201590022033/Dial-New-Design.01/docs/CROWN-RESUME-LEDGER-2026-10-09.md

# Crown continuation ledger

Updated: 10 October 2026, Africa/Johannesburg.

- Baseline HEAD: `6931131420adb5606323f8c8db54dc4c76604f8d` on main.
- Overall state: C0 COMPLETE WITH EXPLICIT EVIDENCE LIMITATIONS / C1 COMPLETE / C2 COMPLETE / C3 COMPLETE.
- Authority: human approved C0 followed by C1, requesting GPT-6.1 Sol light mode, then explicitly requested C2 and C3 followed by commit/push on 10 October. The coordinator cannot switch its own running model through available tools. No C4-C7 implementation, supplier onboarding, contacts, purchases or scheduler activation approved. C2/C3 were completed without new delegation.
- Plan: `docs/CROWN-ROADMAP-2026-10-09.md`.
- Scheduler ID: `resume-dial-designer-crown-roadmap`; status PAUSED, five-hour cadence. Not an active guarantee of restart.
- Research complete: movement/stem versus case-crown distinction, case-first default rule, archetype recommendations, supplied-package examples, U-BOAT cap/inner-crown distinction, repository architecture review.
- C0 gate completed 10 October 2026: NH05B primary stem 0351 247 and drawing v2 visually confirmed; NH35A/NH34A 0351 200 and VK63A 0351 177 primary drawings pinned. Eight embedded-head hashes/transformed bounds and structural exclusions reviewed. Supplier contents/variants/prices/stock conflicts recorded; NMK920 old sketch recovered but limited to external envelope, current SKU linkage and exact angle unknown. Front Engineering and front/side HD baselines captured for reference42/ladies34 in isolated localhost:3017 origin. Engineering has no side/crown viewport; documented baseline limitation accepted for C1, not a physical-fit pass. Missing case interfaces remain unknown.
- C0 durable evidence: CROWN-C0-EVIDENCE-2026-10-10.md, CROWN-C0-ASSET-INVENTORY-2026-10-09.md, CROWN-C0-SUPPLIER-EVIDENCE-2026-10-10.md and docs/research/crown-c0-2026-10-10/. Pre-C1 automated baseline: 4 files / 55 tests passed (parametricContracts, visualWatchAdapter, watchAssemblyArchitecture, visualAssetRegistry); no new-code verification claim.
- C1 gate COMPLETE: additive crown-spec/v1, crown-axis/v1 and crown-choice/v1 frozen in src/domain/crown/. Case owns canonical axis array; crown references axisId. Modern datum overrides inactive legacy crown anchor/angle/tube while preserving storage; absent modern data keeps existing precedence. Runtime uses Engineering frame; exported Y-up conversion is separately named. Assembly and embedded .dial validation reject ownership/reference/duplicate-head defects before hydration. Explicit reversible adapter preserves legacy dimensions/identities; no automatic migration. Contract changelog and migration matrix: CROWN-C1-CONTRACT-2026-10-10.md. C2-C7 NOT STARTED.
- Final verification, 10 October 2026: npm test -- --run passed 101 files / 826 tests (26 crown contract + 14 crown integration tests); npm run lint passed; npm run build passed including tsc -b. git diff --check and whitespace scan of all 24 changed/new TypeScript/Markdown files passed. Existing Three.js CommonJS deprecation, dependency comment annotation and bundle-size warnings remain non-fatal. Earlier 786/50/55 totals are historical, not substituted for current checks.
- C1 source files: src/domain/crown/{types,validation,axis,legacy,index}.ts; new assembly/crownAssemblyValidation.ts and visual3d/canonicalCrownAxis.ts; integration in assemblySerialization.ts, assemblyTypes.ts, catalogue/types.ts, parametric/placement.ts, projectFileService.ts, assemblyAnchors.ts and watchAssemblyToVisualModel.ts; crownContract.test.ts and crownAssemblyContract.test.ts. Production catalogue records, source GLBs and supplier records unchanged. C0 evidence/documents added; original planning documents retained with current authority/progress updates.
- New task requested: Project Crown and Namokimods. Portable context cache and per-milestone execution prompts prepared, including suggested 1-3 subagents, role/file ownership, applicable skills/tools, gates and handoff. Task creation/identity recorded below when confirmed.
- New planning task CREATED: Project Crown and Namokimods, thread `01a12229-68af-7e33-9201-87330c04d8b7`, host local. No saved repository projects were available; task is projectless planning with the exact existing repo path, not repository-linked. It is instructed to read/check context read-only and wait for C0/C1 approval. Origin heartbeat remains paused and has not been retargeted/duplicated.
- Off-axis research: existing NMK920 has a baked generic3h head and missing exact angle; live SKU differs from repo. Old external-envelope sketch recovered and bounded, with current variant linkage and hidden mating dimensions unresolved. Tandorio46.5 supplier states4h, but no genuine case-interface drawing recovered. Prices/time/stock conflicts retained in supplier evidence; no ZAR or SA shipping invented.
- Remaining limitations: no measured mechanical-fit certification, no modern crown UI/default resolution or mesh changes. Engineering has no side/crown viewport. Multiple-axis documents persist but the one-slot visual adapter omits the crown until later renderer support; unknown modern placement never falls back to invented coordinates.
- Next safe action: verify publication against origin/main, then await approval for the next milestone. C2/C3 completion and evidence are recorded in CROWN-C2-C3-HANDOFF-2026-10-10.md. Do not repeat completed C0 broad research without a named stale evidence gap. Scheduler remains paused; activation/retargeting needs separate explicit approval.
- Continuation rule: if approval absent or quota exhausted, do not start implementation or expensive repeated research. Stay quiet on unchanged state. If approved, resume next incomplete item with bounded agents, recording results before handoff.
- Publication: user explicitly authorized committing and pushing the complete C0-C3 checkpoint to origin/main. The baseline above is historical; verify current local and remote HEAD before continuation. Our temporary localhost:3017 baseline server was stopped after evidence capture. C3 used an isolated localhost:3018 origin. No scheduler action was performed.
- Historical planning QA: independent agent reviewed new prompts/cache/C7. Added serialized browser ownership and presentation-only acceptance for approximate axes. The original planning-only pass checked four Markdown files without application tests; the current C0/C1 verification above supersedes that checkpoint.

## Current C2/C3 checkpoint (supersedes earlier C1-only status)

- C2: six draft concept choices, crown-only search/Apply, saved-choice preservation, evidence-gated case/platform defaults, ten provisional archetype defaults, physical interface unknown/mismatch checks and independent finish. No production supplied-case bundle was newly verified.
- C3: six reproducible Blender GLBs with matching shaped fallback; independent asset eligibility; exact reviewed embedded-head suppression; original case hashes unchanged; corrected reference crown path. Custom/cap and off-axis supplier work remains later scope.
- Final checks: 103 files / 884 tests passed (40 C2 + 18 C3 additions); lint and production build including TypeScript passed. Current handoff contains screenshot paths, asset hash manifest, limitations and acceptance details.
- Browser: six front/side HD options, Search all, keyboard and double-click Apply and fresh ladies34 fixture passed with no browser errors. Engineering has no side/crown viewport. Multiple-axis rendering and measured mechanical-fit certification remain unavailable.
