201590022033/Dial-New-Design.01/docs/PROJECT-CROWN-CONTEXT.md

# Project Crown and Namokimods - portable context cache

Updated 10 October 2026, Africa/Johannesburg. This file is an explicit disk-backed handoff, not an internal model cache. Read the live ledger and Git state before trusting this snapshot.

## Authority

The user approved C0 followed by C1 in GPT-6.1 Sol light mode, then explicitly requested C2 and C3 followed by commit/push on 10 October. C0-C3 are complete; see the live ledger, C0 evidence, frozen C1 contract and CROWN-C2-C3-HANDOFF-2026-10-10.md. The coordinator cannot switch its own running model through available tools. C4-C7 implementation, supplier onboarding writes, contacts, purchases and scheduler activation remain outside this approval. Do not run later milestone prompts merely because they exist.

## Workspace and entry points

- Actual repository: `C:/Users/Deon/Documents/GitHub/Dial-New-Design.01`.
- Baseline: main, `6931131420adb5606323f8c8db54dc4c76604f8d`. Recheck current branch/upstream; never reset to this snapshot.
- Roadmap: `docs/CROWN-ROADMAP-2026-10-09.md`.
- Prompts: `docs/PROJECT-CROWN-MILESTONE-PROMPTS.md`.
- Mutable progress/authority: `docs/CROWN-RESUME-LEDGER-2026-10-09.md`.
- Origin chat: `01a0d901-31af-7ba0-84b9-0583808dd93f`.
- New planning task: `01a12229-68af-7e33-9201-87330c04d8b7`, local, named Project Crown and Namokimods.
- Task creation discovery returned no saved projects. A projectless planning handoff is not a repository-linked task; attach/open the real repository before implementation if the new task lacks access. Never operate on a same-named empty folder as if it were this repo.

## User's intended outcome

Case-supplied crown defaults per archetype, custom smooth/fluted/knurled/onion/compact dress appearances and supported closure/protection choices. Engineering and HD must agree, with independent crown finish and transparent BOM costs. Include complete off-axis Tuna case integration: supplier/exact variant, timestamped ZAR costs and SA shipping, dimensional/fit evidence, movement/dial orientation, UI options/Apply, Blender case/crown assets and automated/browser acceptance. Preserve all previous scale, lug, hand, finish, strap and BOM repairs.

## Original findings and current disposition

C2/C3 resolved findings 1-5 below: six concept choices, kind-safe Apply, shaped fallback, independent asset selection, corrected reference path and exact reviewed embedded-head suppression. The numbered descriptions retain the original diagnosis. Remaining physical and off-axis evidence gaps are still open.

1. Generic cat-crown is the only catalogue crown; broad external-category choice admits non-crown candidates. UI and domain must both reject wrong-kind Apply.
2. Generic six-starter crowns render smooth procedural cylinders despite knurled tags. Ladies uses compact dimensions but an embedded case head can duplicate a separately rendered head.
3. Reference crown eligibility is wrongly coupled to hand/reference assembly eligibility. Changing hands can drop a fluted crown to smooth fallback.
4. Registry crown-reference-v1 points to a missing generated file; actual reference-42/crown.glb exists. Nominal 7 mm core with 0.2 mm radial grip is 7.4 mm maximum OD, not 7 mm maximum.
5. Eight case GLBs contain DD_CASE_CROWN_PREVIEW. Suppress only reviewed removable heads, never legitimate tubes/bosses/guards/lugs. One operating head per axis.
6. Stem interface belongs to the movement, tube/guards to the case; final crown belongs to the case package/interface. Shared stem family or seller Tap label does not prove case interchangeability. C0 pinned primary NH05B 0351 247 drawing v2; NH35A/NH34A use 0351 200 and VK63A uses 0351 177. Case mating interfaces remain unknown; consult exact source revisions rather than generic seller stem labels.
7. Existing NMK920 generator bakes its crown at 3 o'clock. No exact crown angle exists in its catalogue entry. Coarse movement stemPosition enums and anchor precedence cannot represent all off-axis variants correctly.
8. Tuna cases are not one fit family: supplier-stated 3.8, 4, 4.1, 4.2 o'clock differ. Shroud OD is not bezel scale OD. Top-loading KARAJAN differs from rear-loading assemblies.
9. Namoki NMK920 current observed SKU NMK920-PL differs from repo NMK920-BRUSHED. C0 recovered an old external-envelope sketch; current SKU linkage, exact angle and hidden interfaces remain unresolved. Tandorio 46.5 at 4h is a candidate with no genuine case-interface drawing recovered; stock sources conflict.
10. Protected cap/holder is a case-level mechanism. Do not confuse a bezel lock with crown closure, or claim universal U-BOAT-like retrofit compatibility.

## Research and provenance

Three focused agents reviewed movement interfaces, case/style examples and repo architecture; one followed up off-axis Tuna candidates. Main visually inspected the official U-BOAT mechanism PDF using the PDF skill. Primary and supplier URLs plus timestamped observations are retained in the roadmap. Revalidate live prices before implementation; no Rand FX quote or SA delivered price has been invented. Do not redo completed broad searches unless stale or resolving a named gap.

Current implementation verification: 103 files / 884 tests pass, including 40 C1 and 58 C2/C3 additions; lint and production build (including tsc -b) pass. C0 has actual isolated browser baselines, primary drawing page inspections and eight embedded-head hashes/transformed bounds. Original case GLBs remain unchanged; six new crown GLBs and C3 browser evidence are retained. Engineering has no side/crown viewport; no full C6 visual-matrix claim is made.

## Execution and resumption

Sequence: C0 -> C1 -> C2/C3 -> C4 -> C7A-E -> C6. Optional C5 later. Maximum four active agents including main in the originating session; target 1-3 subagents based on independent work, not a mandatory quota. Shared contracts frozen before parallel edits. Main owns integration and assigns disjoint files; audit agents review independently after integration.

Paused origin heartbeat: `resume-dial-designer-crown-roadmap`, five-hour cadence. It is not active, not reset-synchronised, and does not bypass usage limits. Do not activate a second schedule or resume implementation without explicit human scope. If moving continuation into the new task, use the supported automation tool to update the existing schedule's target only after checking actual thread identity and approval. Do not leave both chats running code in the shared checkout.

At every stop write authority, completed gate, Git diff/files, source hashes, tests/results, known limitations and exact next action to the ledger. Recheck live usage when relevant; never promise quota capacity or auto-buy credits. Read all applicable AGENTS.md and selected SKILL.md instructions before work. Use PDF for drawings and computer-use for real browser acceptance, not as a claim that model assertions equal visual inspection.

Next safe action: read the live ledger, frozen C1 contract and C2/C3 handoff; verify current HEAD against origin/main for the authorized publication. Await approval for the next milestone. Preserve user work and keep scheduling paused.
