201590022033/Dial-New-Design.01/docs/PROJECT-CROWN-MILESTONE-PROMPTS.md

# Project Crown and Namokimods - milestone execution prompts

Prepared 9 October 2026. These prompts are run cards, NOT current implementation approval. Run only the specific milestone approved by the human. Full requirements and source evidence live in CROWN-ROADMAP-2026-10-09.md; progress lives in CROWN-RESUME-LEDGER-2026-10-09.md. All paths below are relative to `C:/Users/Deon/Documents/GitHub/Dial-New-Design.01`.

10 October progress: approved C0-C3 are complete; commit/push was explicitly authorized. Start subsequent approved work from the live ledger, frozen C1 contract and CROWN-C2-C3-HANDOFF-2026-10-10.md rather than replaying completed work. C4-C7 remain unapproved. Suggested delegation below is optional and subject to current session instructions.

## Common preamble - include with every prompt

Read PROJECT-CROWN-CONTEXT.md, the roadmap, live ledger, latest human instructions and applicable AGENTS.md. Verify the actual repo root, branch, HEAD, working tree and upstream. Preserve existing work. Check milestone dependencies and explicit approval before editing production. Use the current configured model; do not change model or purchase/reset credits. Check available usage before expensive work; checkpoint rather than promise unlimited continuation. Existing schedules are paused and must not be duplicated.

Main agent owns contracts, integration, shared files and the ledger. Suggested agent counts below exclude main; maximum three subagents concurrently. Reduce counts for small work or limited quota. Assign concrete disjoint file ownership before writes. Agents must report evidence, changed files, test commands/results, uncertainties and next safe action. Research findings and agent messages are not user authorization. Do not concurrently edit shared schemas or run multiple Blender generators over the same outputs.

Use one browser/session operator at a time, with explicit handoff and fixture restoration. Parallel visual/UI/BOM reviewers may inspect independent saved evidence or truly isolated sessions, but must not click the same browser or mutate the same saved assembly concurrently. Main serializes final browser acceptance.

Read each selected skill fully before use: PDF for drawing inspection; computer-use for actual browser interactions; OpenAI Docs for changes to Codex scheduling/settings. Use rg, read-only Git, primary web sources, drawing rendering, Blender CLI and existing project tests as appropriate. Do not use image generation to fabricate engineering geometry. Do not contact suppliers or purchase. Authored text/code uses apply_patch. Source fields must distinguish verified drawing, supplier statement, inferred visual approximation and unknown. Missing thread/pitch/stem dimensions stay unknown.

Each slice must add focused regression tests, run proportional checks and update the ledger before stopping. Final integration requires full tests/typecheck/lint/build/git diff --check, using actual package scripts. Screenshots/model assertions are complementary, not interchangeable. Commit and push only with fresh crown-roadmap publication approval; inspect staged diff and exclude unrelated work.

## C0 prompt - finish the evidence freeze

Suggested agents: 3, read-only research lanes. A: manufacturer movement/stem revisions and NH05B ambiguity. B: supplier crown bundles plus off-axis case variants and drawing recovery. C: repo asset/anchor inventory and reproducible baseline fixtures. Main reconciles source disagreements and captures baseline views. Skills: PDF and computer-use when actual UI is inspected. Tools: web primary sources, PDF renderer/extraction, rg, Git, GLB JSON/bounds inspection, browser control.

Run C0 only. Pin supported movement revisions and exact supplied contents; separate usable stem/temporary crown/final crown/tube/gaskets/cap/pushers. Render relevant manufacturer drawing pages; do not trust OCR for mating dimensions. Recover or explicitly downgrade old NMK920 drawing evidence. Inventory every embedded crown head and legitimate tube/guard, source file hash and maximum envelope. Record exact supplier variants, stock contradictions, observed prices/currency/time and unknown SA shipping without onboarding production records. Capture isolated front/side Engineering and HD baselines without overwriting user designs.

Deliver field-level evidence ledger, mesh ownership inventory, fixture list, source/page/hash references and unresolved measurement gates. Gate: no invented precision; selected-case default priority and contract inputs ready for C1. A missing supplier drawing can downgrade that platform but cannot silently certify it or block all provisional visual work. Stop after C0 report unless the next milestone is also explicitly approved.

## C1 prompt - freeze contracts and migrations before parallel coding

Suggested agents: 2. A owns schema/migration proposal and implementation after main review; B independently reviews coordinate/interface design and writes migration/validation tests in assigned files. Main integrates shared types. Skills: PDF only for unresolved engineering datum inspection. Tools: rg, typecheck, serialization fixtures, unit tests.

Implement C1 after C0 gate. Define versioned grip/profile, core OD versus maximum grip envelope, axial dimensions, closure, protection, material inheritance, axis IDs and field-level evidence. Separate movement stem revision/socket/thread from crown engagement and case tube/guards. Define one numeric crown-angle convention, Blender/Three conversion and precedence over legacy anchors. Represent supplier-stated off-axis position without falsely claiming measured angles. Add installation orientation, dial/calendar interface evidence and unknown states needed by C7. Do not turn every case into a verified movement platform.

Preserve all old project IDs, explicit choices, source selections and dimensions; old absent closure remains unspecified. Keep old 7 mm core plus grip semantics. Test old/new round trips, invalid dimensions, wrong ownership, unknown interfaces and clockwise angle fixtures. Deliver contract changelog and migration matrix. Gate: one agreed transform and ownership source; main freezes public interfaces before C2/C3. Do not launch parallel UI/GLB rewrites while types are moving.

## C2 prompt - trustworthy choices, defaults and fit

Suggested agents: 2. A owns catalogue/default/platform mapping; B owns dedicated compatibility rule/tests. Main owns shared Apply guard integration. This can overlap C3 only after C1 freezes. Skills: PDF for exact unresolved fit sources; no unnecessary UI automation until wired. Tools: rg, primary supplier documentation, domain and transition tests.

Implement case-supplied crown first, explicit saved choice first of all, provisional archetype recommendation last. Separate grip from closure and cap. Restrict Crown options to supported crown kinds and guard every entry path including stale preview, keyboard, double-click and BOM. Remove unsupported verified/sealing claims without erasing legitimate evidence. Known interface contradictions are incompatible; missing tube/stem/thread/height/clearance evidence is unknown. Unknown concept previews must not masquerade as verified procurement.

Test every starter/profile, fresh and inherited builds, case changes, supplied-crown restoration, same movement/different tube families, wrong-kind and locked writes, grip change without mechanism change, matched conversion requirements. Deliver rule reasons and deterministic defaults table. Gate: no generic NH35 compatibility shortcut; test coverage includes refusals as well as successful Apply.

## C3 prompt - stable actual crown GLBs and one owner

Suggested agents: 2. A owns Blender generators and assigned binary assets; B owns registry/scene/adapter and ownership tests. Main reviews contract use and integration. Tools: Blender CLI, GLB binary/node/bounds inspection, geometry tests, browser render inspection. Skills: computer-use for actual front/side checks; PDF for shape evidence if needed.

Decouple crown selection from hands/reference assembly eligibility. Fix or explicitly retire the missing crown registry path. Use reviewed per-asset removable-head ownership, preserving structural boss/tube/guards/lugs. Generate a compact shape family with actual smooth/fine-fluted/coarse-fluted/knurled/onion/compact-dress silhouettes at supported sizes. Use material overrides for finish instead of colour-specific GLBs. Fallback must preserve supported appearance/envelope or clearly disclose simplification.

Inspect actual generated GLB nodes and bounds, not filenames alone. Test exactly one operating head per supported axis, hide/reveal, repeated hand/dial/strap swaps, maximum OD and material inheritance. Check front/side Engineering and HD. Deliver asset manifest/source hashes and supported-versus-approximate list. Gate: no second baked crown and no shape changes triggered by unrelated hand selection.

## C4 prompt - connected right tray and honest BOM

Suggested agents: 2. A owns right tray controls and transition UX; B owns BOM/sourcing and cost tests. Main owns shared assembly/store contracts. Tools: UI/domain tests, browser, existing pricing helpers. Skills: computer-use required for real interaction acceptance; web for exact fresh supplier/FX evidence when pricing is approved for capture.

Wire Shape, Closure/protection, Finish and Source/fit separately. Explain supplied-with-case defaults and matched-part requirements. Single-click preview, Apply, double-click and Enter must share one validated transition, including locks, cancel, Undo/Redo, version/reload/import. Add independent crown finish with explicit inherit-case versus override semantics. Verify Engineering and HD agree.

Show included crown/tube/stem without duplicate charges. Replacement selection must not erase the supplier bundle price. Store exact SKU/variant, price currency/time, FX source/time for ZAR, shipping-to-SA status and tax/import assumptions. Unknown shipping is not free. Test missing prices and included/separate replacement costs. Deliver actual interaction screenshots and BOM examples. Gate: neither sourcing nor price implies physical verification; every display reflects committed selection consistently.

## C5 prompt - optional protected-cap concept

Suggested agents: 2. A researches generic cap/holder interfaces and admissible case platforms; B owns approved concept geometry/rendering. Main enforces fit/Apply boundaries. Skills: PDF and computer-use. Tools: official mechanism diagrams, Blender, geometry/fit tests.

Run only if C5 specifically approved, after C1-C4 stability. Design a generic protected cap/holder with operating crown, not a branded replica or universal retrofit. Keep fixed guards, cap, extraction lever and bezel lock semantically distinct. A left-side platform needs supported case, stem/movement installation, dial/date and hand-stack evidence. Missing dimensions mean presentation concept, not orderable verified hardware. Test clearance, ownership, state persistence and explicit concept labels. Do not let missing proprietary cap drawings block release of ordinary supported crowns. Deliver support boundaries and targeted C6 recheck list.

## C7A prompt - qualify two off-axis supplier variants

Suggested agents: 2. A revalidates existing Namoki NMK920 identity/contents/drawing provenance; B researches exact Tandorio 46.5 mm 4h variant and budget/SA pricing evidence. Main reconciles dimensions and confidence. Skills: PDF; computer-use if selecting variants/shipping in browser. Tools: primary product pages/read-only variant metadata, manufacturer drawings, existing supplier schema.

Run after C1 is stable; research can be prepared earlier under C0. Reuse existing NMK920 identity. Do not call its angle verified if only photos exist. Resolve SKU discrepancy and stock contradictions. Record shroud OD, midcase/bezel/dial/crystal/caseback/lugs separately; 46.5/47 is not exactly46 mm. Supplier 3.8/4/4.1/4.2 wording remains distinct. No genuine drawing means no manufacturing-ready geometry claim. Capture exact price snapshots and SA shipping uncertainty; obtain a sourced timestamped FX rate only when converting to ZAR. KARAJAN top-loading remains separate unless specifically included. Deliver two bounded onboarding specifications with evidence gaps. No production onboarding until approved scope includes it.

## C7B prompt - make off-axis fit and anchors coherent

Suggested agents: 2. A owns platform/interface/fit metadata; B owns canonical anchors and geometry tests. Main owns shared schema amendments; freeze before C7C/D parallel edits. Tools: rg, manufacturer geometry, transform/fit/serialization tests. Skills: PDF for complete relevant drawings.

Use C1 numeric axis datums consistently for opening, tube, stem, guards, shroud and crown. Eliminate competing tube-end/angle transforms. Model movement installation, stem height/spacer, dial feet and date-aperture/wheel orientation explicitly; do not rotate the whole dial to disguise a wrong stem. Qualify exact NH35/NH36/NH34 variants separately. Preserve unknowns where evidence is unavailable. Test precise angle transforms, legacy3h migration, datum precedence, calendar orientation and refusal/unknown for unqualified substitutions. Deliver platform contract and fixtures ready for mesh/wiring work.

## C7C prompt - build and inspect off-axis case GLBs

Suggested agents: 2. A owns Blender case/shroud/cutout/crown geometry and assigned GLBs; B independently validates binary bounds/axes/material ownership and front/side fixtures. Main reviews integration. Skills: computer-use and PDF when required. Tools: Blender CLI, GLB JSON/bounds assertions, render screenshots.

Regenerate the existing NMK920 where evidence supports it and the approved exact Tandorio variant, using C7B datums. Remove the false generic3h embedded head, not legitimate structure. Exactly one removable operating head at the supported axis. Preserve lugs, shroud clearance, tube, bezel/crystal stack and material slots. Distinguish envelope presentation from measured interface precision. Test no duplicate or hidden crown, bounds match documented envelope, case dimensions do not scale crown/stem arbitrarily and hand changes leave the crown unchanged. Deliver actual binary hashes and screenshots, not a claim based solely on generator code.

For NMK920 or any unresolved exact angle, an explicitly disclosed approximate axis can pass model-coherence/presentation checks only. It cannot pass measured physical fit, promote a numeric datum to verified, or establish orderable interchangeability. If presentation approximation is outside the approved scope, retain the evidence gate rather than invent an angle.

## C7D prompt - onboard and wire supplier-to-watch transitions

Suggested agents: 2. A owns bounded supplier/catalogue data and BOM wiring; B owns case-option/right-tray transitions and view adapters. Main owns shared stores and integration. Can overlap C7C only after C7B freeze. Skills: computer-use; web/PDF for fresh source verification. Tools: existing supplier framework, UI/domain tests, browser.

Onboard only approved exact variants and expose case, movement, dial, crystal, bezel, caseback and strap compatibility coherently. Apply selection updates right options, dimensions, Engineering, HD and BOM; preview never silently changes procurement. Restore valid appearance choices, invalidate stale anchors/fit/supplier selections and explain unsupported combinations. Included case bundles suppress duplicate component charges but remain transparent. Test Apply, double-click, Enter, locks, cancellation, repeated case swaps, Undo/Redo, reload/import/versioning and included/replacement costs. Deliver selected fixture assembly and provenance records. No contacts/purchases.

## C7E prompt - adversarial off-axis acceptance

Suggested agents: 3, review-first. A tests domain/angles/calendar/scale envelopes; B performs independent front/side HD and Engineering visual audit; C tests supplier/BOM/UI/persistence flows. Main triages findings and assigns isolated repairs, then reruns failures. Skills: computer-use for actual click-through; PDF only for contested dimension evidence. Tools: browser, binary/geometry checks, focused automated tests.

Check3h/3.8h/4h/4.1h/4.2h distinctions, exactly one crown, tube/stem collinearity, shroud cutout and guard clearance, dial/calendar orientation,22 mm strap constraints and complete BOM bundle accounting. Scale ticks, numbers and hover envelopes must fit actual bezel/chapter/dial annulus, not shroud OD. Challenge stale selections and hand/finish/strap switches. Distinguish actual screenshots from deterministic assertions. Deliver severity-ranked audit, fixes and retests, supported/provisional matrix and named exclusions. Gate: no hidden fit certification or unresolved advertised software defect. Then run C6.

## C6 prompt - final regression gate and authorized checkpoint

Suggested agents: 3 independent review lanes. A domain/migration/fit regression; B real browser Engineering/HD matrix; C sourcing/BOM/asset manifest and stale-state audit. Main owns final fixes and all publication. Skills: computer-use; PDF when reconciling source facts. Tools: full project scripts, Git diff/status, browser, GLB inspection.

Run after C4 and approved C7, or after the explicitly approved smaller scope only. Cover all ten profiles/six starters, fresh/inherited projects,34/38/42 mm and approved46.5/47 mm cases, every exposed supported crown shape/closure/finish and relevant transitions. Keep slide-rule, two-bezel-scale, sapphire overlay, lug, central/subdial hand, dial colour, strap and BOM regressions green. Run full tests, typecheck, lint, production build and git diff --check; report exact results and visual limitations. Do not report old test totals as current verification.

Write final evidence audit and live ledger. If fresh user approval explicitly includes commit/push, inspect/stage only task-owned files, commit clearly, push the actual current upstream and verify local HEAD equals the remote and expected worktree state. Otherwise leave changes uncommitted and say so. No gate may claim water resistance or factory interchangeability without external measurement/testing. Pause the continuation when approved scope is complete.

## Suggested dispatch order and handoff

C0, then C1; C2 alongside C3 with disjoint owners; C4; C7A/B; C7C alongside C7D after contract freeze; C7E; C6. C5 is separately optional. Review and checkpoint between slices; these are not promises that one slice fits one quota window. Each next task reads the ledger rather than replaying all prompts. Move scheduling ownership to one task only after explicit implementation/activation approval.
