201590022033/Dial-New-Design.01/docs/research/EXACT_DRAWING_CASES_2026-09-27.md

# Exact product-linked case drawings — 2026-09-27

Captured at **2026-09-27 18:30 SAST**. This replaces the earlier headline/style-matched case shortlist. A case is selectable here only when a dimensioned image belongs to the exact product or seller listing.

| Exact component | Product and price snapshot | Drawing evidence | Status |
|---|---|---|---|
| Tandorio 40.2 mm pilot case | Tandorio, US$44.58 | Product-hosted dimension drawing: 40.20 mm OD, 12.30 mm thick, 20 mm lugs, 33.5–34.3 mm dial | In stock |
| namokiMODS NMK920 Tuna | namokiMODS, S$195 | NMK920’s published dimension image: 47 mm including shroud, 46.5 mm lug-to-lug, 11.3 mm without caseback, 22 mm lugs | Sold out |
| FEIYASHI 43.8 mm Samurai | eBay item 188553207610, US$56.99 + US$40 shown worldwide shipping | Drawing in the exact listing: 43.8 mm diameter, 13.65 mm thick, 22 mm lugs, 28.5 mm dial | In stock; SA checkout still required |
| Tandorio CuSn8 44 mm bronze diver | eBay item 295218015063, US$111.29 | Technical drawing in the exact listing | Out of stock |
| WR Accessories 42 mm sandblasted SKX | WR Accessories, US$99.90 | Exact product drawing plus 31.5 mm crystal, 38/30.6 or 38/31.5 mm insert and 30.5/27.5 mm chapter-ring interfaces | In stock |
| Tandorio 41 mm Captain Willard | Tandorio, US$52.29 | Exact variant drawing: 41 mm body, 48 mm lug-to-lug, 12.7 mm thick, 19 mm lugs and 38/31.5 mm bezel interface | In stock |

## Evidence rule

The drawing and the price must resolve to the same product record. Similar-looking AliExpress cases, generic search photographs, and dimensions copied from an OEM watch do not qualify.

These drawings are sufficient for a **drawing-constrained visual GLB**. They are not manufacture-ready CAD because most omit hidden movement-holder, crown-tube, gasket, click-spring and tolerance details. A physical sample or supplier STEP/DXF/PDF section drawing is still required before labelling a GLB supplier-exact or suitable for fabrication.

## Cases deliberately not promoted

- NMK946 dual-crown diver: exact official product and useful overall dimensions found, but no dimensioned drawing of the case/inner-bezel mechanism.
- VK63 39.7/40 mm chronograph cases: exact product listings and overall dimensions found, but no adequate case drawing showing pusher locations and external profiles.
- Earlier 45–47 mm AliExpress headline matches: removed from the selectable catalogue because their indexed pages did not expose a matching drawing.

## Previous authoritative drawing source

The previous NH05 work used the movement manufacturer’s own TMI drawing pack, not a visual-reference photo. See `NH05_ENGINEERING_REFERENCE.md`. That source controls movement and casing-ring interfaces only; it does not define an aftermarket case exterior.
