201590022033/Dial-New-Design.01/docs/research/NH05_ENGINEERING_REFERENCE.md

# NH05 engineering drawing reference

Research checked: 2026-09-27 15:09 SAST.

## Authoritative drawing set

- [TMI NH05 product page](https://timemodule.com/en/product_line_up/mechanical/mechanical/mechanical_NH0_NH3/)
- [NH05B specification and drawing pack - 12 pages](https://timemodule.com/upload/category/21/spec_sheet/NH05_SS.pdf)
- [NH05 technical guide and parts catalogue - 13 pages](https://timemodule.com/upload/category/21/technical_guide/NH05_TG.pdf)
- [NH05/NH06 operation sheet](https://timemodule.com/upload/category/21/operation_manual/NH05_OM.pdf)
- [NH05 parts list](https://timemodule.com/upload/category/21/parts_list/NH05_PL.pdf)

The specification pack contains appearance, casing, hand fitting, hand-setting
stem, 3H and 6H dial drawings, casing-ring geometry, assembly plan, and hands.
It is the controlling source for the movement interface. Marketplace listing
headlines are not acceptable substitutes for these dimensions.

## Transcribed interfaces

| Interface | Published value | Design use |
| --- | ---: | --- |
| Movement outside diameter | 17.50 mm | Movement envelope |
| Casing diameter | 17.20 mm | Movement seat |
| Diameter with dial support | 19.80 mm | Retaining/casing-ring envelope |
| Movement height with dial support | 5.92 mm | Axial case stack |
| Total Type M height | 7.604 mm | Minimum internal stack before clearance |
| Maximum height above dial support | 1.684 mm | Crystal/hand clearance datum |
| Hour fitting | 1.10 mm | Hour-hand bore |
| Minute fitting | 0.656 mm | Minute-hand bore |
| Seconds fitting | 0.213 mm | Seconds-hand pipe |
| Maximum hand radius | 9.50 mm | Radial hand envelope |
| Official drawing dial OD | 19.00 +/- 0.05 mm | Manufacturer reference dial |
| Official dial thickness | 0.40 mm | Dial stack |
| Dial centre hole | 1.65 +/- 0.05 mm | Dial opening |
| 3H date aperture | 1.85 x 1.30 mm | Calendar opening |
| Stem part | 0351 247 | Replacement/assembly reference |
| Stem reference dimensions | A 5.71 mm; B 12.445 mm | Stem/crown development |

## Platform boundary

The proposed Ladies Dress archetype uses an aftermarket 24.5 mm dial and a
nominal 34 mm case. Those are not TMI dimensions. They remain provisional until
an exact seller drawing or a measured golden sample supplies the case cavity,
dial seat, crystal seat, crown-tube centreline, lug width and gasket geometry.
The TMI drawing explicitly describes casing-ring retention; it must not be
treated as evidence that an arbitrary NH05 marketplace case is compatible.

The official NH05 drawing also shows a 19.00 mm reference dial. A 24.5 mm dial
may be used only when its NH05-specific feet/date aperture and the chosen case
dial seat are confirmed. The library therefore records 24.5 mm as a platform
choice, while preserving 19.00 mm in the manufacturer engineering reference.
