201590022033/Dial-New-Design.01/docs/MILESTONE-PROMPTS-HYBRID-SLIDE-RULES-2026-10-07.md

# Consolidated milestone prompts: hybrid dashboard and faithful aviation scales

Prepared 7 October 2026. This is a runnable plan, not a claim of completed implementation. Run one milestone per chat turn; review its checkpoint before requesting the next. Milestone 3 has two separately runnable preset substeps.

Updated 7 October 2026 after the typography/PDF review. The user has authorised Milestones 0 and 1, continued graduation verification, a separate 1967 Navitimer plan, and the START of Milestone 2. Later milestones remain gated; GLB regeneration waits for shared artwork/appearance dependencies.

Follow-up: the user subsequently authorised finishing M2. Canonical runtime editing, target envelopes, Simplified controls and shared live/export consumers have now been wired and tested. See the updated M2 checkpoint for evidence and explicit remaining acceptance gaps (source inventories, pointer/hover models, source typography and composite multi-layer rendering). Do not treat this runtime checkpoint as permission to claim source-exact artwork or M3A completion.

Completion follow-up: source-neutral pointers/hover fit, persisted resolved typography records, composite active-layer rendering and strict invalid-fit export refusal are now implemented (508 tests). The source-independent M2 runtime foundation is complete. M1 source inventories/original fidelity remain unaccepted, so original presets and M3A faithful artwork are still gated. See the final section of the M2 checkpoint; earlier partial-checkpoint gaps are historical, not current missing runtime implementation.

Citizen verification follow-up: the published native Canada1600/Europe2000 images now support all52 Citizen sectors and450 graduation positions, measured profiles, corrected unit boxes/pointers and ratio-constrained distance placement. [Citizen reference verification](CITIZEN-VERIFICATION-2026-10-07.md) is accepted for the next M3A implementation with disclosed photographic approximations. It does not enable the application preset or certify a factory-exact reproduction.

8 October Navitimer follow-up: three independent outer/inner/source tasks and root reconciliation now support all56 selected training-disc sectors and420 graduation positions (210 per ring). [Navitimer reference verification](NAVITIMER-VERIFICATION-2026-10-08.md) records corrected pointer/caption identities, separate colour roles, native JPEG provenance, coarse typography/tick profiles and source-model sensitivity, including a failed withheld geometry check. Both reference inventories are ready for disclosed reconstruction; factory fonts/inks/physical print dimensions and runtime fidelity remain unaccepted. Earlier mentions of uncounted inventories below are historical. M3A Citizen implementation is the next milestone; M3B consumes the separate Navitimer packet afterwards. Neither renderer nor branded runtime gate was changed by this verification.

8 October M3A implementation: [initial Citizen geometry checkpoint](M3A-CITIZEN-IMPLEMENTATION-2026-10-08.md) adds the450-position runtime generator and11 regression tests (548 total). Controls, persisted-state integration, live/export adapters and visual acceptance remain pending. Both original presets remain disabled; this is not M3A completion.

## Typography and simplified-design addendum

### Accepted practical-design standard — 8 October 2026

The user accepts substitute fonts and an independent, reference-inspired design; factory-exact reproduction is not a completion requirement. This supersedes earlier exact-font/fidelity gates throughout this plan. Milestone3B is complete under this standard. Record source approximations as provenance, not recurring blockers. Do not claim factory identity or legal clearance.

Keep functional/manufacturing checks: calibrated logarithmic positions and distance ratios, correct printed values, millimetre export dimensions, actual glyph fit, no collisions/overflow, independent saved state and consistent rendering/export. For laser preparation, convert the selected font's SVG text to outlines in the manufacturing application, verify the resulting dimensions and legibility at1:1, assign engraving versus cutting operations explicitly, and make a material/kerf test. These are production preparation steps, not reasons to reopen3B over unavailable original font files. Automatic text outlining is not currently implemented.

Preserve **Simplified** as a third, explicitly non-original design, alongside Citizen Skyhawk and Classic Navitimer. The three designs are mutually exclusive on the same band; disabled is a separate state. Migrate existing generic aviation projects into Simplified without silently replacing their geometry, font, density or appearance. Preserve independently edited settings when switching designs.

The initial PDF review found tangent-following number rows, several graduation-length levels, abbreviated printed values, and separate time/reference rows. Citizen U680 printed pages 81-91 correspond to zero-based PDF indices 81-91 (viewer pages 82-92). Its generic diagrams verify operation, not JY8078-01L artwork. The classic Breitling booklet is a 17-page image scan; its training-disc illustration and operational examples are evidence, but not proof of a specific watch model, exact ink hex values, or original font files. A complete per-mark inventory is still required in Milestone 1.

Record each numeral's anchor relative to its exact graduation: baseline/cap-height bounds, radial gap from the tick endpoint, text alignment, tangent rotation, inward/outward facing direction, letter spacing, weight, width/condensation and any source-evidenced angular offset. Do not auto-flip bottom-half lettering unless the chosen original does. Separate mathematical value, printed text and label anchor; never shift the graduation to compensate for type width. Replace generic fixed offsets and collision-driven omission for reference-based artwork. Use actual resolved font/glyph bounds for fit, with disclosed substitutions where original fonts are unavailable. Ensure Engineering, HD textures and every export use identical text transforms, font metrics and colours.

Simplified must have working right-side controls for outer/inner numeral rows, supported captions, time-row writing, retained distance-reference writing and minor-label/detail density, scoped to what actually exists in that design. Distinguish hiding text from hiding an entire tick/pointer group; keep calibration geometry unchanged when omitting writing. Preserve critical unit/hour references by default, explain loss of readability when hidden, and label modified original artwork as adapted rather than faithful. Do not offer dormant placeholders for absent features. Test every exposed control in both directions, save/load, Undo, preset switching, HD and exports. The branded weight/volume exclusions remain mandatory and cannot be restored by these controls.

Acceptance additions: compare number-to-tick gaps and orientations around the full circumference; retain underlying values for abbreviated numerals; no auto-omission of required original labels; changing writing visibility preserves all retained graduation angles; visible controls produce a real state/render/export change.

## Five-hour work windows and restart checkpoints

Priority windows: (1) baseline repair and evidence; (2) source inventory and typography specification; (3) shared state/math/type rendering and Simplified migration; (4) Citizen and its controls; (5) Classic Navitimer and switching; (6) hybrid inspector and functional writing controls; then custom aviation, lume/GLBs and final acceptance. A large window may finish only part of a milestone; a small one may finish early. These are workload priorities, not five hours of guaranteed runtime or a fixed token estimate.

Before continuation, read the ledger and Git diff and check the actual account usage/reset time. Reserve capacity for focused checks and a written checkpoint. Record files, commands/results, source gaps, next action and uncommitted status before stopping. Do not begin a second major refactor without room to verify it. An exhausted allowance is a reason to checkpoint, not to bypass gates or claim success. No recurring automation has yet been created; a proposed wake-up time is not a scheduled job. Do not bypass computer-use safety restrictions to obtain screenshots.

## Requirements and precedence

1. [Exact pasted user prompt — preserved verbatim](SLIDE-RULE-EXACT-USER-PROMPT-2026-10-07.txt): all 13 sections and Delivery remain acceptance requirements, including every numerical test. Read it completely at the start of relevant milestone work.
2. [Broader hybrid-dashboard audit](HYBRID-DASHBOARD-AVIATION-AUDIT-2026-10-07.md): retain UI, rendering, decimal-hour, knots/MPH, lume and hand-tip scope, except where superseded by item 1.
3. The original mock-up is a UI/style reference only. It cannot establish calibrated graduations, branding, physical fit, exact fonts or original brand colours.

The latest prompt supersedes generic subdivision schedules, universal red/yellow assumptions and optional weight/volume conversion markings in the previous proposal. Citizen and Navitimer are separate, reference-specific presets; no mixing models/generations. New custom scales are independent layers, not modifications to the retained original artwork.

The exact user's prompt is a requirements document for future milestones. Its instruction to implement fully does not turn the present consolidation request into permission to start all application work now.

## Shared master prompt — apply to every milestone

> Work in the existing Dial Designer repository at `C:/Users/Deon/Documents/GitHub/Dial-New-Design.01`. Read the exact slide-rule requirements and consolidated audit documents linked above completely. Implement only the milestone explicitly requested in this turn. Inspect current code, Git status and applicable repository instructions first; preserve unrelated user changes. Follow the existing components, physical millimetres, authoritative assembly state, guarded Preview/Apply, geometry, sourcing and export architecture.
>
> Keep Build/Parts/Style/Research/BOM/Manufacture/Advanced navigation, versions, Undo, Engineering/HD switching and physical compatibility guards. Use one persisted component/layer configuration and one calibrated artwork model across Engineering, HD and all exports. Never certify supplier fit from visual appearance or resize a purchased case silently. Every tick, label, pointer and hover envelope must remain within its selected component's printable annulus without moving mathematically defined angles.
>
> Citizen Skyhawk and Classic Navitimer must be mutually exclusive per slide-rule band. Original Colours and Reset to Original use the chosen reference's retained artwork, not a generic accent palette. Custom Colours is explicit and reversible. Permanently exclude all weight, volume and fuel/oil-weight conversion annotations/pointers/supporting rows specified in the exact prompt from both presets, options, saved/restored state and exports; retain coincident ordinary numeric ticks/labels and leave gaps unchanged. Preserve the same exclusions on reset and reference migration.
>
> Preserve Simplified as an independently configured, non-original third design. Follow the typography and simplified-design addendum above, including number-to-graduation alignment and functional writing visibility controls. Never silently upgrade existing simplified projects into branded presets or expose unwired placeholder controls.
>
> Research references when that milestone requires it. Record model/layout, source URL, image/manual page and evidence for each graduation and colour. Distinguish exact source specifications, measured/reference-derived approximations and unknowns. Implement verified elements without inventing missing details or claiming exact fidelity. No brand logos, wings, Blue Angels insignia, unrelated digital displays or watch graphics.
>
> Add focused regression tests and verify proportionately. Use the computer-use skill for the UI acceptance work and the PDF skill when inspecting reference manuals. Run full tests/typecheck/lint/build/diff check at the relevant gates. If resources prevent verification, record the failed/unfinished checks and do not label the milestone accepted. Do not close user apps, change system memory settings, contact suppliers, buy anything, commit or push unless separately requested.
>
> At the end, report files changed, reference/evidence status, tests actually run, screenshots where relevant, known limitations, uncommitted status, and whether the gate passed. Update this milestone ledger with evidence, not just a completion checkbox. Stop after this milestone; do not start the next without another request.

## Milestone ledger

| Milestone | Scope | Status |
| --- | --- | --- |
| 0 | Baseline verification and regression checkpoint | Baseline audit complete: three scoped repairs; 445 tests/typecheck/lint/build/diff passed; live controls, four archetype screenshot pairs, Open/Import/reload checked. Known limitations recorded, not redesign acceptance. See [checkpoint](MILESTONE-0-BASELINE-2026-10-07.md) |
| 1 | Reference selection and full graduation/typography inventories | Both selected inventories accepted for disclosed reconstruction: Citizen52 sectors/450 positions; Navitimer56 sectors/420 positions. Factory font/ink/mm and exact source geometry remain qualified; runtime/factory gate false. See [Citizen checkpoint](CITIZEN-VERIFICATION-2026-10-07.md) and [Navitimer checkpoint](NAVITIMER-VERIFICATION-2026-10-08.md) |
| 2 | Per-band state, Simplified migration, mathematics, typography and shared artwork | Source-independent software foundation complete and committed as adf2fb3;508-test baseline. See [checkpoint](MILESTONE-2-FOUNDATION-CHECKPOINT-2026-10-07.md). Reference research does not enable branded runtime presets |
| 3A | Citizen Skyhawk preset and Advanced controls | Runtime/state/shared-export wiring complete;568 tests and browser40/42mm checks. Disclosed font/ink/radial/readability limits remain, not factory certification. See [checkpoint](M3A-CITIZEN-IMPLEMENTATION-2026-10-08.md) |
| 3B | Classic Navitimer preset and comparison | Functional runtime/state/shared-export wiring complete with independent420-position training-disc inventory and Engineering/HD checks. Disclosed font/ink/anchor/readability limits remain; separate1967AOPA variant is not verified/replaced. See [checkpoint](M3B-NAVITIMER-IMPLEMENTATION-2026-10-08.md) |
| 4 | Hybrid shell, contextual inspector and fully wired writing/detail controls | Implemented and published as 531bf2f; visual exception repairs verified in the follow-up checkpoint. See [repair checkpoint](M4-VISUAL-REPAIRS-2026-10-08.md) |
| 5 | Custom decimal-hour / knots-MPH and rate calculators | Implemented and pushed as 6c7204d on 9 October; 701 tests/typecheck/lint/build/diff checks and Engineering/HD acceptance passed. A true-size laser worksheet is now prepared separately. See [checkpoint](M5-CUSTOM-AVIATION-2026-10-08.md) |
| 6 | Lume modes, hand tips and targeted GLB work | Supported semantic appearance implemented: canonical saved marker/main/register regions, real hollow geometry and bounded tips, capability gates and day/night preview. Existing 22 GLB binaries preserved. See [integrated checkpoint](M6-M7-INTEGRATED-ACCEPTANCE-2026-10-09.md) for actual checks and limitations. |
| 7 | Full browser, export and cross-archetype acceptance | Integrated software checkpoint with corrected fit/Apply transitions, shared locks, positive BOM/Options Apply, saved-version durability, appearance UI and vector-fixture evidence. Physical laser proof and browser download round-trip remain qualified; not unconditional release sign-off. See [current ledger](M6-M7-INTEGRATED-ACCEPTANCE-2026-10-09.md); [initial audit](M7-FINAL-ACCEPTANCE-AUDIT-2026-10-09.md) retained as historical evidence. |

### Milestone 0 prompt — establish a trustworthy baseline

> Apply the shared master prompt and complete Milestone 0 only. Verify the current repository and the previously pushed strap/double-click update (`2fc7038`, if still applicable). Run tests, typecheck, lint, build and diff check, sequentially if memory is limited. Investigate genuine failures and fix only scoped baseline regressions. Use computer-use to verify strap switching in both directions, right-side single-click preview/double-click Apply/keyboard Apply, component locks and compatibility refusal. Capture Engineering and HD baseline screenshots for ladies dress, pilot, diver and chronograph presentation. Check BOM Apply, saved projects and Undo remain intact. Record actual device/resource limitations and save a non-destructive baseline checkpoint. Do not begin the redesign or push.

Gate: baseline evidence recorded; no unexplained render/geometry regression. If memory or a missing browser prevents checks, distinguish blocked checks from passing tests and identify what must change before acceptance.

Milestone 0 carry-forward: scale colour currently survives archetype changes independently of the assembly, so dark markings can disappear on a dark bezel; pale hour markings have poor contrast on pale dials. Treat these as recorded state/contrast work for Milestones 2/4, not proof of correct original artwork. The version filmstrip is session-only and does not survive reload/HMR; use project export for durable checkpoints until version persistence is explicitly repaired. The exported pre-audit project was restored, and browser Open/Import/repeat Import were verified after their file-input cleanup fix. See the baseline document for evidence and constraints.

### Milestone 1 prompt — choose originals and inventory every mark

> Apply the shared master prompt and complete Milestone 1 only. Research Citizen Blue Angels Skyhawk JY8078-01L at `https://www.citizenwatch.com/ca/en/product/JY8078-01L.html`. Use Citizen U680 instructions at `https://www.citizenwatch-global.com/support/pdf/u680/e.pdf`, printed pages 81–91, for operation, not as proof of this model's exact artwork. Inspect the PDF with the PDF skill; record the correspondence between printed and PDF viewer pages. For Classic Navitimer, inspect the user-specified booklet `https://www.breitlingsource.com/images/manuals/slide-rule.pdf`, then select and record one specific classic original model or illustrated layout with a sufficiently clear source. Prefer official model/vector evidence where available; do not mix vintage graduations with modern styling.
>
> Inventory the complete circumference separately for each preset: stable mark ID, underlying value, printed text, ring/row, tick class, interval schedule, tick width/length/direction, pointer geometry, text and pointer colours independently, radial location, typography/orientation and evidence. Record all interval changes and count subdivisions between labelled values. Distinguish retained marks from dedicated excluded annotations, even when they share a value. Record uncertainty/confidence and original physical dimensions versus measured proportions. Verify whether the time row and fixed 36-seconds reference actually occur. Save reference manifests, source links and a machine-readable inventory plus a readable comparison. Do not claim exact photographic colours/fonts and do not implement speculative missing marks.

Gate: one chosen reference per preset; independently evidenced inventory with known gaps. Exact-reference mode must not be called faithful while a significant unresolved subdivision/layout gap remains. Do not stop all progress merely because an unavailable font/colour specification requires an approximation, but track that limitation explicitly.

### Milestone 2 prompt — build the shared calibrated foundation

> Apply the shared master prompt and complete Milestone 2 only, using Milestone 1 inventories. Add versioned, persisted scale-layer state keyed to physical band/component IDs. Each slide-rule band has Simplified, Citizen, Navitimer or disabled selection, never multiple designs overlaid. Preserve each design's edited settings when navigating away; retain an immutable original configuration for Reset to Original. Migrate old generic projects to Simplified without silently changing their watch. Persist reference ID, colour mode, overrides, writing/group visibility, dimensions, row positions, typography metrics/anchors and bezel angle.
>
> Generate both main rings with `angle = origin + direction * 360 * log10(value / 10)`, with the same origin/increasing direction and separate radii; apply only relative outer rotation to rotating groups. Cover one decade with no duplicate 100/10 tick. Underlying values are separate from abbreviated printed labels. Time-row labels use actual minutes and decade normalization, not decimal-looking HH:MM text. Distance ratios use exact 1.609344km/statute mile and 1.852km/NM. Build full mark-level style/pointer models and one resolved artwork pipeline for Engineering, HD and vector exports. Reconcile the existing separate aviation SVG path. Apply per-target envelopes to both inner and outer rows and bind HD print to physical component surfaces, not a screen overlay.
>
> Exclude forbidden annotations by semantic identity and classification, not by deleting every nearby number. Add negative tests for all spelling/punctuation variants, Reset to Original, migration and export. Keep remaining values, angles and gaps unchanged. Do not shift calibration marks for collision avoidance; report an overfull printable surface and offer a clearly non-original adaptation rather than mislabel it original.

Gate: exact-prompt mathematical checks and state/exclusion tests pass; old documents migrate; rotation does not move fixed groups; resizing text/strokes/radii preserves values and mathematical angles; no outer-edge spill or hidden inner ring. Standard semantic roles support per-mark overrides but must not erase brand-specific colours.

### Milestone 3A prompt — deliver Citizen and the Advanced workflow

> Apply the shared master prompt and complete Milestone 3A only. Implement the verified JY8078-01L retained marking inventory. Add the two visually checkbox-style selections under Advanced on the LEFT, targeting the current slide-rule band, and immediately update preview and configuration on the RIGHT. Citizen selection unticks Navitimer; unticking Citizen disables that band's marks. Reopening Advanced restores the current configuration. Make keyboard/accessibility behaviour coherent with the visually requested mutually exclusive checkboxes.
>
> Provide the exact prompt's grouped right-side controls: selected marking system, reference identity, default Original Colours, explicit Custom Colours, outer/inner visibility, original time-row visibility where present, retained distance-reference visibility, dimensions/radii, label size, tick/line scale, bezel angle and Reset to Original. Retain dark inner10 in its yellow box, hollow hour-rate60 index (no literal SPEED INDEX caption), separate yellow KM/red NAUT/red STAT pointers and their light lettering. Selected JY8078-01L has no HH:MM or dedicated36 row; do not expose absent features or excluded conversions. Preserve source-specific shortened strokes near excluded NO/RX without inventing long replacements. Display measured/approximate evidence accurately. Capture the Advanced controls and a complete Citizen-to-original comparison, including the exclusion gaps.

Gate: all exact-prompt Citizen/UI requirements pass; original colour role differences survive reset, save/load and export; outer numerals, ticks, pointers and text rotate together while fixed elements stay fixed. No brand/dial graphics are copied.

### Milestone 3B prompt — deliver Classic Navitimer

> Apply the shared master prompt and complete Milestone 3B only. Implement the single chosen classic Navitimer retained inventory from Milestone 1, using the shared foundation and Advanced controls from 3A. Individually verify inner 10, outer 10, outer 60, MPH pointer/text, KM pointer/text, STAT, NAUT and seconds reference colours. Include the fixed 36-seconds reference and original time row only if the chosen original contains them. If MPH is at 12 o'clock in that reference, place numerical 60 precisely there by the correct origin. Do not impose the mock-up's red markings or combine old/new layouts.

Reference handoff: use `navitimer-training-disc-verification.json`, not the Citizen subdivision table or1967cover. Retain210 positions per ring, tangent-centred numeral runs, literal inner7/8/9, major unlabelled65/75/85/95, black solid outward MPH60 and red solid outward fixed10/distance/seconds pointers. Fixed36 has no caption; ordinary35 remains. Keep the unlabelled red rotating reference near36 as an observed footprint without inventing an operational label. Outer10/60 retain one numerical station plus a composite red inward pointer footprint; ambiguous hidden black underlays are not exact factory omissions. Sampled RGB, substitute fonts and pointer/radial registration must be disclosed as reconstruction targets. Apply exact distance ratios as one group; packet-fitted KM61.205 and alternative60.818 show sensitivity, with recommended nominal KM61±1 rather than factory precision. The photograph's outer phase≈−29.05° is evidence registration, not a silently imposed runtime zero. No HH:MM row exists on this selected disc. Live/export comparisons and valid physical target/glyph envelopes must pass before enabling the preset; research readiness alone does not enable it.
>
> Verify preset switching in both directions, per-band isolation, unticking, resetting and reopening Advanced. Compare every subdivision, retained label and pointer around the complete circumference with the selected source. Repeat exclusions in live views and every export. Record unresolved photographic/font limitations and ensure controls never claim unsupported exactness.

Gate: Navitimer calculation/visual/state requirements pass without regressing Citizen. Different brands retain different schedules, colours and orientations rather than sharing an invented generic artwork table.

### Milestone 4 prompt — build the hybrid dashboard and inspector

8 October completion: [Milestone 4 checkpoint](M4-HYBRID-DASHBOARD-2026-10-08.md) records the original hybrid dashboard implementation, published as `531bf2f`. The [visual repair follow-up](M4-VISUAL-REPAIRS-2026-10-08.md) records subsequent verification and remaining physical manufacturing checks. M5 has not started.

> Apply the shared master prompt and complete Milestone 4 only. Implement the audit's top diameter slider + typed mm field, compact thumbnail component navigator, selected-ring highlight, contextual right-hand inspector, texture thumbnails/direction where applicable, editable/copyable validated hex fields and finish close-up. Keep the established workflow rail and procurement/design checks. Respect ladies and larger cases instead of hard-limiting everything to the mock-up's 38–44mm range. Clearly distinguish resizing a custom preview from buying a physically different supplier case.
>
> Use the mock-up's `#1A1D24`, `#F0F0F0`, `#E63946` as UI/custom-theme references, never to overwrite Original Colours on either brand preset. All component thumbnails, selection contexts and physical measurements derive from the authoritative assembly. Keep the Advanced checkbox/config workflow visible and functional; do not create a competing legacy sidebar. Reuse existing export services for toolbar shortcuts and preserve guarded preview, double-click Apply, keyboard access, BOM and Undo. Test responsive laptop and narrow layouts.
>
> Implement the addendum's right-side Simplified writing/detail controls using persisted mark/group visibility from Milestone 2. Audit existing placeholder options and either connect them end-to-end or remove/clearly disable them with a reason. Verify real controls through user interaction, not just matching source-code strings. Reference-based adaptations must remain distinct from Reset to Original and may not reintroduce excluded annotations.

Gate: no disconnected controls; actual selected component and right inspector agree; ring selection is visually clear; branded originals retain their palettes; existing workflows remain reachable and usable.

### Milestone 5 prompt — add custom aviation layers and calculators

> Apply the shared master prompt and complete Milestone 5 only. Add separately labelled custom chapter-ring programs for Decimal hour (0.00–1.00h) and Knots / statute MPH. These must not be presented as original Citizen/Navitimer time rows or modify those inventories. Use 100 graduations per hour, 0.01h = 36 seconds, major 0.10h labels, one origin seam and explicit whole-hour handling. Test 6min=.10h, 15=.25h, 30=.50h, 45=.75h, 60=1h, 1h30=1.50h and 10min≈.17h. Explain that a one-revolution seconds hand is not an hour timer and this is not automatic Hobbs/logbook recording.
>
> Implement direct paired kt/mph readings using factor 1852/1609.344 and its reciprocal; test 100kt≈115.08mph and 120kt≈138.09mph. Keep fixed linear conversion and logarithmic distance-index geometry distinct. Extend existing rate arithmetic for fuel used, burn rate, endurance and speed/distance/time, without adding the forbidden weight/volume marking groups to either branded preset. Handle HH:MM as duration, not decimal hours. Allocate printable rows per component; refuse/warn about impossible coexistence instead of silently overwriting an original fixed scale. Custom layers must be separately switchable/exportable and cannot reintroduce excluded branded annotations.

Gate: precision/rounding and reverse-conversion tests pass; custom/original state remains distinct; source units are explicit; collisions and annular fit are checked; no silent invented original feature.

### Milestone 6 prompt — lume, tips and targeted GLBs

> Apply the shared master prompt and complete Milestone 6 only. Add coherent Filled / Outline / No Lume options and independent metal, print, lume and tip colours. Implement red-tip options with exact editable hex and physical tip-length controls for main and subdial hands. Preserve all physical lengths, bores and movement-owned register positions, particularly NH05 5/8/8mm sets. Audit GLB node/material naming first; wire existing distinct regions where possible and update Blender generators only for families needing separate tip regions or actual outline-lume geometry. Keep component-bound live scale artwork shared with exports; do not create a GLB per palette or reintroduce baked duplicate scales.
>
> Do not present material tint as actual hollow lume geometry, proprietary lume performance as verified, or chronograph/flyback support for an incompatible movement. Compare Engineering/HD in both switching directions and daylight/night preview. Record any provisional asset limitations.

Gate: settings persist and agree across views; main and subdial controls are independently scoped; geometric lengths/fit evidence remain unchanged; no stale material or hidden hands after repeated changes.

### Milestone 7 prompt — final acceptance audit and handoff

> Apply the shared master prompt and complete Milestone 7 only. Read every prior milestone's evidence and unresolved limitations. Run every calculation, interface and visual check in section 13 of the exact user prompt, including its literal test vectors; interpret the read mantissa/order of magnitude correctly rather than rewriting ambiguous displayed numerals. Check logarithmic ratio invariance: 20→40 equals 30→60, approximately 108.371 degrees. Check the stated statute/NM/km conversions using exact constants. Check HH:MM positions for 70/80/90/150/180 minutes.
>
> Use computer-use to audit left and right controls, mutual exclusivity per band, reopening Advanced, switching brands, unticking, Original/Custom Colours, row visibility, rotation, Reset to Original, single/double-click/keyboard Apply, locks, Undo/Redo, BOM Apply and save/load. Compare both branded renders beside their individual original sources around the entire circumference. Confirm exclusions and unchanged remaining artwork after reset and export. Verify SVG/DXF/PDF vector paths, dimensions, widths, labels, colour/material layers and fonts; clearly state any format limitations instead of claiming unsupported colour fidelity. Check intended 34/42/46mm fixtures and reject unreadable/overfull originals rather than distorting mathematical geometry.
>
> Run full tests/typecheck/lint/build/diff check and fix in-scope regressions. Deliver screenshots of Advanced on the left/configuration on the right, side-by-side reference comparisons, exact reference identities, measured verification results, source-derived approximation limits and a clean acceptance ledger. Leave changes uncommitted unless the user separately requests commit/push.

Gate: all requirements traceably tested or explicitly listed as unresolved. “Implementation complete” and “exact reproduction proven” are different claims; do not substitute passing unit tests for visual/reference fidelity.

## Traceability and restart rules

- Exact prompt §§1–2: milestones 2, 3A, 3B, 4, 7.
- §§3, 5–8: milestones 1, 3A, 3B, 7.
- §§4, 9–12: milestones 2, 3A, 3B, 7.
- §13 and Delivery: milestone 7, with focused checks in every earlier milestone.
- Larger audit: baseline 0; shared state/render/export 2; hybrid UI 4; new aviation options 5; lume/tips/GLBs 6.

After interruption, read the ledger and Git diff, resume the incomplete milestone, and preserve its tested work. Do not restart all earlier milestones or assume a previous push proves the new acceptance tests. Source gaps block exact-fidelity claims, not honest implementation of verified elements. Resource failures block verification claims, not safe documentation work.

To start, ask: **“Run Milestone 0 from the consolidated slide-rule plan.”** To continue, name the next milestone explicitly. Each prompt above is intended to be used with the shared master prompt and linked requirements, not in isolation.
