201590022033/Dial-New-Design.01/docs/M3A-CITIZEN-IMPLEMENTATION-2026-10-08.md

# Milestone 3A: Citizen implementation checkpoint

8 October 2026. **Initial geometry stage only, not Milestone 3A completion.** The user chose Sol 6.1 Medium and authorised credits, with an initial working target of approximately20 credits (not a billing cap).

## Implemented

- Compact runtime inventory independent of research JSON/images: all450 verified identities, values, profiles, classes, directions and printed/absent numerals. Tests compare every record against the frozen packet.
- Photographic tick-profile midpoints converted with explicitly supplied source-pixel-to-mm reconstruction scale, not factory dimensions. Seven radio-clearance exceptions remain without copying radio text.
- Outer60 owns one triangular graduation; no duplicate ordinary line. Separate shortened inner60 remains. Five pointers preserve hollow rate60, outer60 and distinct distance references with exact ratios and fitted photographic anchor. Only outer artwork rotates.
- All51 numeral runs have individual logarithmic anchors, row font sizes, full-run bounds and unit-box metadata (dark outer10 on light; dark inner10 on yellow).
- All12 photographic colour roles stay separate. Custom overrides do not mutate Original; regenerating Original resets colours.
- Outer/inner/distance visibility does not delete source inventory or ordinary36. No HH:MM or literal SPEED INDEX caption is invented.
- Strict physical-envelope checks reject overfull geometry without moving/dropping individual marks. Full substitute-font measurements can be supplied; fallback bounds are explicitly estimated. This is not yet final collision/typographic acceptance.

## Still pending before runtime acceptance

The dashboard does not call the generator yet. Both runtime reference gates remain false; existing projects, Simplified artwork, supplier records and GLBs are unchanged.

Next: connect persisted per-band state and shared artwork adapters, then add requested controls. Adapters must consume individual font sizes and unit-box backgrounds, reconstruct annular substrates/light strip/blue numeral row, and preserve square clearance strokes and hollow pointers. Current HD canvas and DXF consumers fill pointers unconditionally; merely passing `color: 'none'` is insufficient. Those consumers were **not** changed here.

Source row gaps, caption/pointer spacing, substitute typography and collisions need source comparison on actual physical targets. Explicit layout dimensions here are reconstruction inputs, not inferred supplier fit. No factory-font or ink claim is made.

Then verify Engineering, HD, SVG/PDF/DXF, rotation, reset, visibility, save/load, Undo and invalid-fit export refusal before enabling Citizen. Do not start Navitimer artwork or GLB regeneration as part of this initial stage.

## Checks and handoff

- 548 tests pass in74 files, including11 new generator tests.
- Typecheck, lint and production build pass. Existing Three.js deprecation, dependency annotation and large-bundle warnings remain non-failing.
- No browser visual acceptance: runtime/control code was not changed.
- Work remains uncommitted; no push performed. Final whitespace checks are recorded in the chat handoff.

Files: `src/domain/scales/citizenReferenceArtwork.ts`, `src/tests/citizenReferenceArtwork.test.ts`, this checkpoint and the overarching plan status link.

## Completed runtime follow-up

The user subsequently authorised finishing3A, committing/pushing its checkpoint and automatically continuing3B. The initial-stage pending list above is historical.

Citizen is now available as an explicitly disclosed photographic reconstruction. Advanced has the requested left checkbox choices and a contextual right inspector. Navitimer remains disabled until3B. Selection, unticking/re-enabling, Original/Custom Colours, independent role hex values, row/distance visibility, physical targets, four row radii, label size, tick length, line width, rotation and Reset to Original are connected to the authoritative saved assembly. Citizen/Simplified settings stay isolated; save/load, Undo/Redo, locks and archetype guards have regression coverage. Missing time features are not exposed.

The canonical engine now uses the450-position inventory in Engineering and HD, with shared SVG/PDF artwork and vector DXF substrates/unit boxes. Individual font sizes, hollow pointers, square clearance strokes and independent palettes survive export. Strict invalid-fit/overlap errors refuse manufacturing exports instead of omitting marks. Separate physical layers claiming the same fixed ring are rejected.

HD acceptance found and repaired two actual causes: the procedural chapter torus ignored its selected annulus and obscured the print plane; authored GLB canvas textures had the wrong vertical UV orientation. The procedural carrier now has the selected physical radii and a flat print face below the crystal. Authored textures use GLTF's proper V convention, verified against every vertex of the existing42mm chapter GLB. No GLB regeneration or supplier mutation was needed.

Computer-use checks in an isolated1440x1000 browser tab exercised selection, reopening Advanced, disabling/re-enabling, outer/distance visibility, custom hex changes against rendered SVG attributes, reset, outer rotation and an oversized4mm label refusal. Engineering and HD were inspected on40mm procedural and42mm authored fixtures. The recovered Citizen image was compared for row order, colours, tangent orientation, unit boxes and pointer directions; exhaustive identity/profile assertions cover all450 source records. Screenshots: [Engineering controls](research/slide-rules/acceptance/citizen-engineering-controls.jpg), [HD](research/slide-rules/acceptance/citizen-hd-controls.jpg).

**Limits:** this is not a factory-exact or supplier-fit certificate. Original fonts/ink/print radii remain unavailable. Default source-pixel scale is adapted to the selected printable annuli; small chapter rings produce small lettering and require a1:1 readability decision. Arial substitution, cap-height conversion and source-derived radial gaps are disclosed reconstruction choices. HD lighting/crystal changes apparent ink colour. PDF standard-font substitution and DXF viewer font differences remain; fonts are not outlined. Existing watch dial graphics are not Citizen branding. Full cross-archetype/manufacturing visual acceptance remains Milestone7, not a claim made here.

Runtime/state/export wiring is complete and ready for3B reuse. Full follow-up suite:568 tests in78 files; typecheck/lint/build and whitespace checks passed (existing dependency/bundle warnings only). Final publishing hash is reported in chat; this supersedes the initial-stage uncommitted/no-browser status above.
