201590022033/Dial-New-Design.01/engineering/LAYOUT_ENGINE.md

# Intelligent Layout Engine

## Overview

The Intelligent Layout Engine is a plugin-agnostic post-math pipeline used by scale plugins after tick/label generation and before final validation and export.

It never alters the mathematical mapping of values to angles.

## Architectural Position

The engine composes with the existing framework modules:

1. Tick engine (mathematical projection)
2. Label engine (placement)
3. Collision framework (diagnostics)
4. Layout optimizer (optional readability improvements)
5. Manufacturing diagnostics (process constraints)
6. Validation engine (health score synthesis)

This keeps the Geometry Engine, Renderer, Scale Engine, and Plugin Registry unchanged while allowing each plugin to inherit layout intelligence.

## Responsibilities

- Determine adaptive density profile from available arc length and radius
- Optionally optimize layout for readability using conservative, configurable transforms
- Provide manufacturing spacing diagnostics without mutating export geometry
- Enrich validation results with collision/manufacturing diagnostics
- Compute engineering health scoring inputs

## Adaptive Density Algorithm

Inputs:

- Angular span
- Reference radius
- Requested profile

Outputs:

- Effective profile: ultra-dense, dense, engineering, balanced, sparse
- Major tick budget
- Minor tick budget
- Micro tick budget
- Minimum label frequency

Selection strategy is circumference-aware to keep ring density proportional to available printable arc length.

## Collision Resolution Strategy

Optimization is configurable via plugin config and includes:

- Micro angular staggering
- Small radial label offsets
- Typography compaction for long labels
- Adaptive label omission with priority weighting
- Micro tick simplification in dense regions

Supported label priority modes:

- balanced
- major-critical
- uniform

All transforms are display/layout transforms only; scale values remain unchanged.

## Manufacturing Optimization Diagnostics

The engine computes per-scale minimum spacing estimates:

- Printable spacing
- Engraving spacing
- Laser spacing
- CNC spacing
- UV spacing
- Pad-print spacing

Warnings are emitted into validation diagnostics, but exported geometry is not silently altered.

## Engineering Health Report

Each validation result includes:

- Mathematical Health
- Readability Score
- Collision Score
- Manufacturing Score
- Validation Score
- Overall Engineering Score

Scoring weights currently prioritize mathematical correctness and manufacturability while still accounting for readability/collision quality.

## Engineering Assumptions

- Circular arc projections are wrap-safe in angular comparisons
- Small visual offsets are acceptable for readability when value-angle mapping is preserved
- Label text length can approximate arc occupancy for first-pass collision risk
- Manufacturing process thresholds are conservative generic defaults, not machine-specific calibration data

## Numerical Precision Notes

- Angular deltas use circular normalization with 360-degree wrap handling
- Threshold comparisons use bounded floating-point tolerances to avoid flicker diagnostics
- Spacing diagnostics are rounded for deterministic reporting

## Performance Considerations

- Collision checks are intentionally bounded and lightweight for interactive inspector updates
- Near-miss detection avoids full geometric intersection solving for real-time UX
- Optimization passes are linear over ticks/labels with minimal allocations

## Future Extensions

- Font-metric-aware arc occupancy estimation
- Ring-segment-specific density profiles
- Manufacturing profile packs for process-specific calibration
- Deterministic legal/compliance label retention policies
