201590022033/Dial-New-Design.01/docs/research/crown-c0-2026-10-10/ladies34-hd-front.jpg

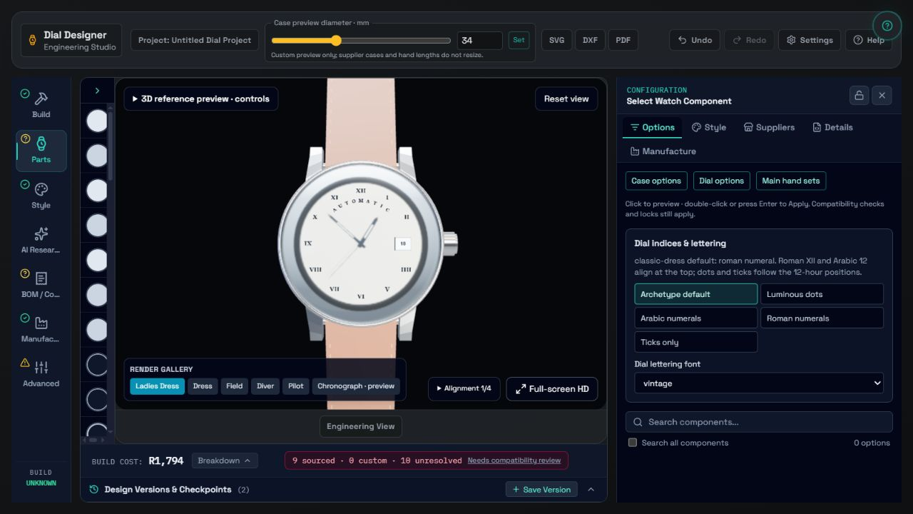
docs/research/crown-c0-2026-10-10/ladies34-hd-front.jpg
