201590022033/Dial-New-Design.01/docs/research/crown-c3-2026-10-10/coarse-fluted-hd-front.jpg

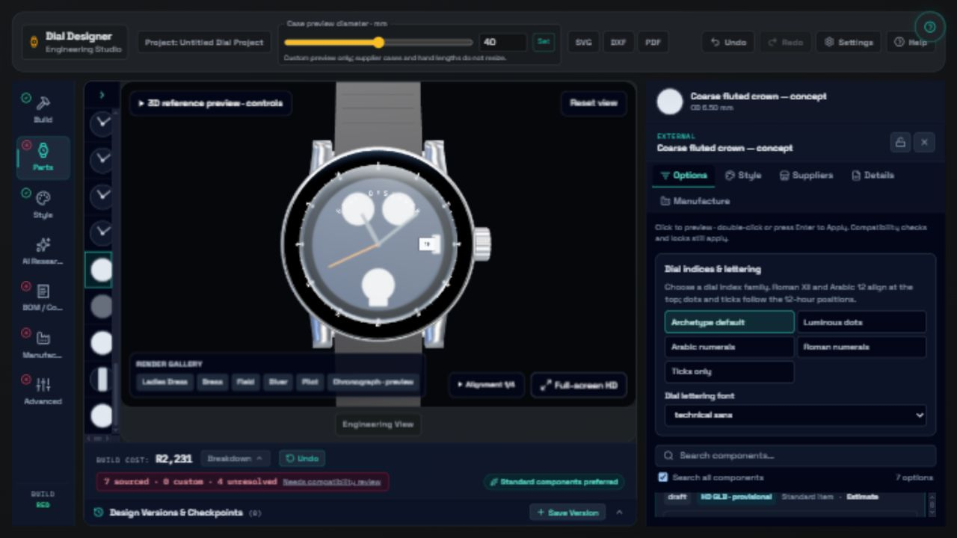
docs/research/crown-c3-2026-10-10/coarse-fluted-hd-front.jpg
