201590022033/Dial-New-Design.01/docs/research/crown-c3-2026-10-10/fine-fluted-hd-side.jpg

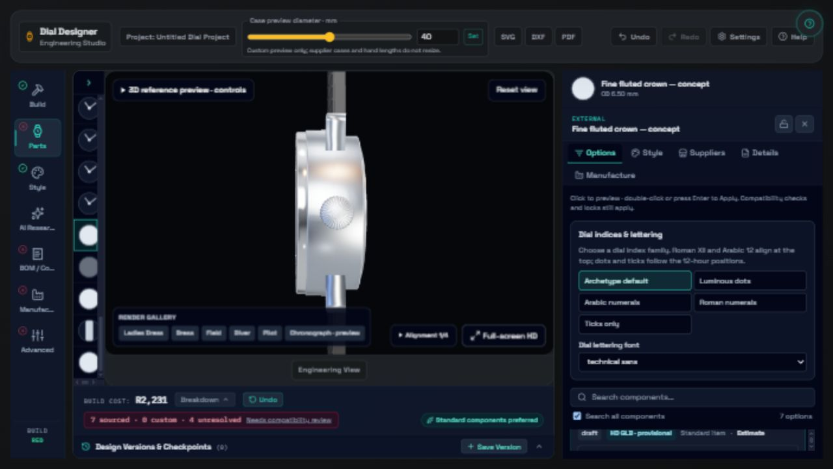
docs/research/crown-c3-2026-10-10/fine-fluted-hd-side.jpg
