201590022033/Dial-New-Design.01/docs/research/slide-rules/acceptance/citizen-hd-controls.jpg

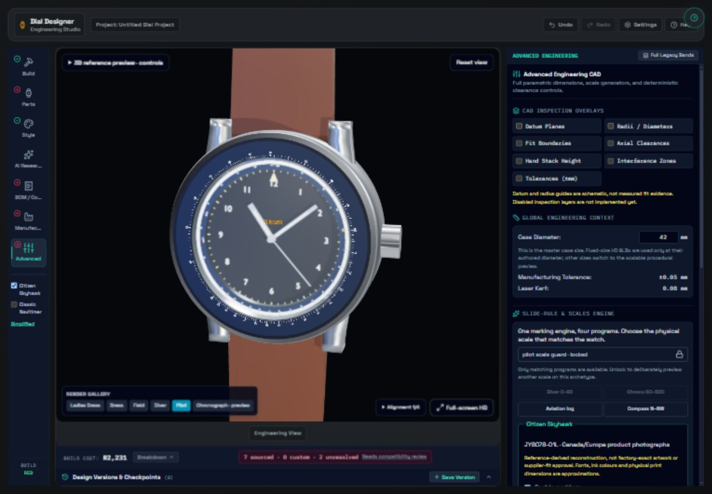
docs/research/slide-rules/acceptance/citizen-hd-controls.jpg
