201590022033/Dial-New-Design.01/docs/research/slide-rules/acceptance/diver-single-bezel-scale-2026-10-09.png

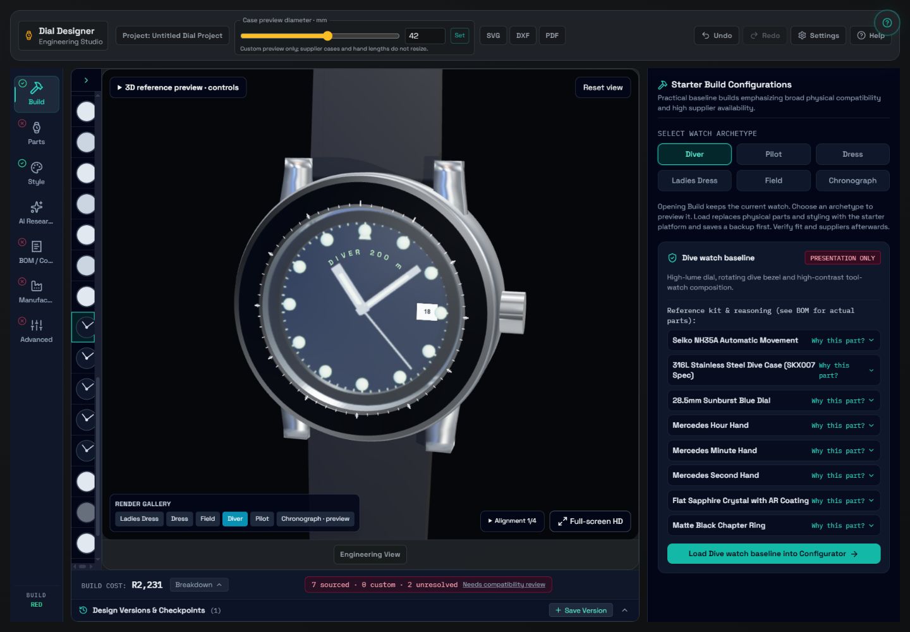
docs/research/slide-rules/acceptance/diver-single-bezel-scale-2026-10-09.png
