201590022033/Dial-New-Design.01/docs/research/slide-rules/acceptance/m4-hybrid-desktop-2026-10-08.jpg

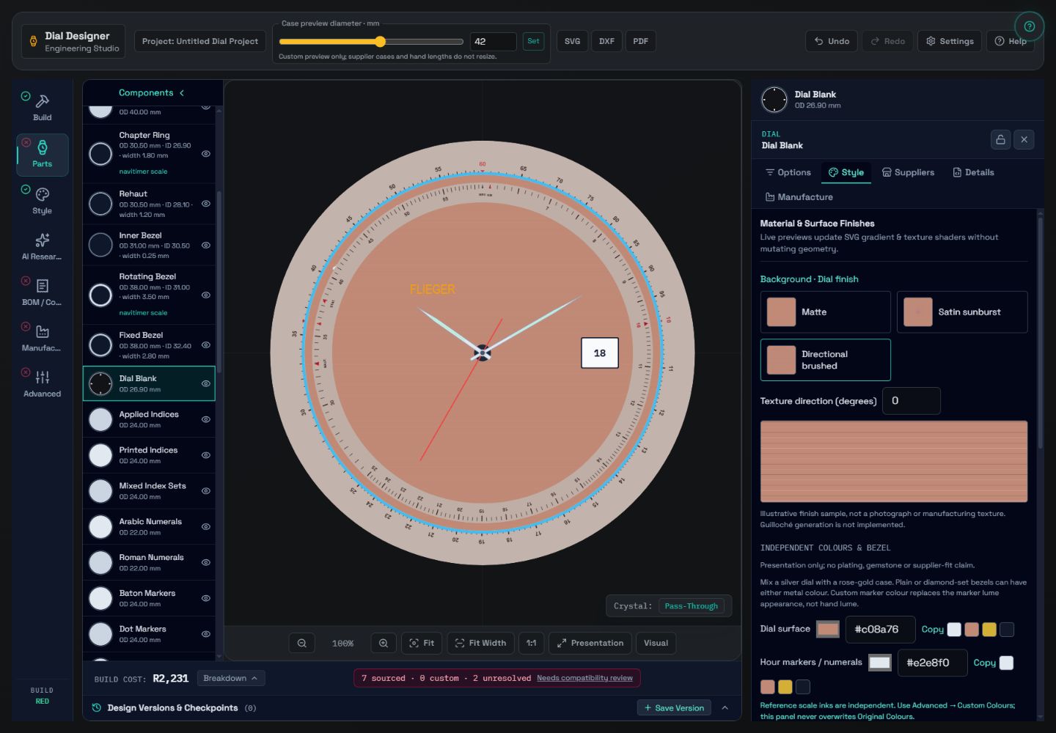
docs/research/slide-rules/acceptance/m4-hybrid-desktop-2026-10-08.jpg
