201590022033/Dial-New-Design.01/docs/research/slide-rules/acceptance/m5-decimal-engineering.png

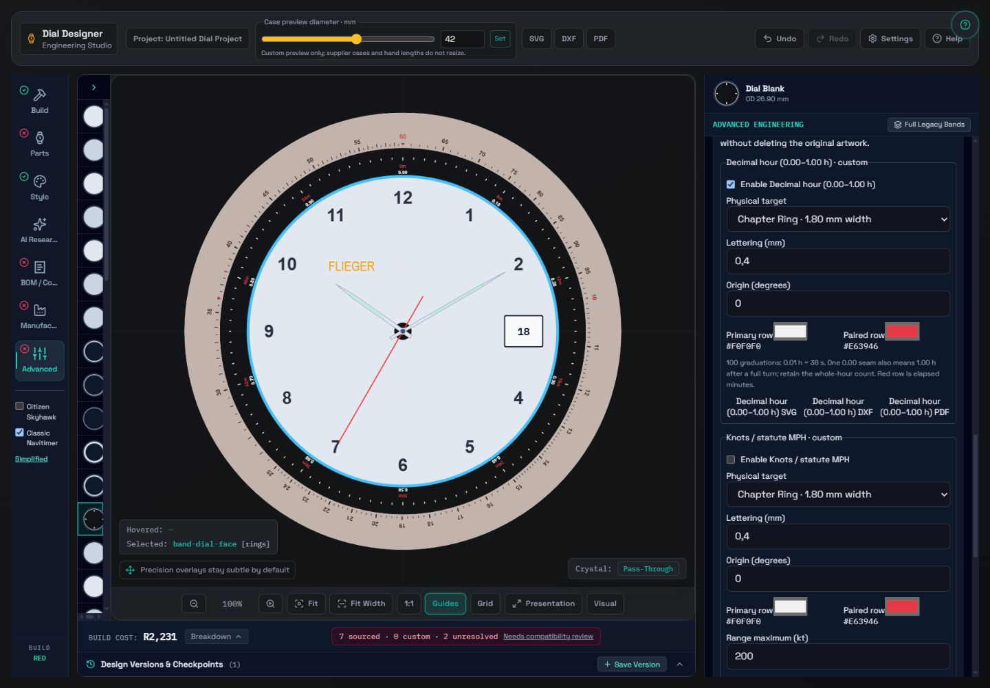
docs/research/slide-rules/acceptance/m5-decimal-engineering.png
