201590022033/Dial-New-Design.01/docs/research/slide-rules/acceptance/m6-engineering-outline-tips-2026-10-09.jpg

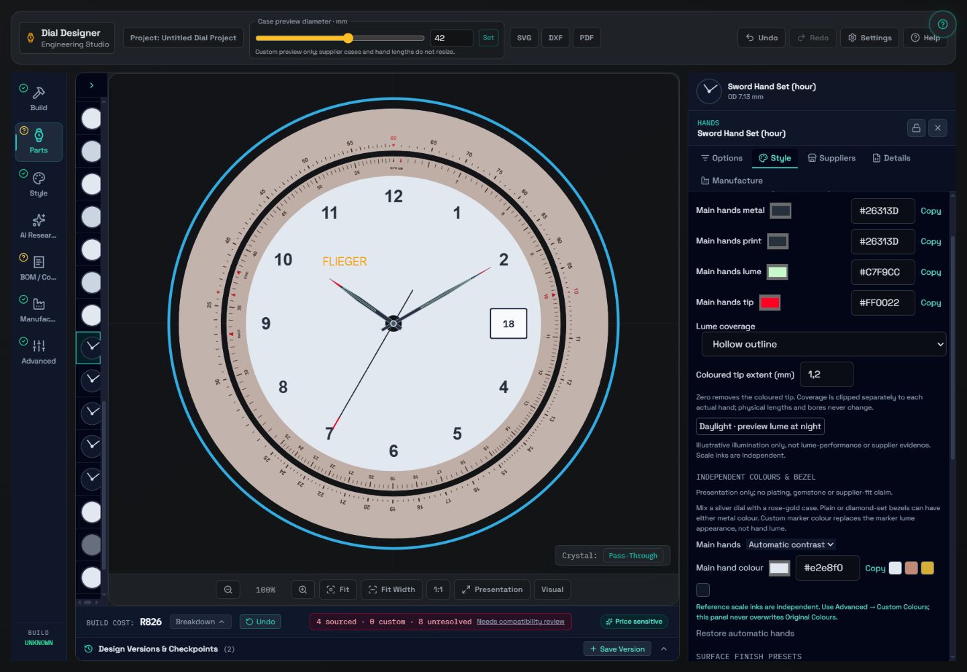
docs/research/slide-rules/acceptance/m6-engineering-outline-tips-2026-10-09.jpg
