201590022033/Dial-New-Design.01/docs/research/slide-rules/acceptance/m6-hand-controls-baseline.png

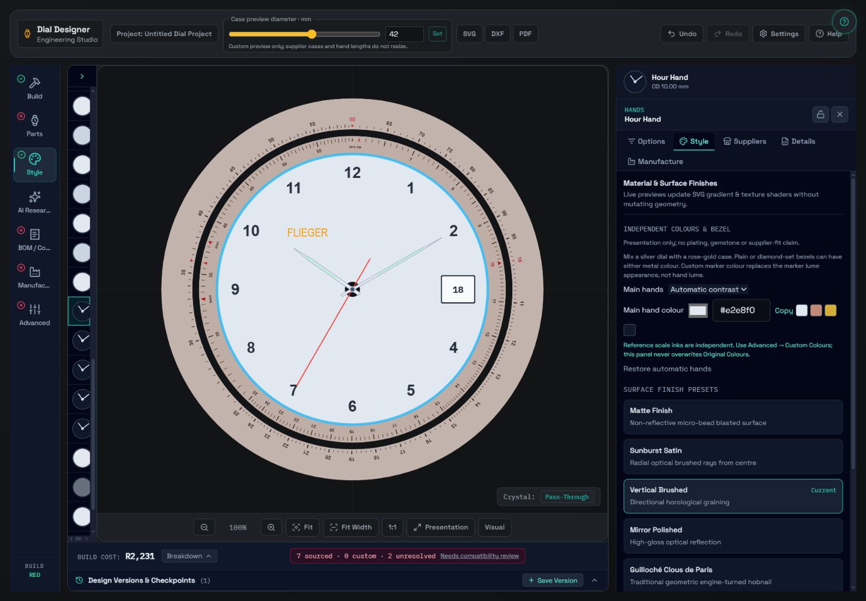
docs/research/slide-rules/acceptance/m6-hand-controls-baseline.png
