201590022033/Dial-New-Design.01/docs/research/slide-rules/acceptance/m6-ladies34-hd-2026-10-09.jpg

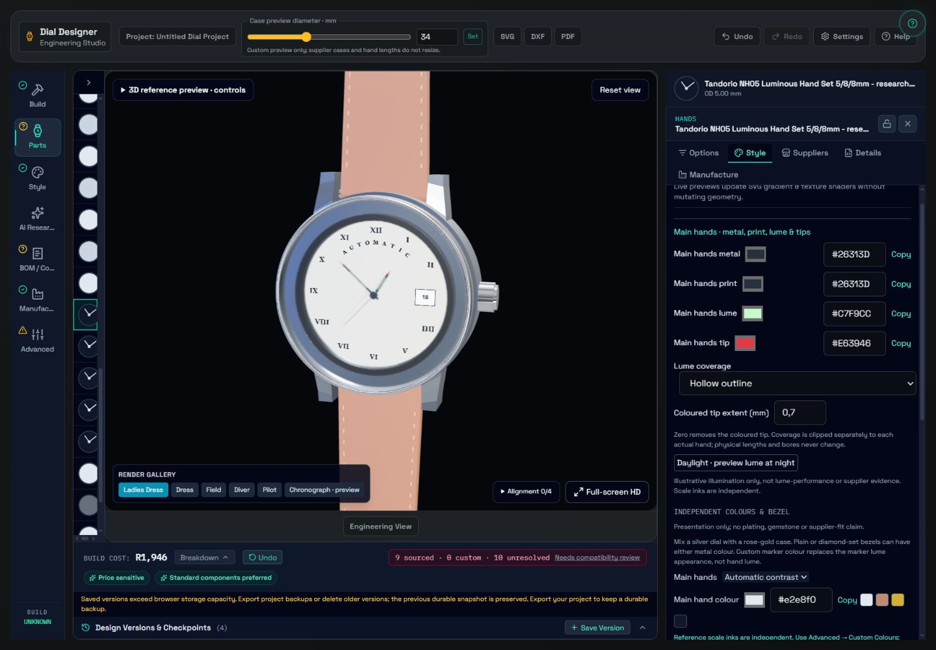
docs/research/slide-rules/acceptance/m6-ladies34-hd-2026-10-09.jpg
