201590022033/Dial-New-Design.01/docs/research/slide-rules/acceptance/navitimer-hd-controls.jpg

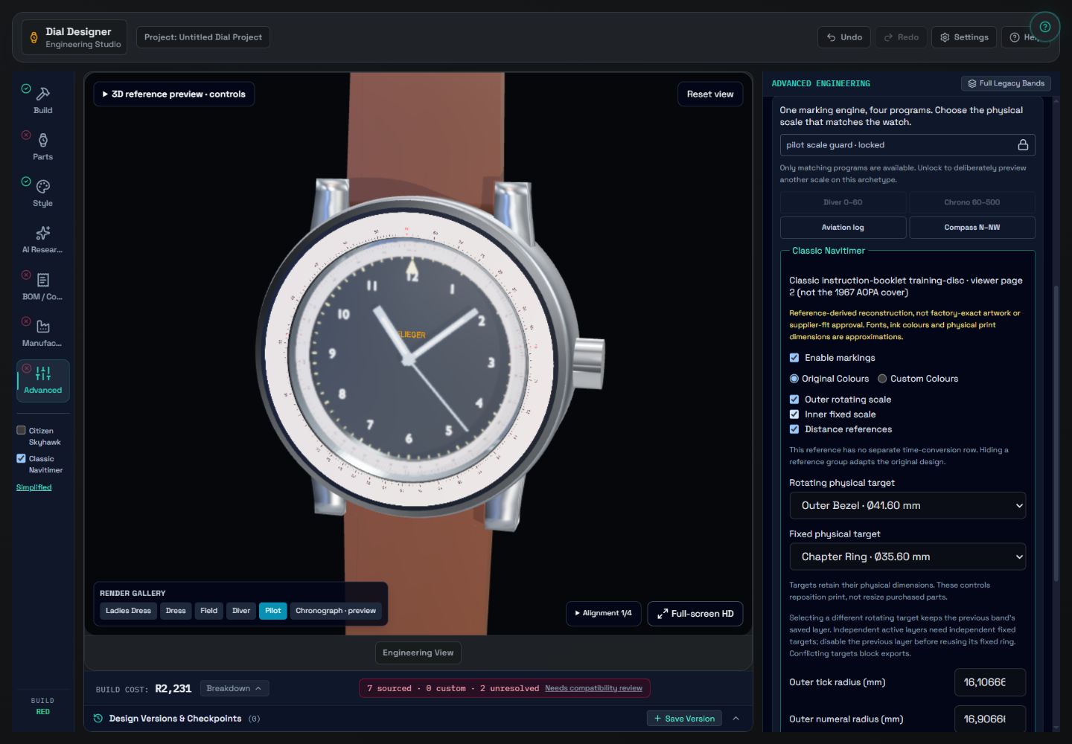
docs/research/slide-rules/acceptance/navitimer-hd-controls.jpg
