201590022033/Dial-New-Design.01/docs/research/slide-rules/evidence/citizen-ca-1600.webp

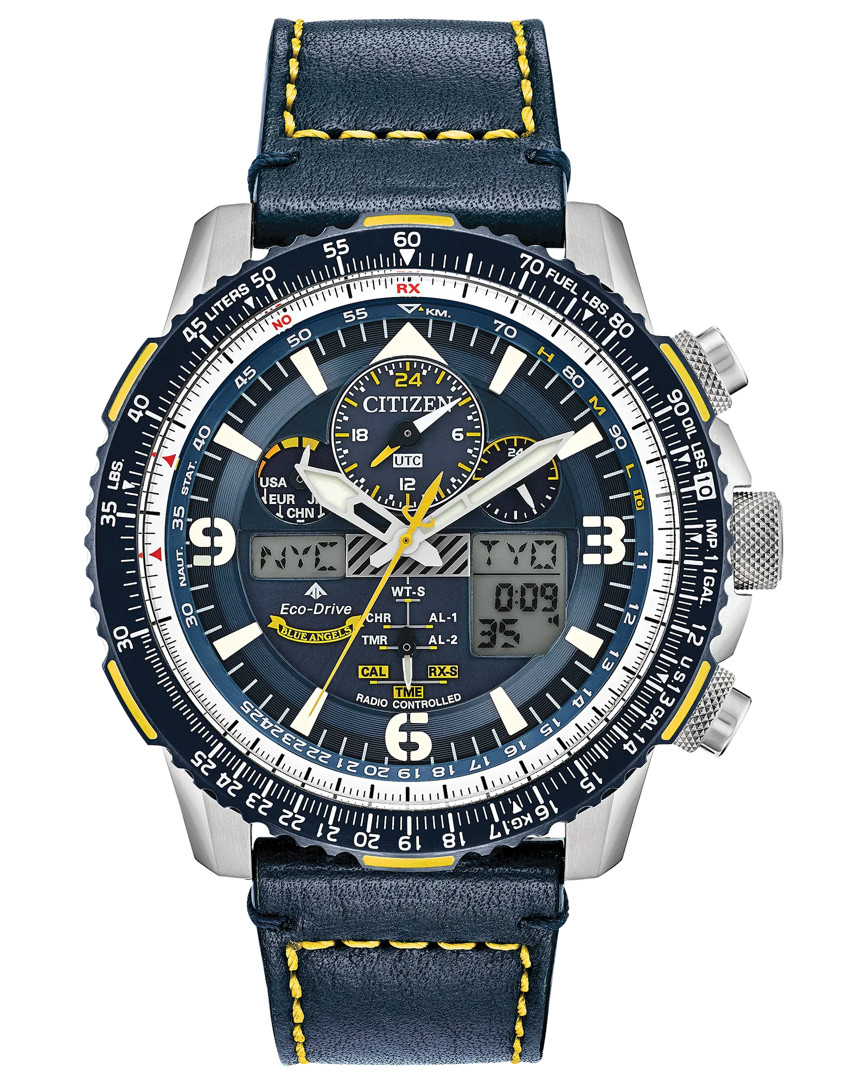
docs/research/slide-rules/evidence/citizen-ca-1600.webp
