201590022033/Dial-New-Design.01/docs/research/slide-rules/evidence/citizen-de-2000.webp

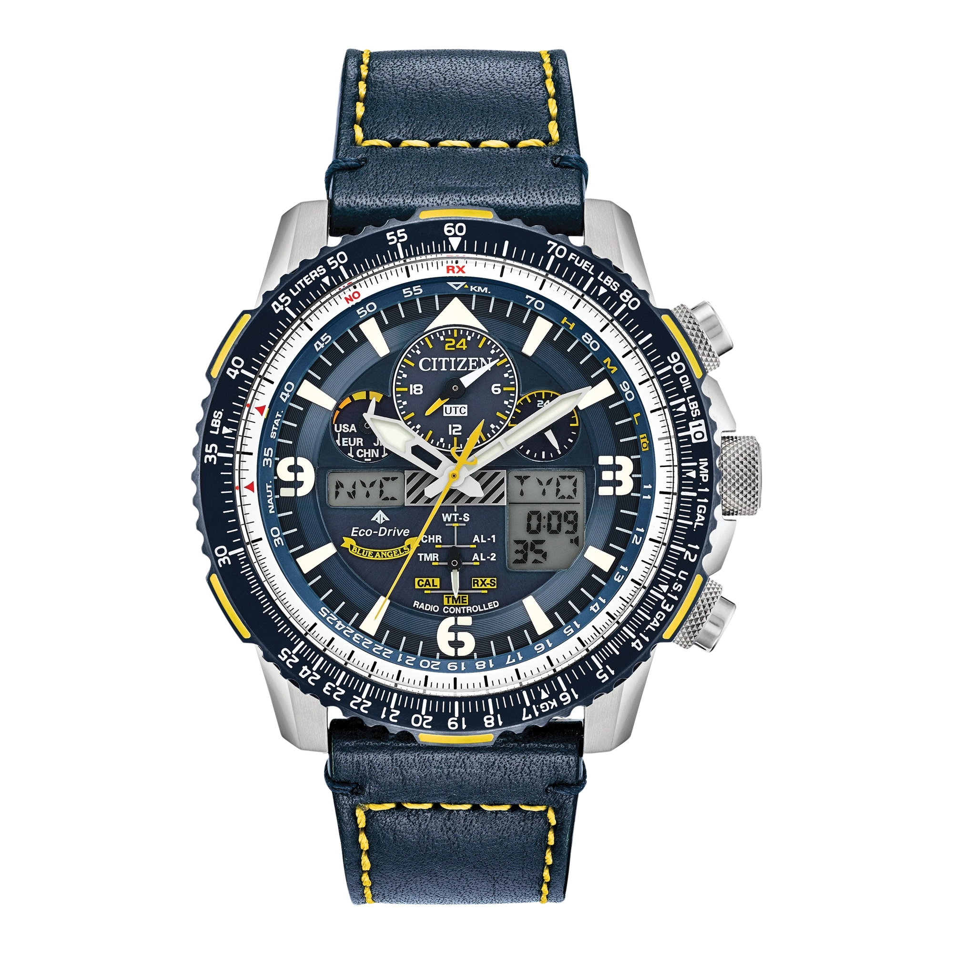
docs/research/slide-rules/evidence/citizen-de-2000.webp
