201590022033/Dial-New-Design.01/docs/research/slide-rules/evidence/navitimer-training-disc-native.jpg

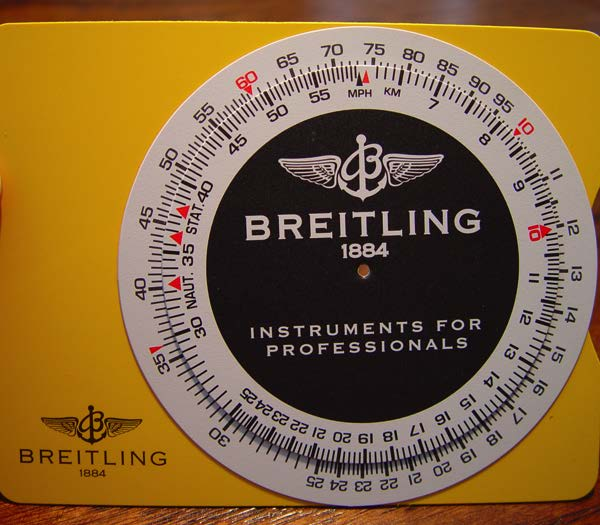
docs/research/slide-rules/evidence/navitimer-training-disc-native.jpg
