201590022033/Dial-New-Design.01/output/pdf/m7-42-citizen-review.png

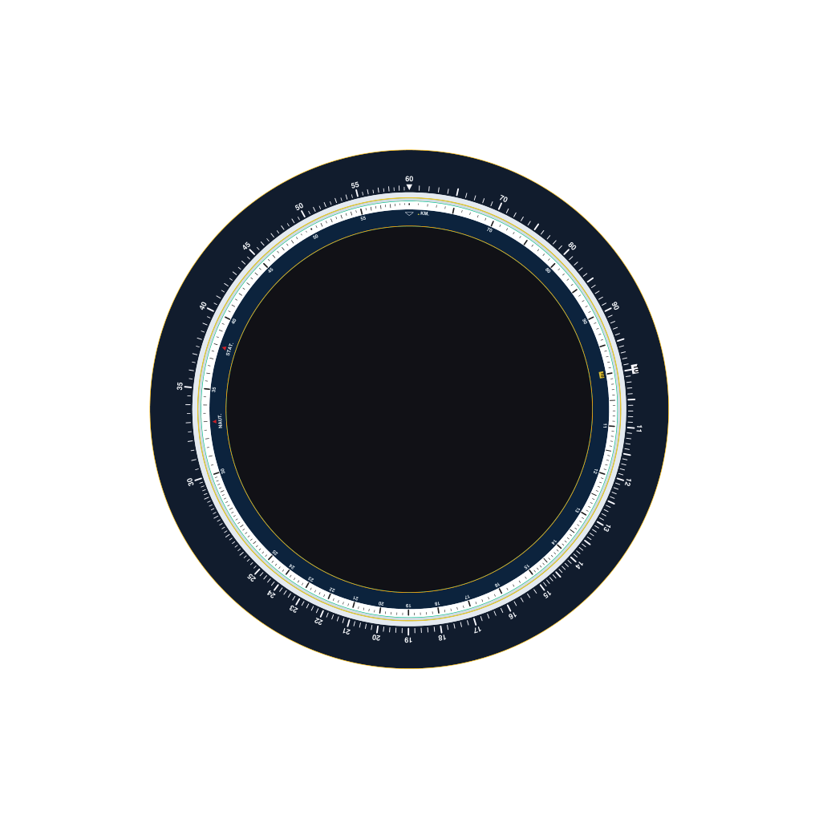
output/pdf/m7-42-citizen-review.png
