201590022033/Dial-New-Design.01/public/assets/3d/face-review/review-001.png

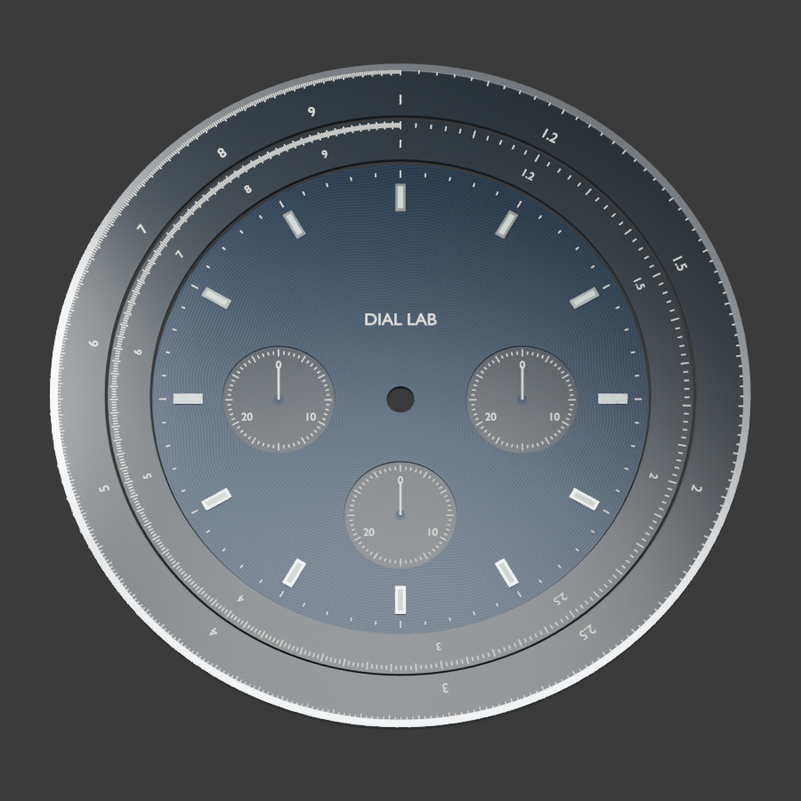
public/assets/3d/face-review/review-001.png
