201590022033/Dial-New-Design.01/docs/research/aliexpress-watch-parts-2026-09-26.md

# AliExpress watch-parts price snapshot — South Africa

Research captured: **2026-09-26 (Africa/Johannesburg)**
FX snapshot: **USD 1 = ZAR 16.348**, close on 2026-09-25.
Destination assumption: **South Africa**.

## Important costing rule

AliExpress item prices are not landed prices. Shipping is seller-, option-, and destination-specific and was not exposed by the independently indexed product pages used for this snapshot. A listing with unknown shipping must therefore remain **shipping pending**, never R0 shipping. Before purchase, capture the South-Africa checkout shipping charge and timestamp it separately.

SARS states that import VAT is 15% of the added-tax value, with a 10% customs-value uplift for goods imported from outside the customs union, plus any applicable duty. The indicative Rand figures below exclude shipping, customs duty, courier clearance fees, and VAT.

## Initial NH35 / SKX-style component snapshot

| Component | AliExpress item | Item price | Approx. Rand | Price timestamp | Shipping to SA |
|---|---|---:|---:|---|---|
| NH35A movement, 3 o'clock date | Item `1005011764720690` | US$41.08 | R672 | 2026-07-07 | Pending checkout |
| 42 mm SKX007 case with sapphire | Item `1005005676160080` | US$27.03 | R442 | 2026-09-21 | Pending checkout |
| 28.5 mm NH35 luminous dial | Item `1005010777833304` | US$10.42 | R170 | 2026-09-11 | Pending checkout |
| Mercedes hand set, NH35 compatible | Search result listing | US$8.13 | R133 | 2026-09-26 search | Pending checkout |
| 38 × 31.5 mm ceramic bezel insert | Item `1005007316663590` | US$8.13 | R133 | 2026-09-01 history | Pending checkout |
| 31.3 mm SKX chapter ring | Item `1005007486441308` | US$6.89 | R113 | 2026-09-13 | Pending checkout |
| 31.5 mm flat sapphire crystal | Item `1005013221603872` | US$7.99 | R131 | 2026-09-22 | Pending checkout |

The raw item-price subtotal is approximately **R1,794**. This is **not a purchase total**: it deliberately excludes shipping, possible bundle duplication (for example, a case may already include a crystal), customs duty, import VAT, courier/SAPO handling, and watchmaker labour.

## Purchase-validation checklist

1. Select the exact variant, not the lowest teaser variant.
2. Set delivery country and postal code to South Africa.
3. Record item price, shipping, tax shown at checkout, seller, variant, and timestamp.
4. Confirm dimensions and interfaces: movement, stem position, dial diameter/feet, hand-hole sizes, crystal diameter/thickness, bezel insert OD/ID/profile, and chapter-ring OD/ID.
5. Prefer consolidated shipping only after comparing the combined checkout total; separate sellers can erase an apparent item-price saving.
6. Treat price snapshots older than 14 days as stale and re-check before ordering.

## Sources

- FX history: https://in.investing.com/currencies/usd-zar-historical-data
- NH35 movement price history: https://www.pricearchive.org/aliexpress.com/item/1005011764720690
- SKX007 case price history: https://es.pricearchive.org/aliexpress.com/item/1005005676160080
- 28.5 mm dial price history: https://www.pricearchive.org/aliexpress.com/item/1005010777833304
- Mercedes hands search snapshot: https://www.pricearchive.org/search/aliexpress.com/case-for-analog/16
- Ceramic bezel insert price history: https://www.pricearchive.org/aliexpress.com/item/1005007316663590
- Chapter ring price history: https://www.pricearchive.org/aliexpress.com/item/1005007486441308
- Sapphire crystal price history: https://ru.pricearchive.org/aliexpress.com/item/1005013221603872
- SARS import VAT method: https://www.sars.gov.za/customs-and-excise/duties-and-taxes/duties-and-taxes-for-importers/
- South-Africa shipping variability: https://scottshipping.co.za/aliexpress-south-africa/
