201590022033/Dial-New-Design.01/docs/research/crown-c0-2026-10-10/supplier-sources/VK63_PL.pdf

29072022

※Please contact us when you order these parts.　　※订购零件时请与我们联系
PARTS NAME　　零件名称 | Type - L | Type - LL
Train wheel bridge 轮列夹板 | 0125 318
Center wheel and pinion bridge 中心轮夹板 | 4283 042
Center wheel and pinion 中心轮 | 0221 091 | ※
Third wheel and pinion 3# 轮 | 0231 059
Fourth wheel and pinion 4# 轮 | 0144 002
Fifth wheel and pinion 5# 轮 | 0701 015
Step rotor 磁石轮 | 4146 063
Hour wheel 时轮 | 0273 041 | ※
Minute wheel and pinion 度数轮 | 0261 126
Setting wheel 小铁车 | 0281 452
Clutch wheel 离合轮 | 0282 452
Setting lever 设置杆 (押制) | 0383 891
Yoke 离合杆 (横担) | 0384 024
Reset lever 止秒弹弓 | 4455 006
Train wheel setting lever 规正弹弓 | 0391 028
Stator (A) 定子板(A) | 4239 063
Stator (B) 定子板(B) | 4239 064
Circuit block 回路板 | 4004 353
Circuit block spacer 回路板墊片 | 4408 149
Coil block (A) 线圈(A) | 4002 054
Coil block (B) 线圈(B) | 4002 055
Battery connection (-) 负极片(-) | 4270 336
Seconds wheel 秒轮 | 0240 018 | ※
Seconds counter intermediate wheel and pinion 计秒中间轮 | 0885 003
Seconds counting wheel 计秒轮 | 0888 027 | ※
Counter intermediate wheel and pinion 计时中间轮 | 0886 004
Minute counter intermediate wheel and pinion (A) 计分中间轮和轴(A) | 0886 005
Minute counter intermediate wheel (B) 计分中间轮和轴(B) | 0886 006
Minute counter intermediate wheel (C) 计分中间轮和轴(C) | 0886 007
Minute counting wheel 计分轮 | 0902 017 | ※
Positioning arbor 定位柱 | 0685 003
Lower plate for chronograph bridge 计时轮列夹板 | 0186 002
Chronograph bridge 计时码表夹板 | 0190 007
Seconds counting wheel friction spring 秒计压片 | 0353 018
Hammer 三叉锤 | 0585 013
Chronograph coupling lever 计时码表连接杆 | 0581 007
Hammer operating lever (A) 三叉锤操作杆(A) | 0587 004
Hammer operating lever (B) 三叉锤操作杆(B) | 0587 006
Switch lever (A) 按制杆(A) | 4450 017
Switch lever (B) 按制杆(B) | 4450 018
Train wheel stop lever 规正弹弓 | 0894 002
Date indicator maintaining plate 日暦定位片(日历盘压片) | 0808 052
Date jumper 日历定位弹弓 | 0810 019
Date corrector setting transmission wheel (A) 企轮(A) | 0962 032
Date corrector setting transmission wheel (B) 企轮(B) | 0962 013
Date corrector setting transmission wheel (C) 企轮(C) | 0962 891
Date corrector wheel 日历修正轮 | 0806 002
Small hour hand wheel 小时针轮 | 0157 012 | ※

## Cal.VK63A Parts List

PARTS CODE　零件编号

## 维修零件清单

29072022

※Please contact us when you order these parts.　　※订购零件时请与我们联系
PARTS NAME　　零件名称 | Type - L | Type - LL
Intermediate small hour hand wheel and pinion 小时针中间轮 | 0817 048
Switch lever holder 按制杆压片 | 0837 005
Switch spring 按制弹弓 | 4250 076 | ※
Switch spring screw 按制弹弓螺丝 | 0016 121
Lower plate for chronograph bridge screw 计时轮列夹板螺丝 | 0016 121
Date indicator maintaining plate screw 日暦定位片螺丝 | 0012 354
Coil block screw 线圈组螺丝 | 0012 354
Switch lever holder screw 按制杆压片螺丝 | 0012 354
Winding Stem 巴芯 | 0351 177

## Cal.VK63A Parts List

PARTS CODE　零件编号

## 维修零件清单
