201590022033/Dial-New-Design.01/docs/reference-components/2026-09-20-social-reference/WhatsApp Image 2026-09-20 at 14.32.29 (1).jpeg

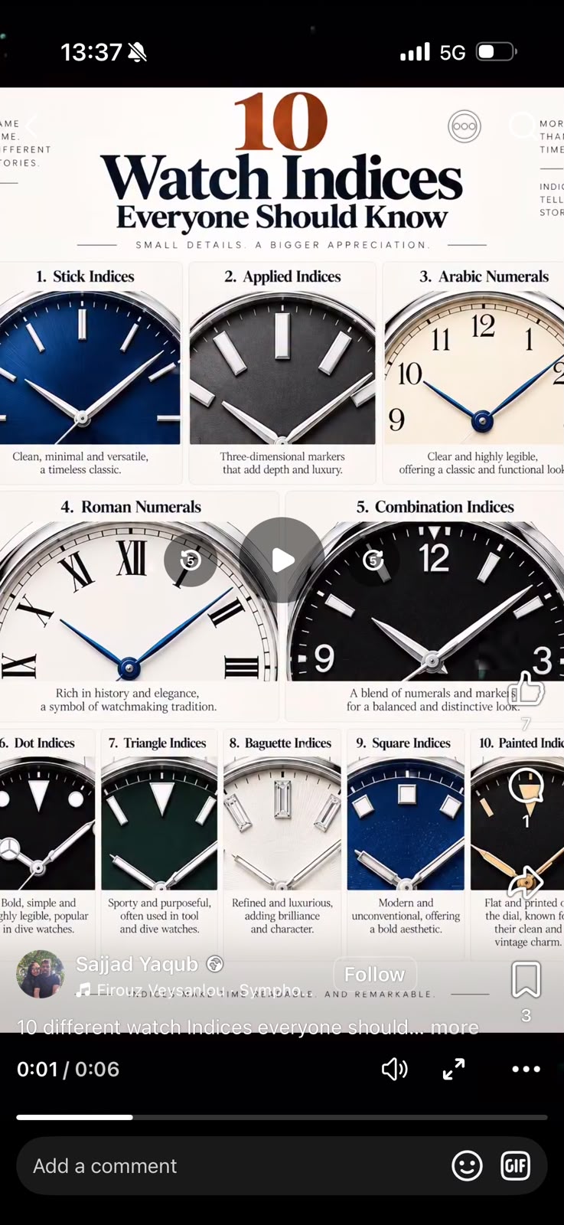
docs/reference-components/2026-09-20-social-reference/WhatsApp Image 2026-09-20 at 14.32.29 (1).jpeg
