201590022033/Dial-New-Design.01/docs/reference-components/2026-09-22-subdials-movements-lugs/watch-subdials.jpeg

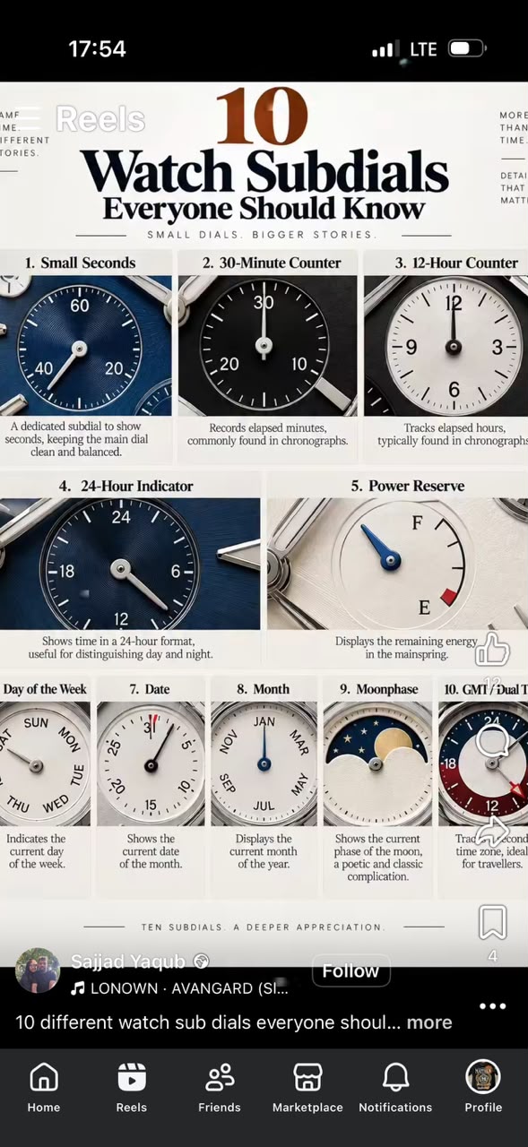
docs/reference-components/2026-09-22-subdials-movements-lugs/watch-subdials.jpeg
