201590022033/Dial-New-Design.01/docs/research/crown-c0-2026-10-10/NH05B-parts-page7.png

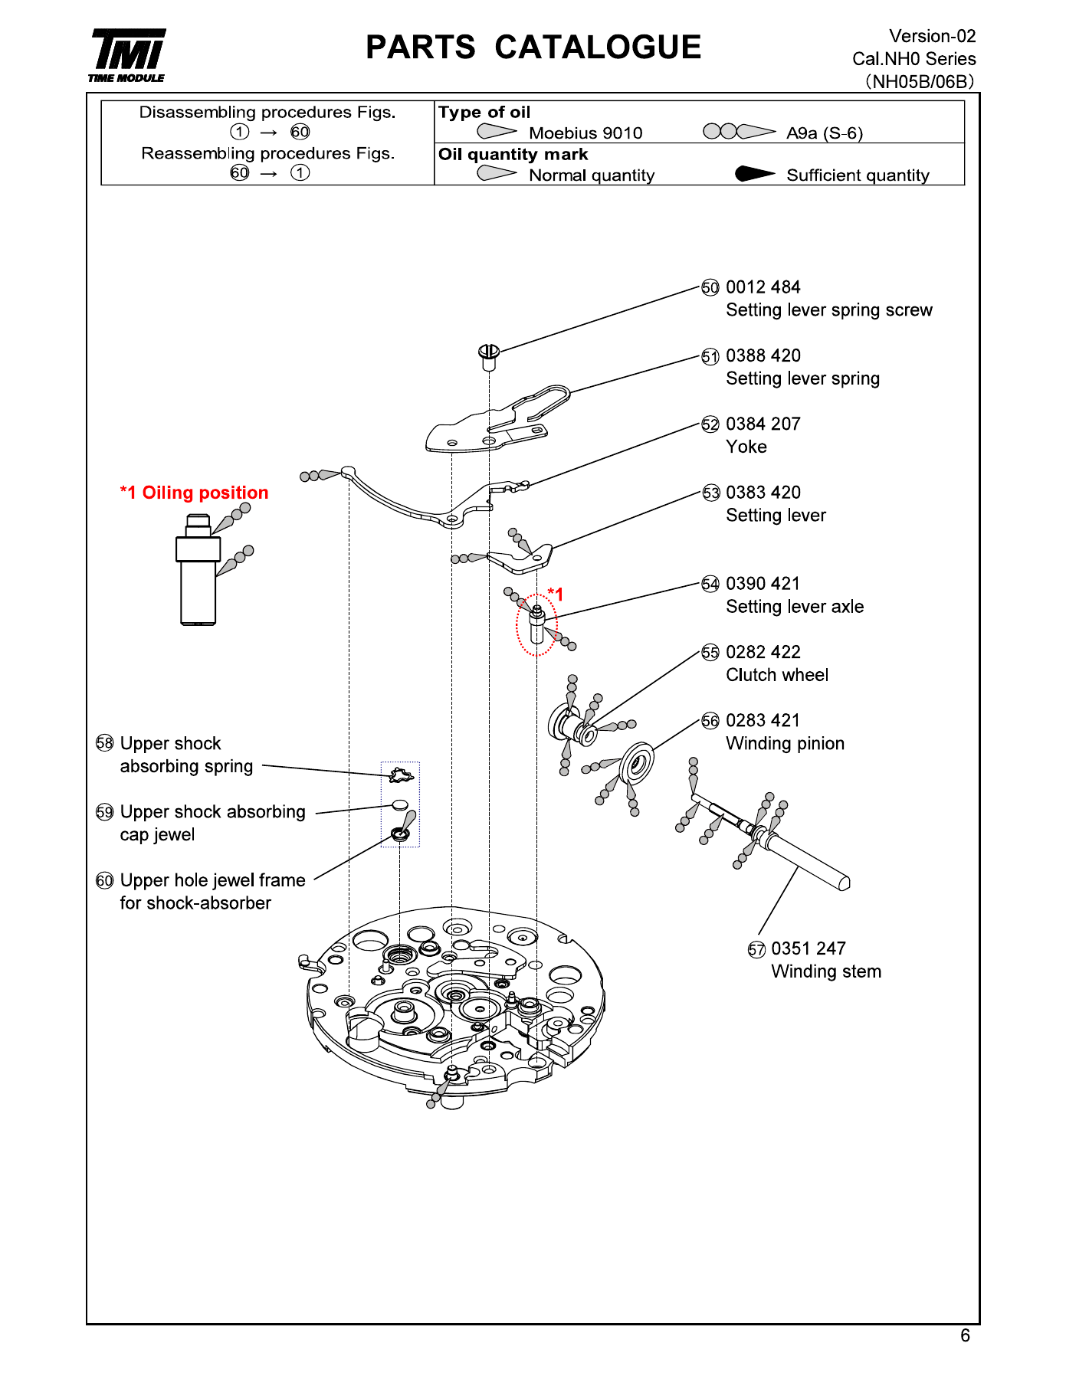
docs/research/crown-c0-2026-10-10/NH05B-parts-page7.png
