201590022033/Dial-New-Design.01/docs/research/crown-c0-2026-10-10/supplier-sources/NH34-stem7.png

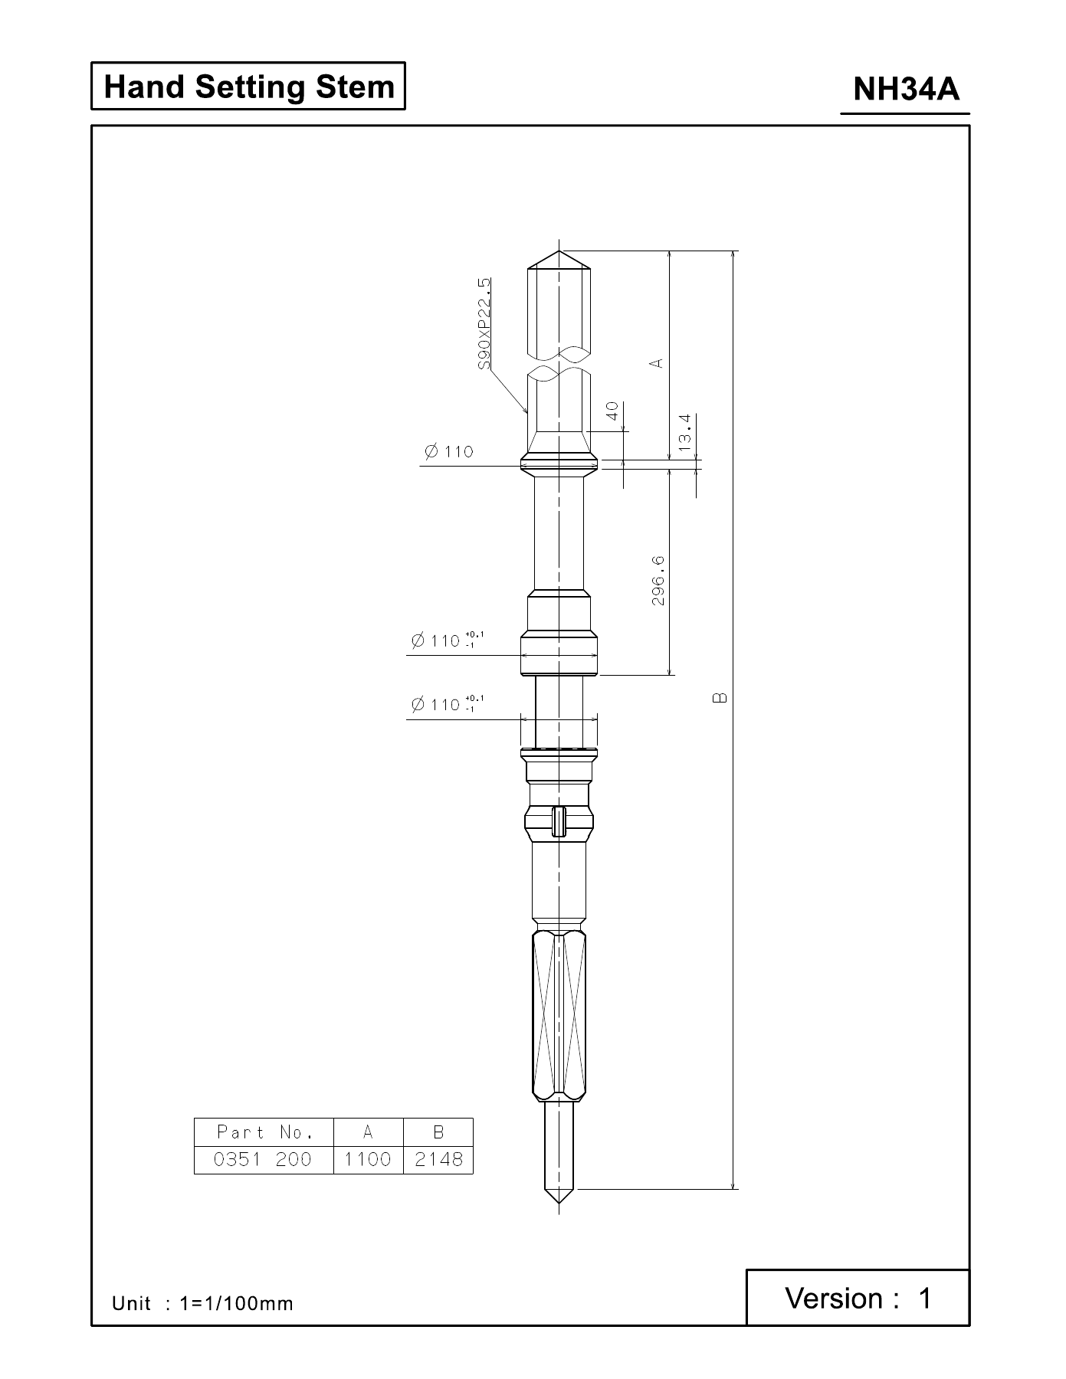
docs/research/crown-c0-2026-10-10/supplier-sources/NH34-stem7.png
