201590022033/Dial-New-Design.01/docs/research/crown-c0-2026-10-10/supplier-sources/VK63_SS.pdf

## Watch Movement Specification and Drawing

# VK63A

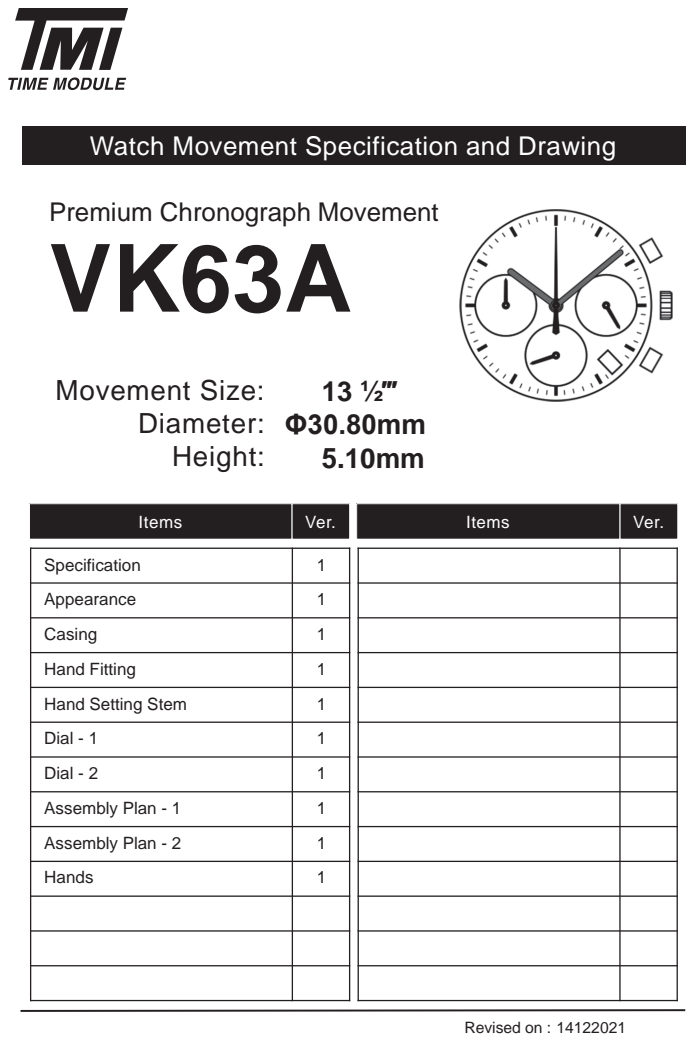
[picture p87: page 1]
Movement Size: Diameter: Height:; Items; Ver.; Revised on :

Premium Chronograph Movement

Specification | 1
Appearance | 1
Casing | 1
Hand Fitting | 1
Hand Setting Stem | 1
Dial - 1 | 1
Dial - 2 | 1
Assembly Plan - 1 | 1
Assembly Plan - 2 | 1
Hands | 1

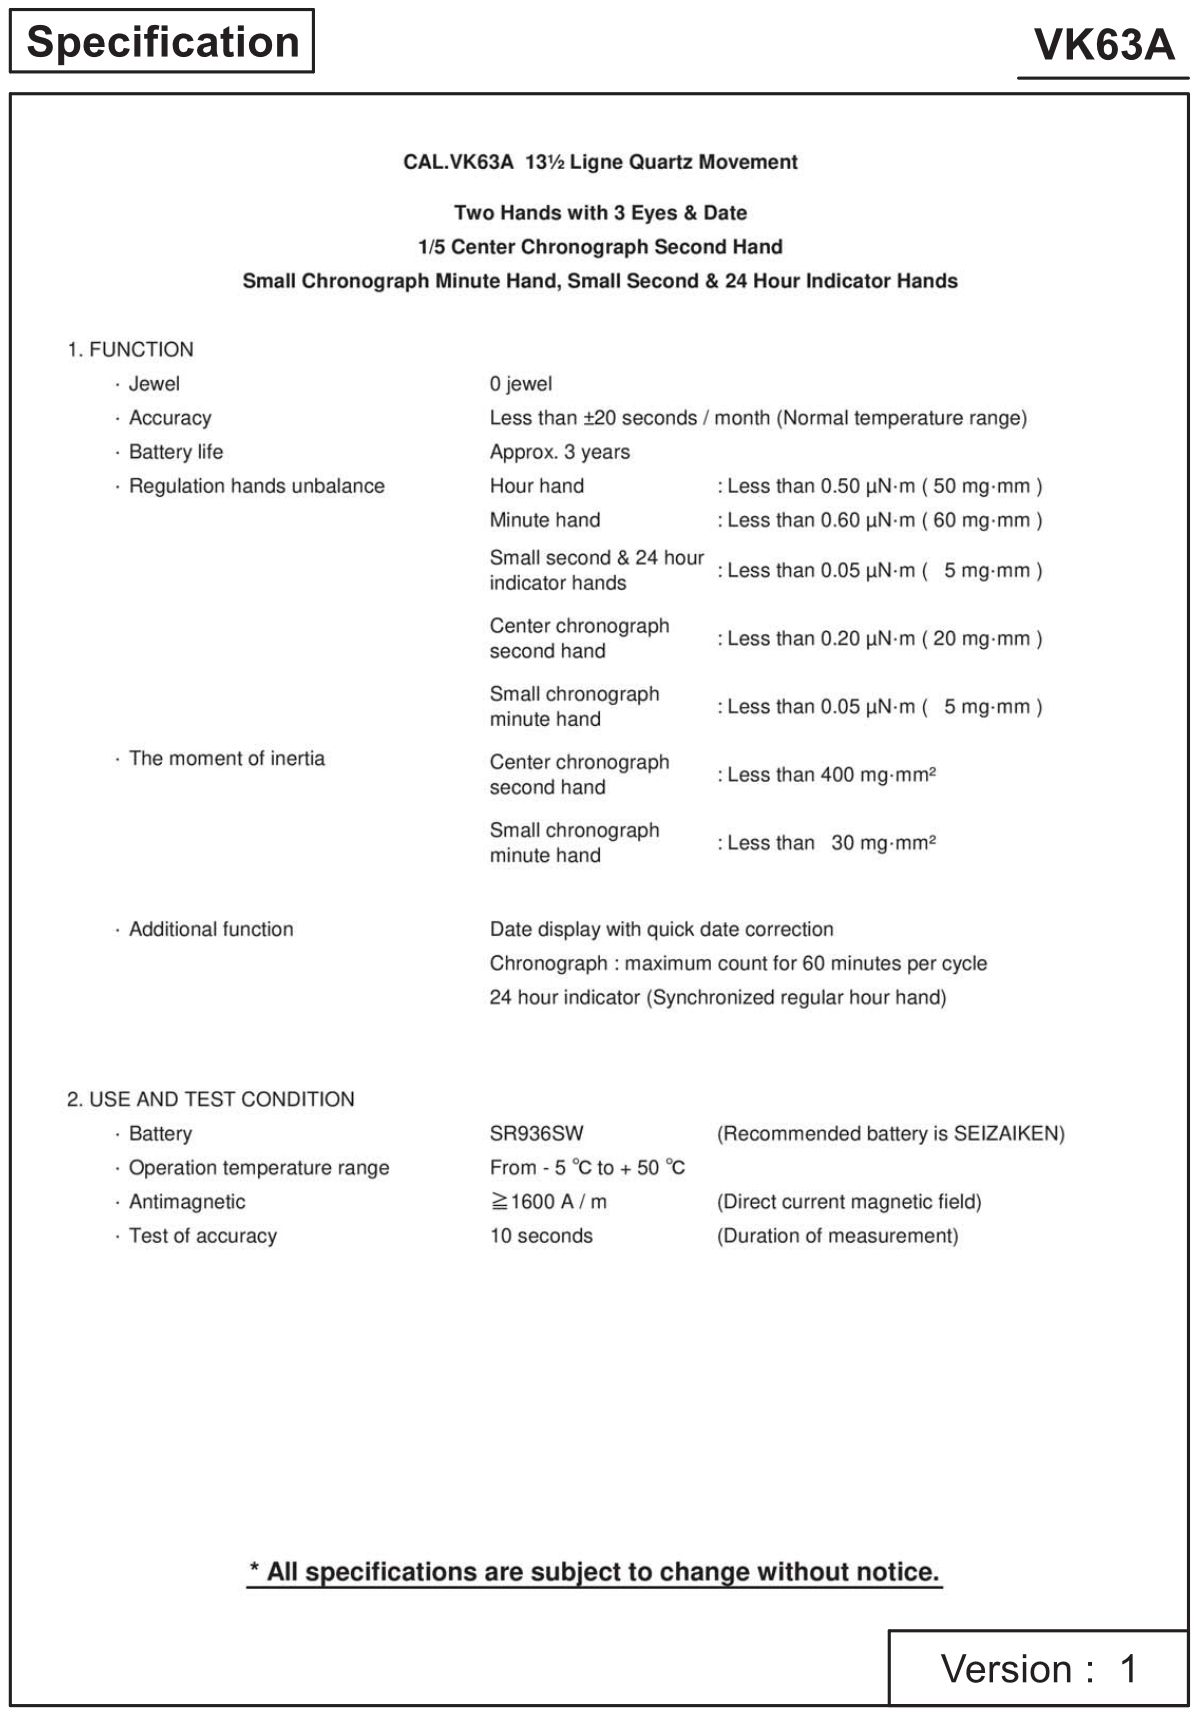
[picture p88: page 2]

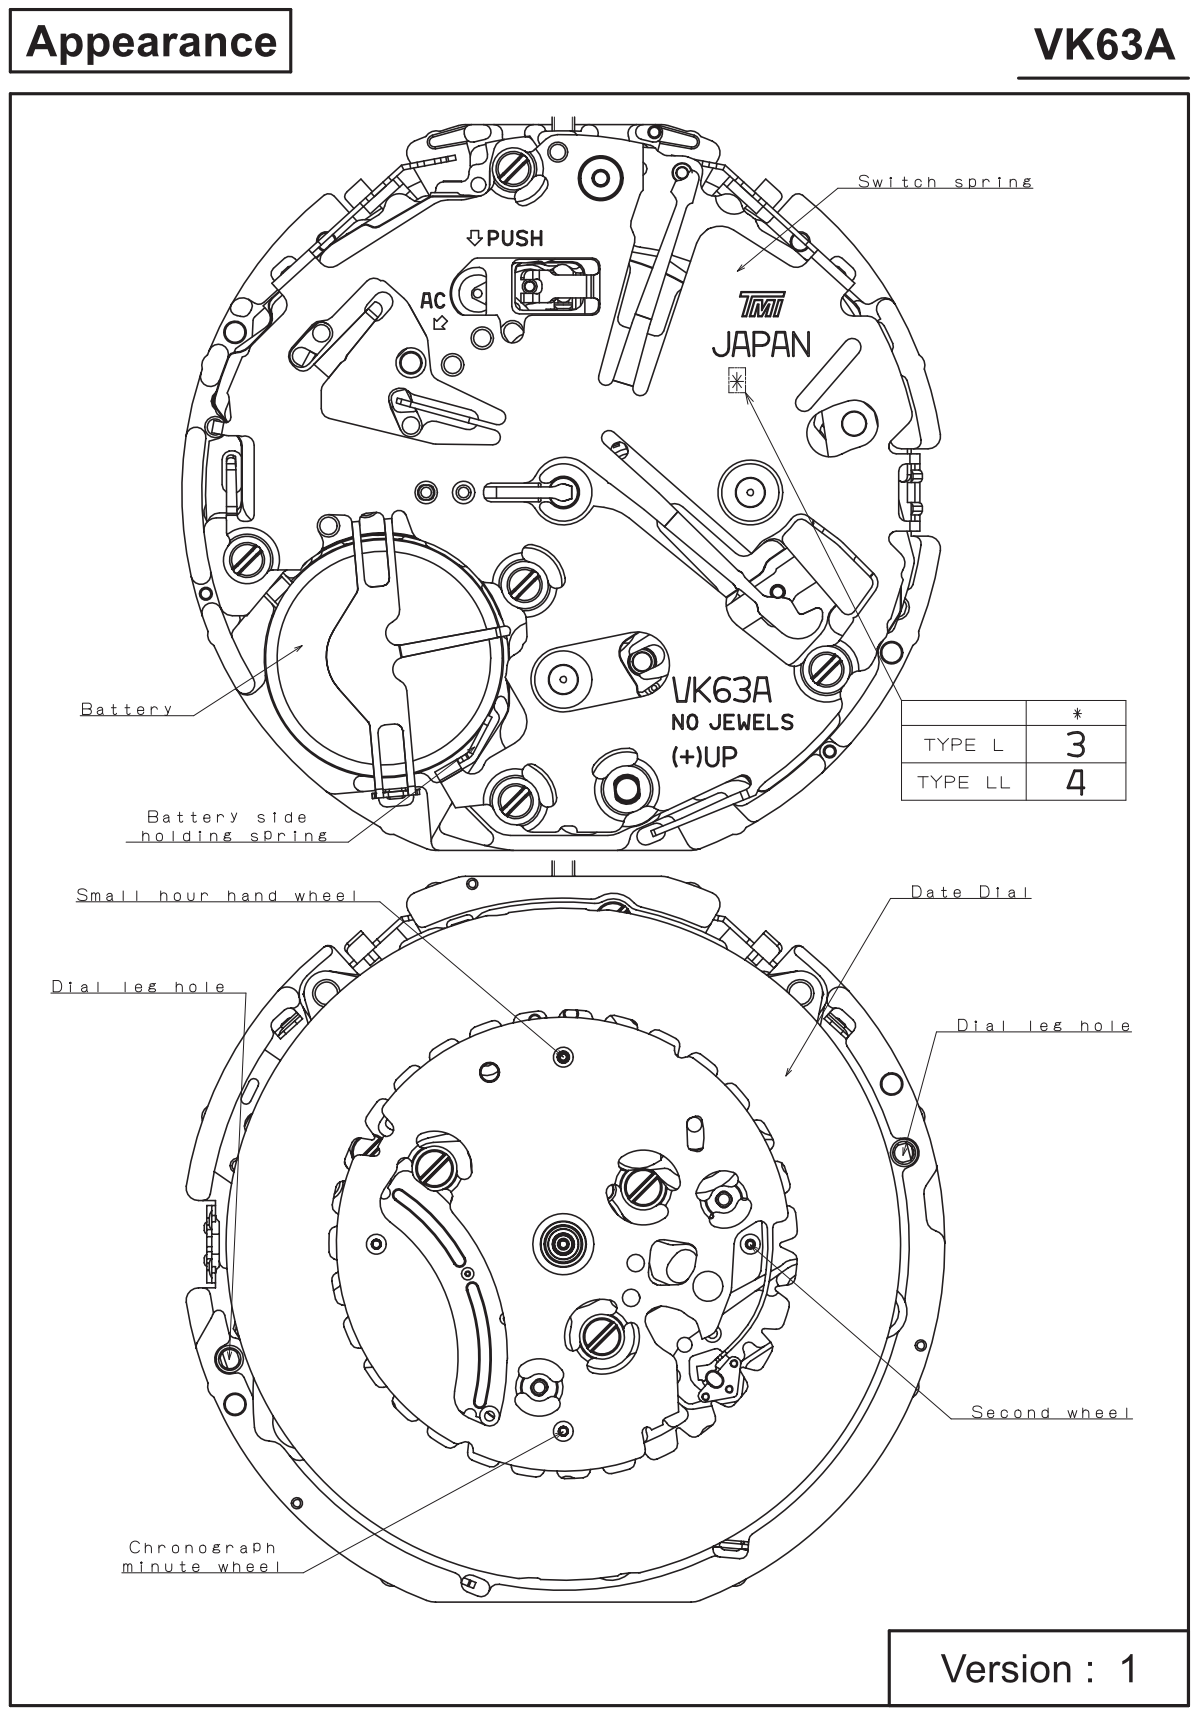
[picture p89: page 3]

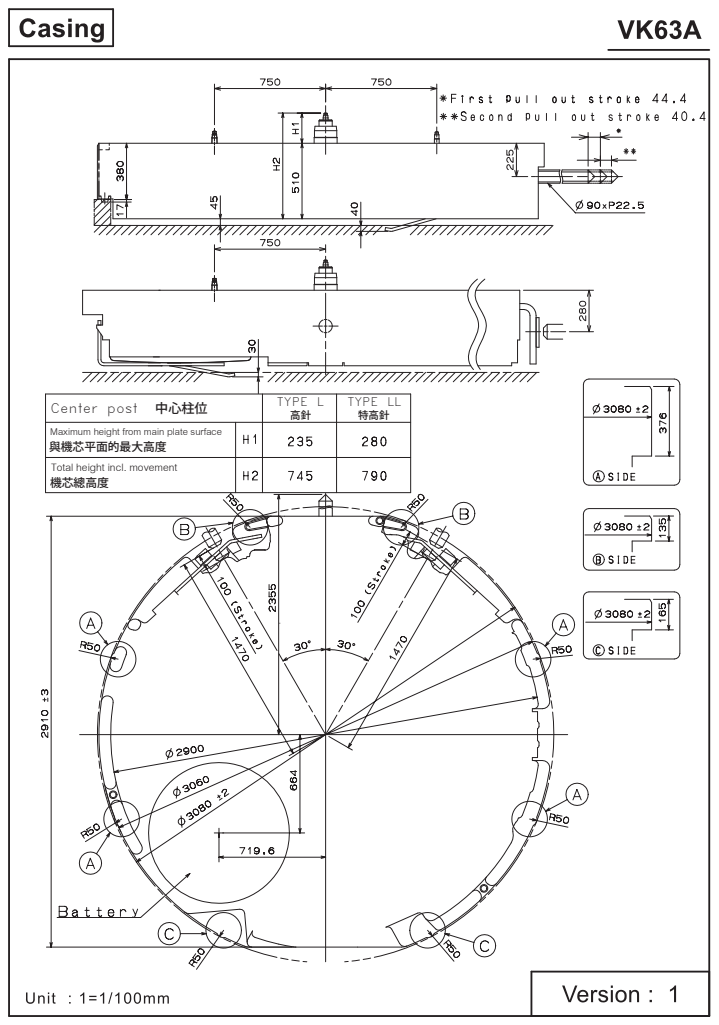
[picture p90: page 4]

Center post 中心柱位 | TYPE L 高針 | TYPE LL 特高針

0D[LPXPKHLJKWIURPPDLQSODWHVXUIDFH 與機芯平面的最大高度

7RWDOKHLJKWLQFOPRYHPHQW 機芯總高度

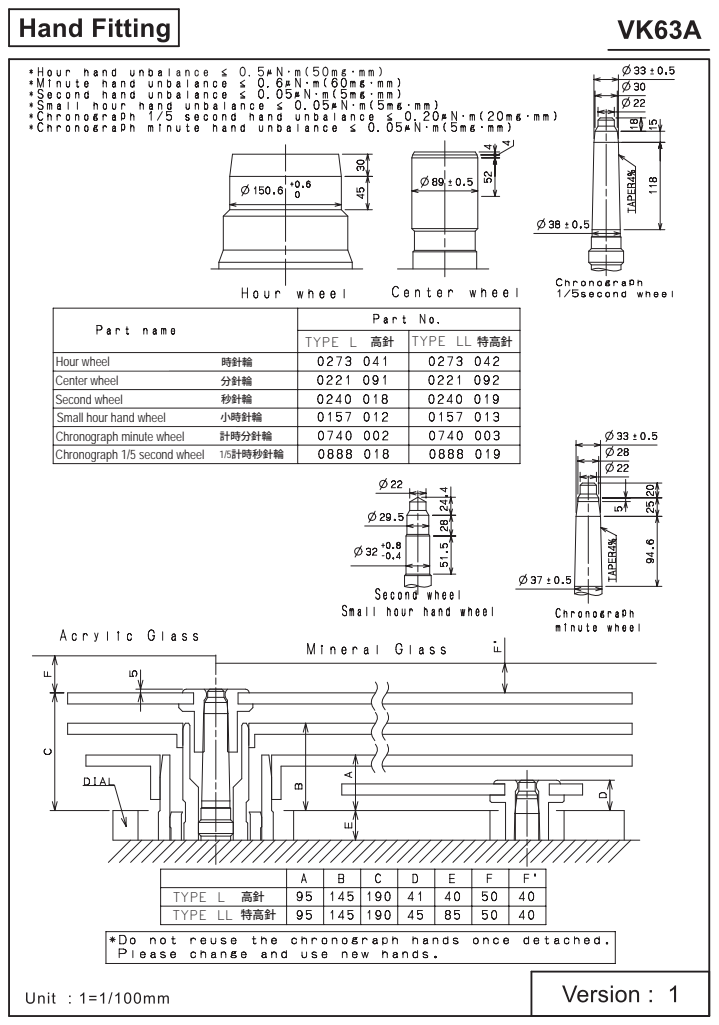
[picture p91: page 5]
TYPE L 高針; TYPE LL; 1/5計時秒針輪; 計時分針輪; 秒針輪; 分針輪; 時針輪; 特高針; Small hour hand wheel; 小時針輪; TYPE L

Hour wheel
Center wheel
Second wheel
Chronograph minute wheel
Chronograph 1/5 second wheel

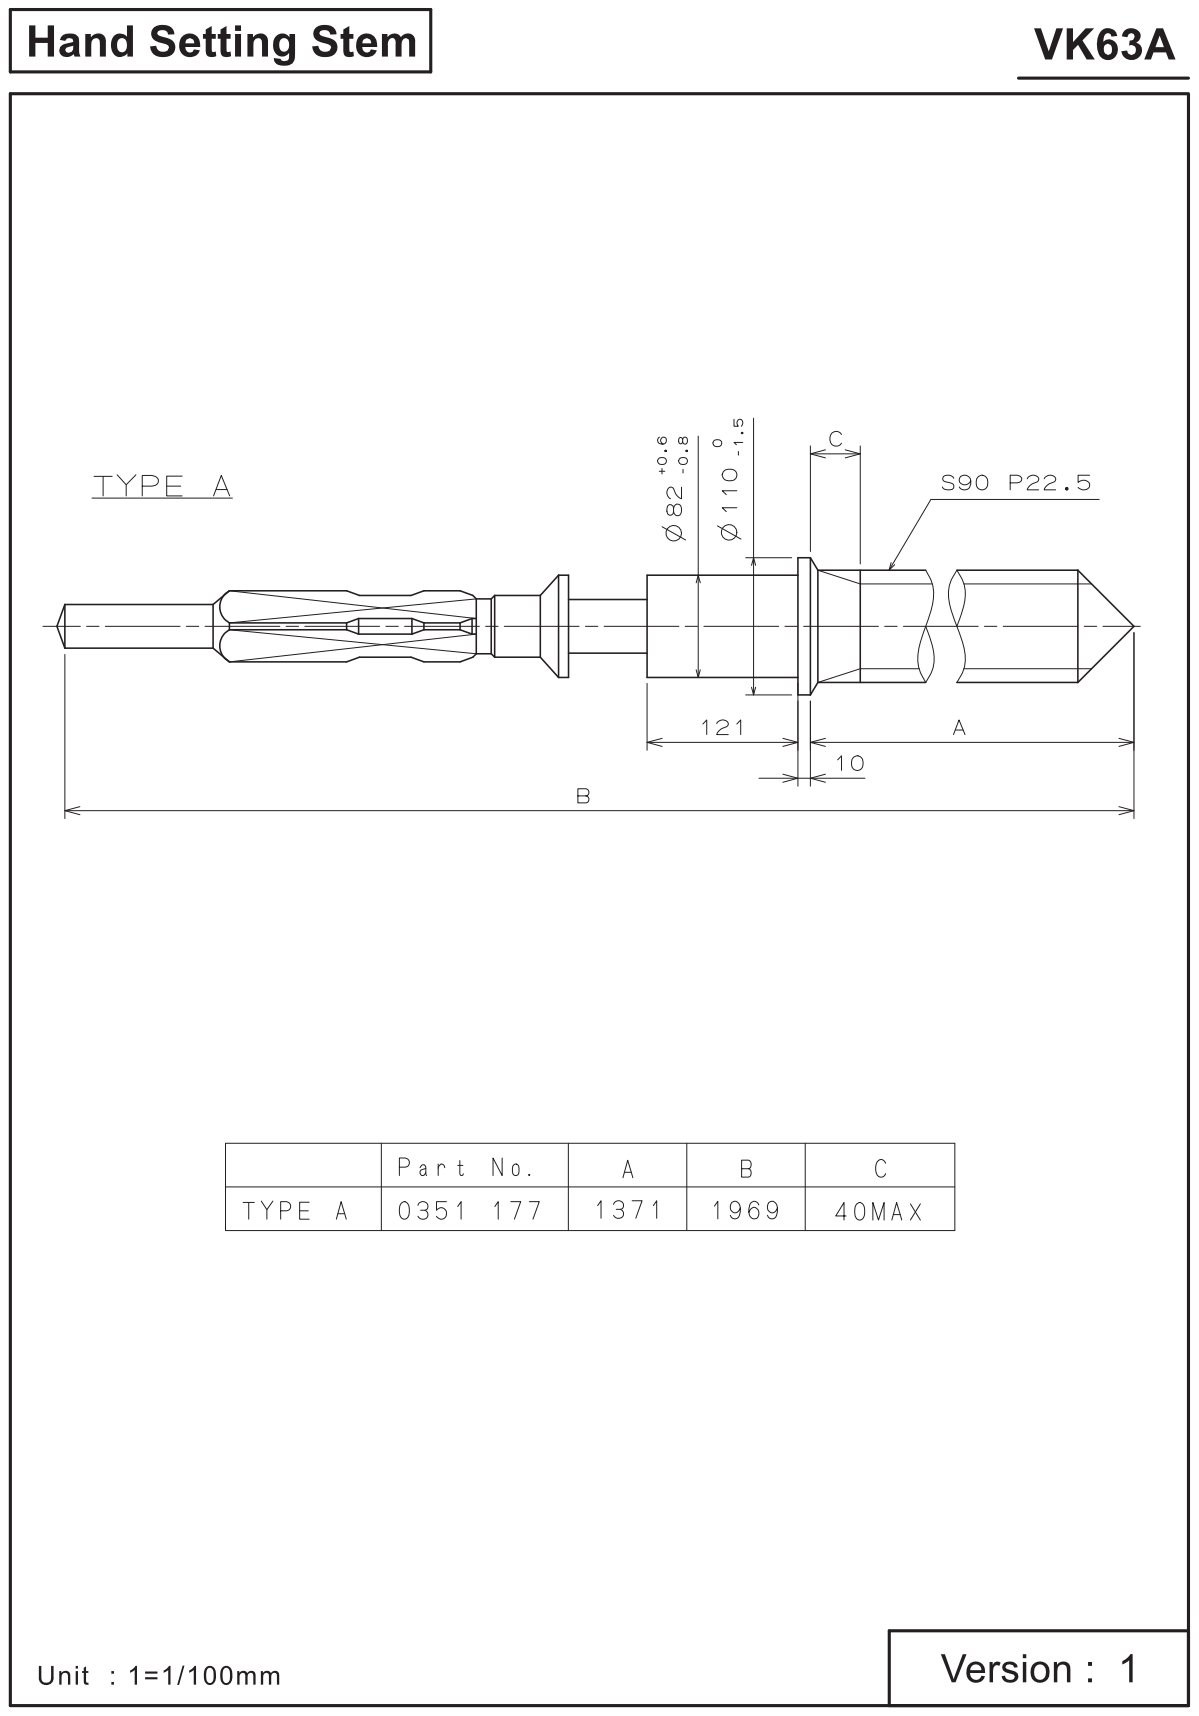
[picture p92: page 6]

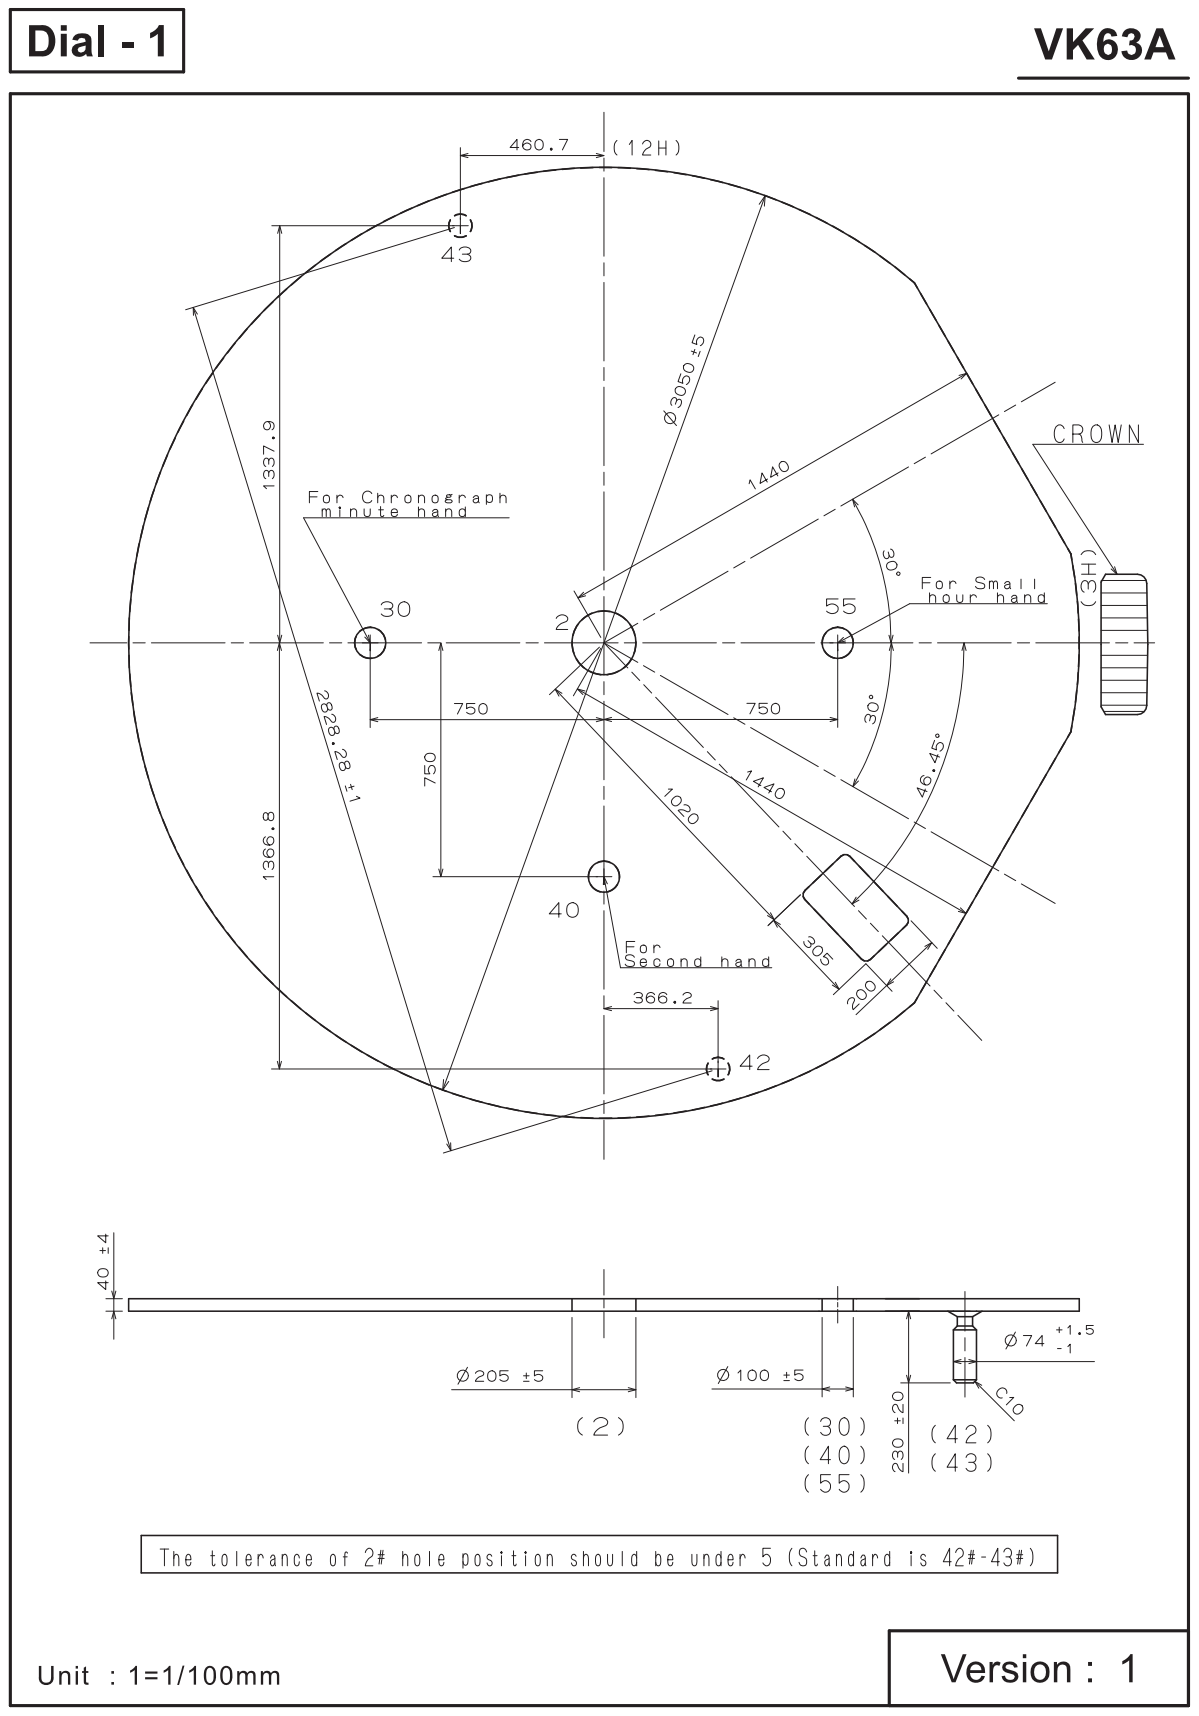
[picture p93: page 7]

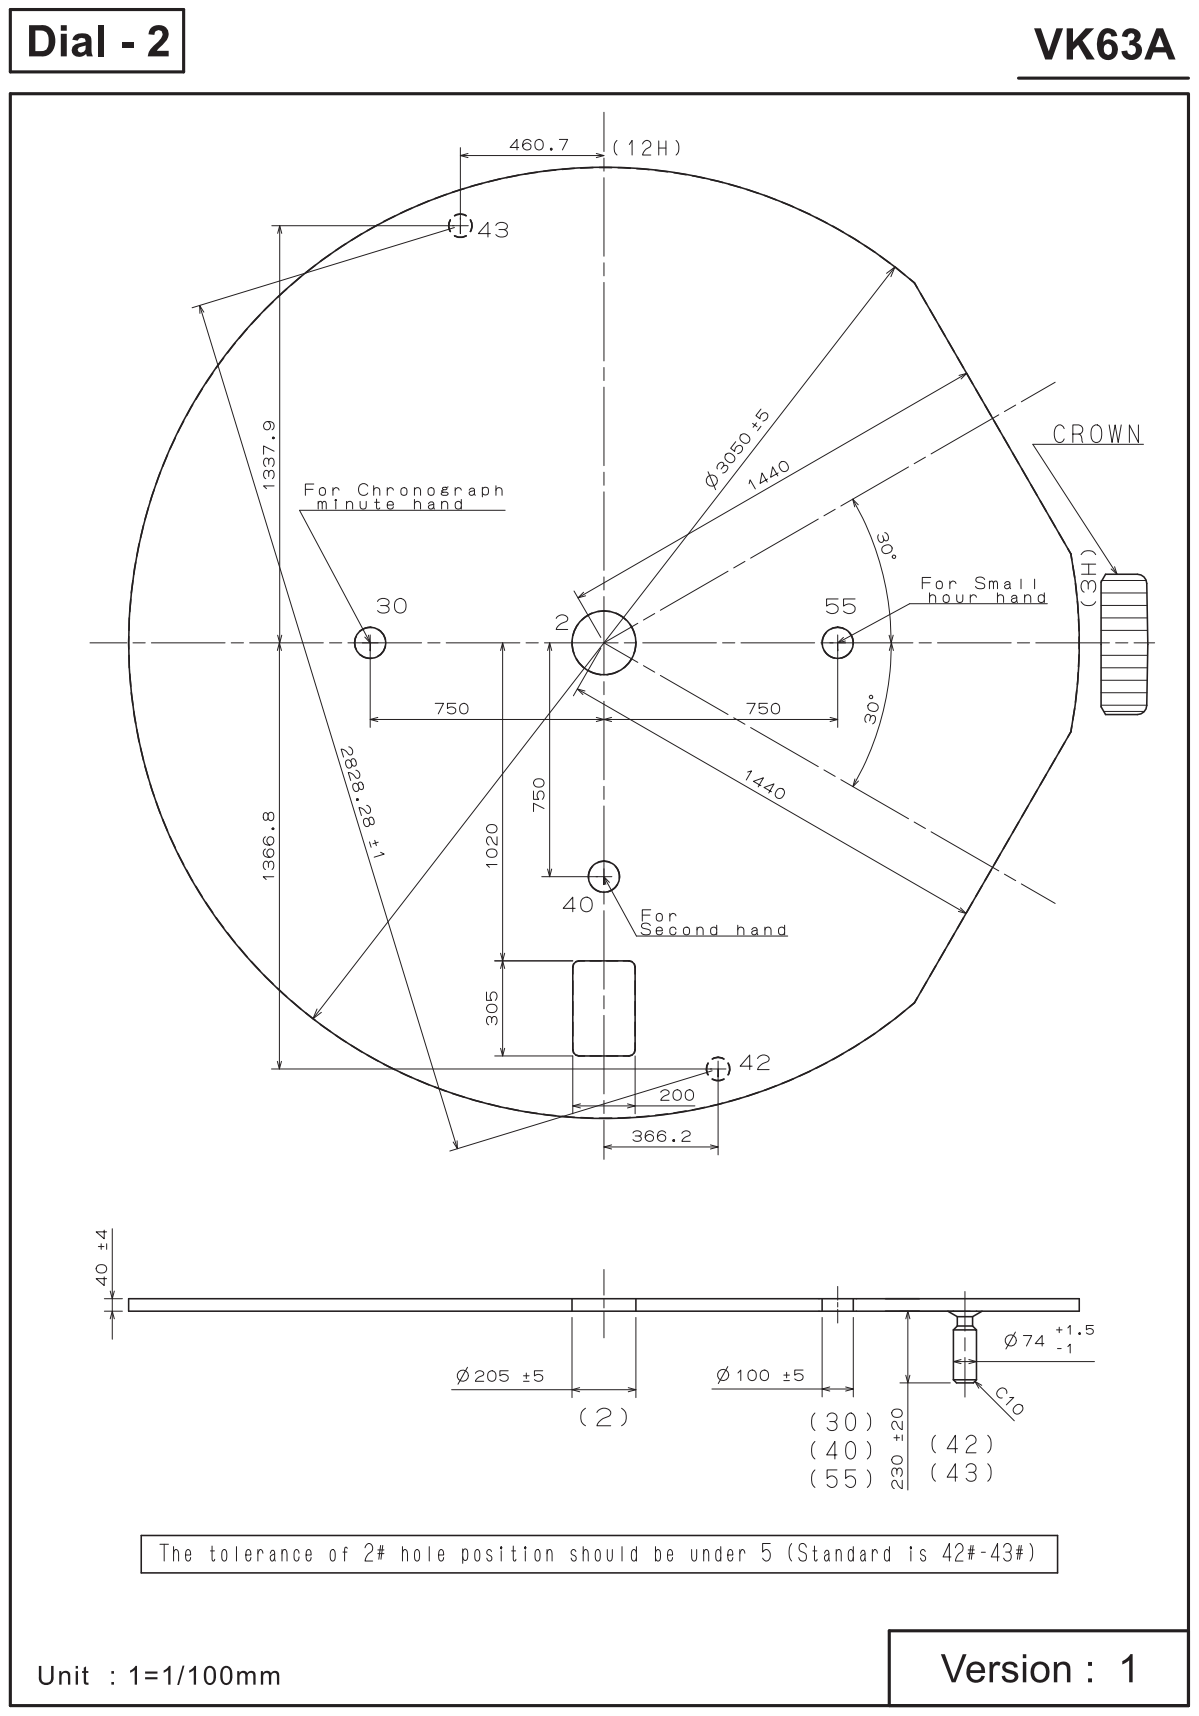
[picture p94: page 8]

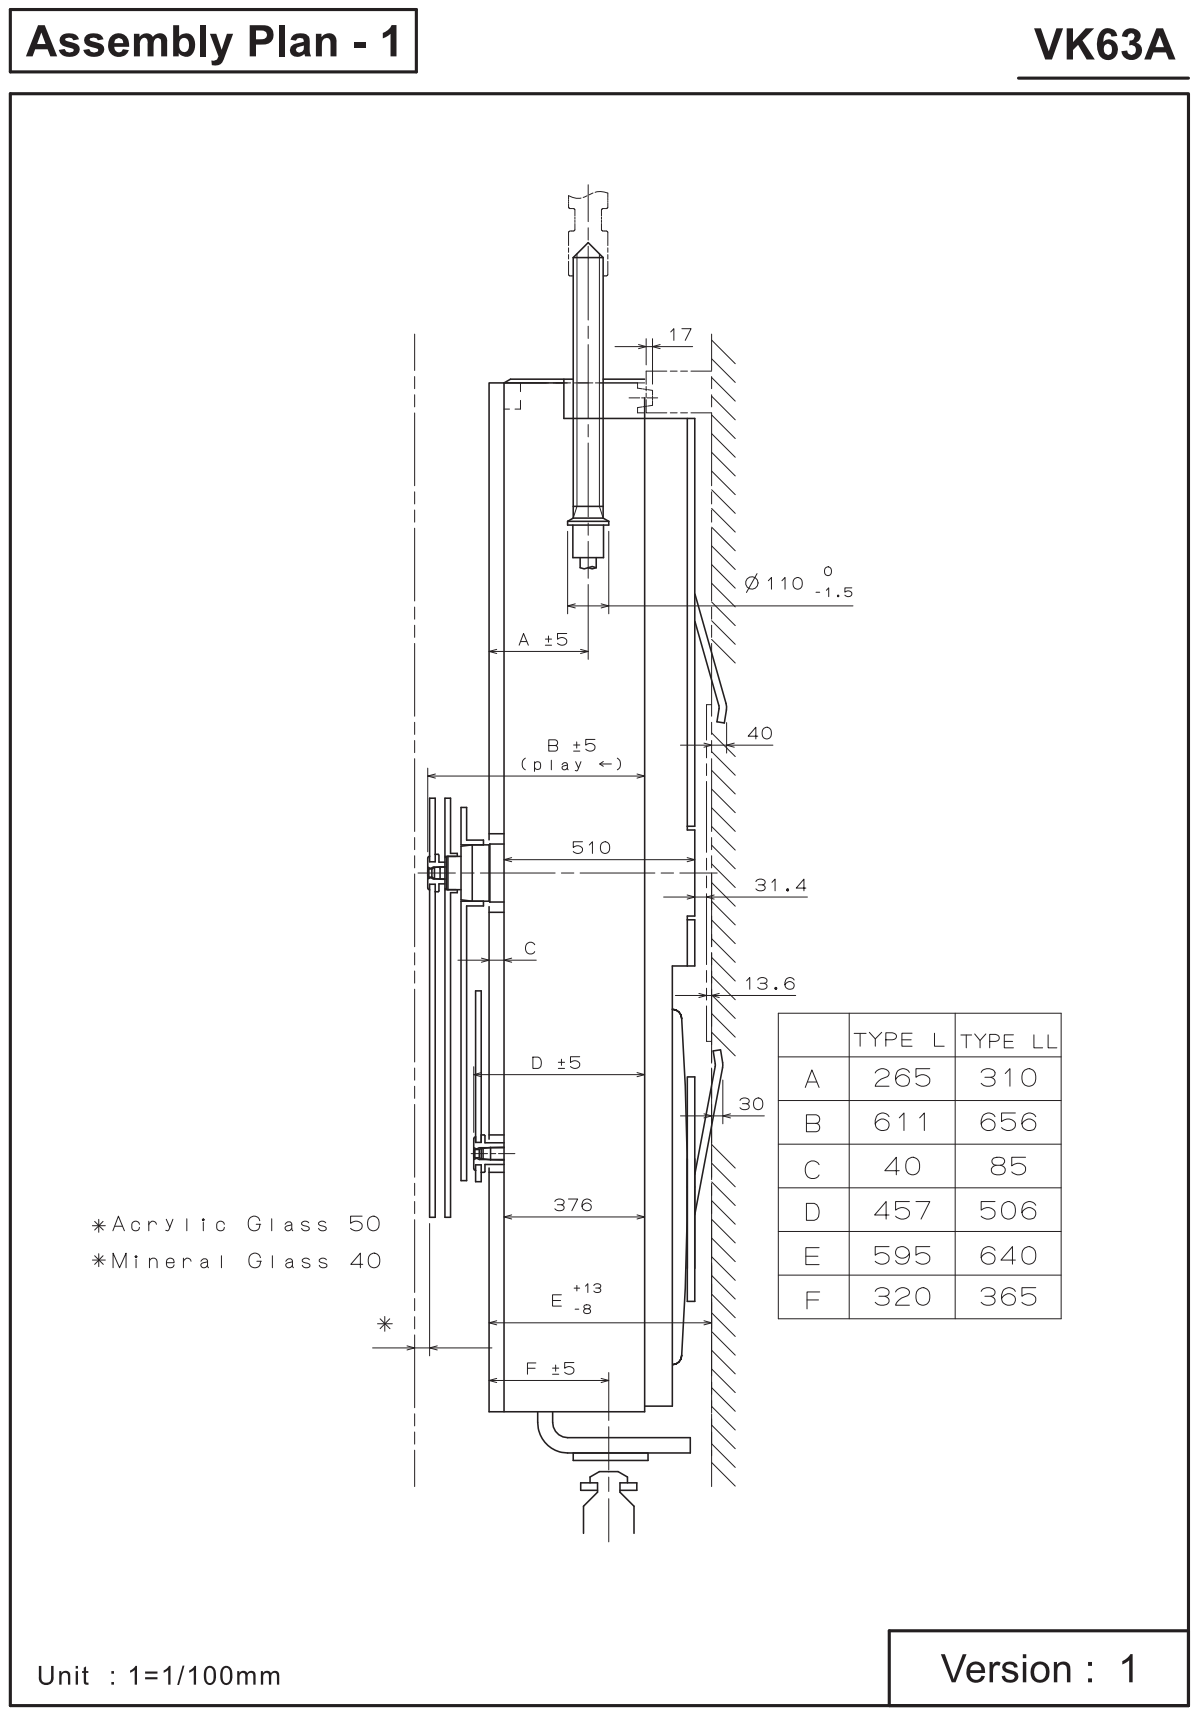
[picture p95: page 9]

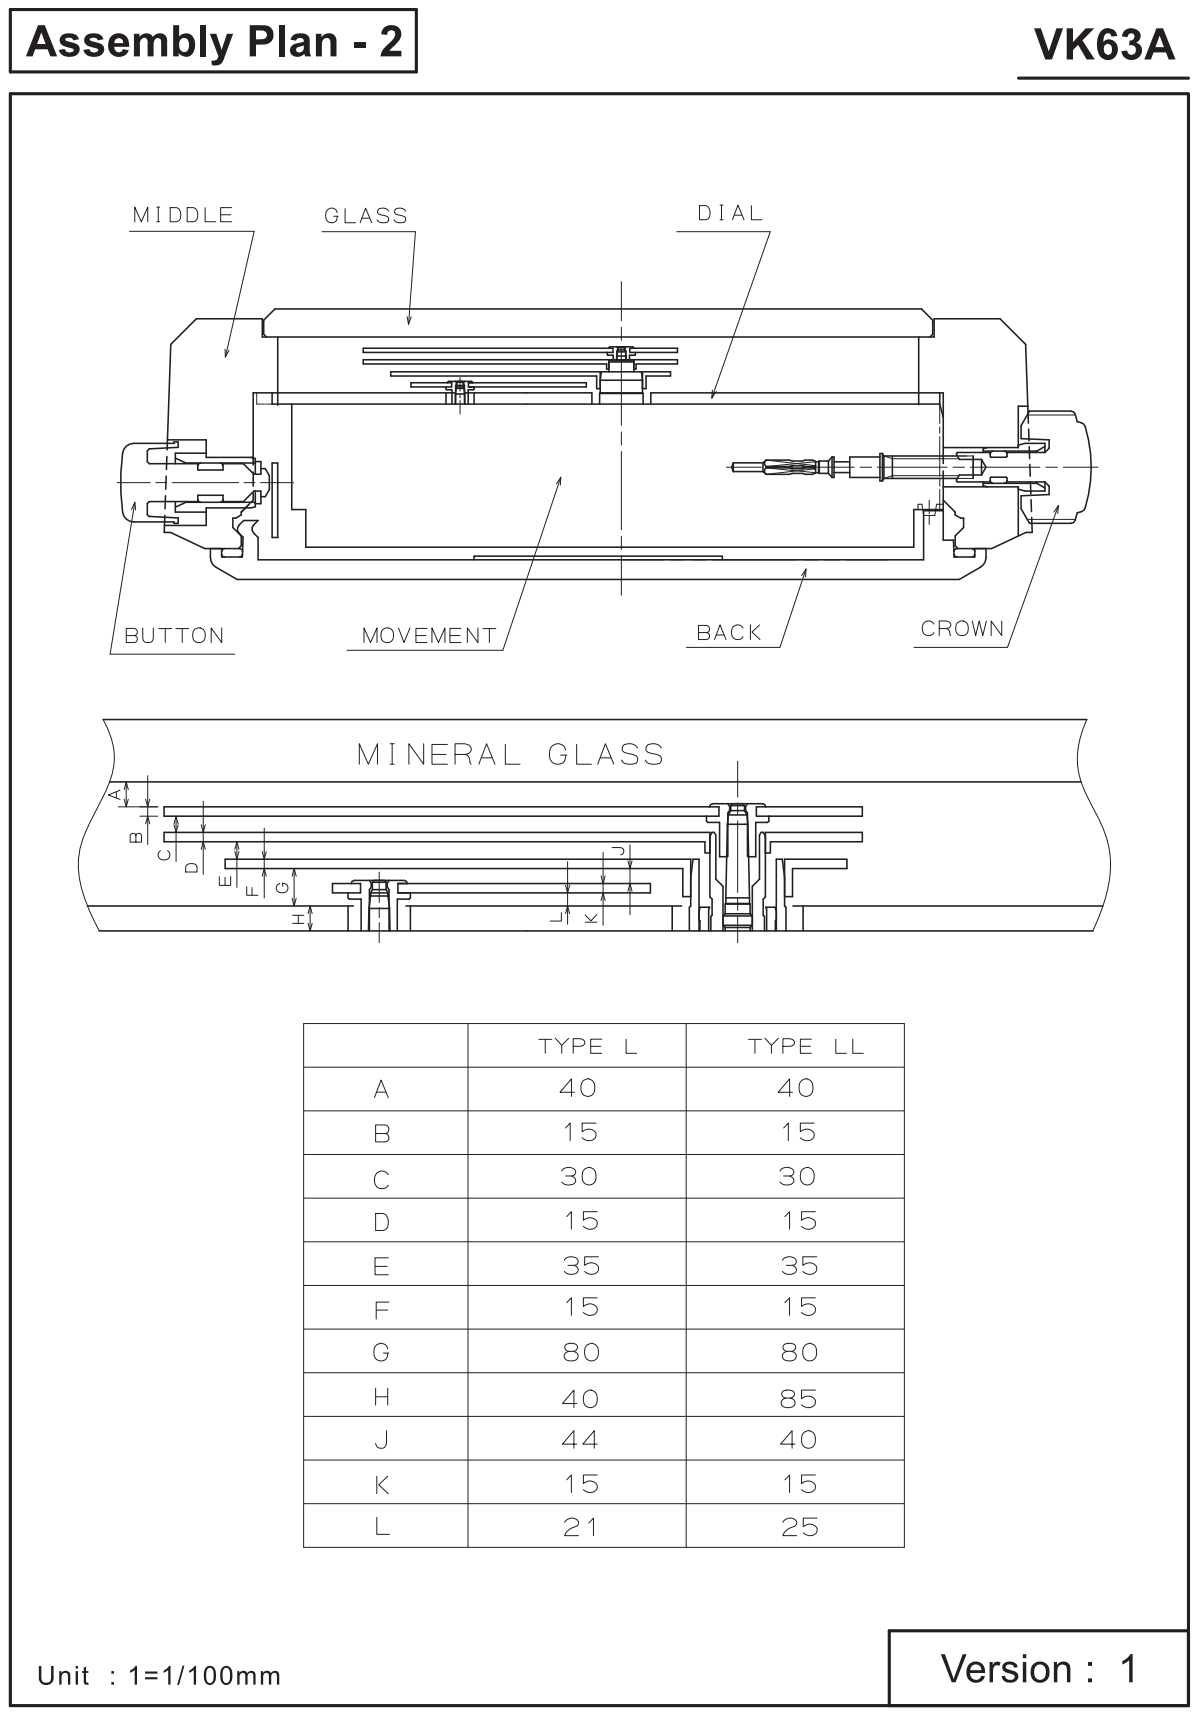
[picture p96: page 10]

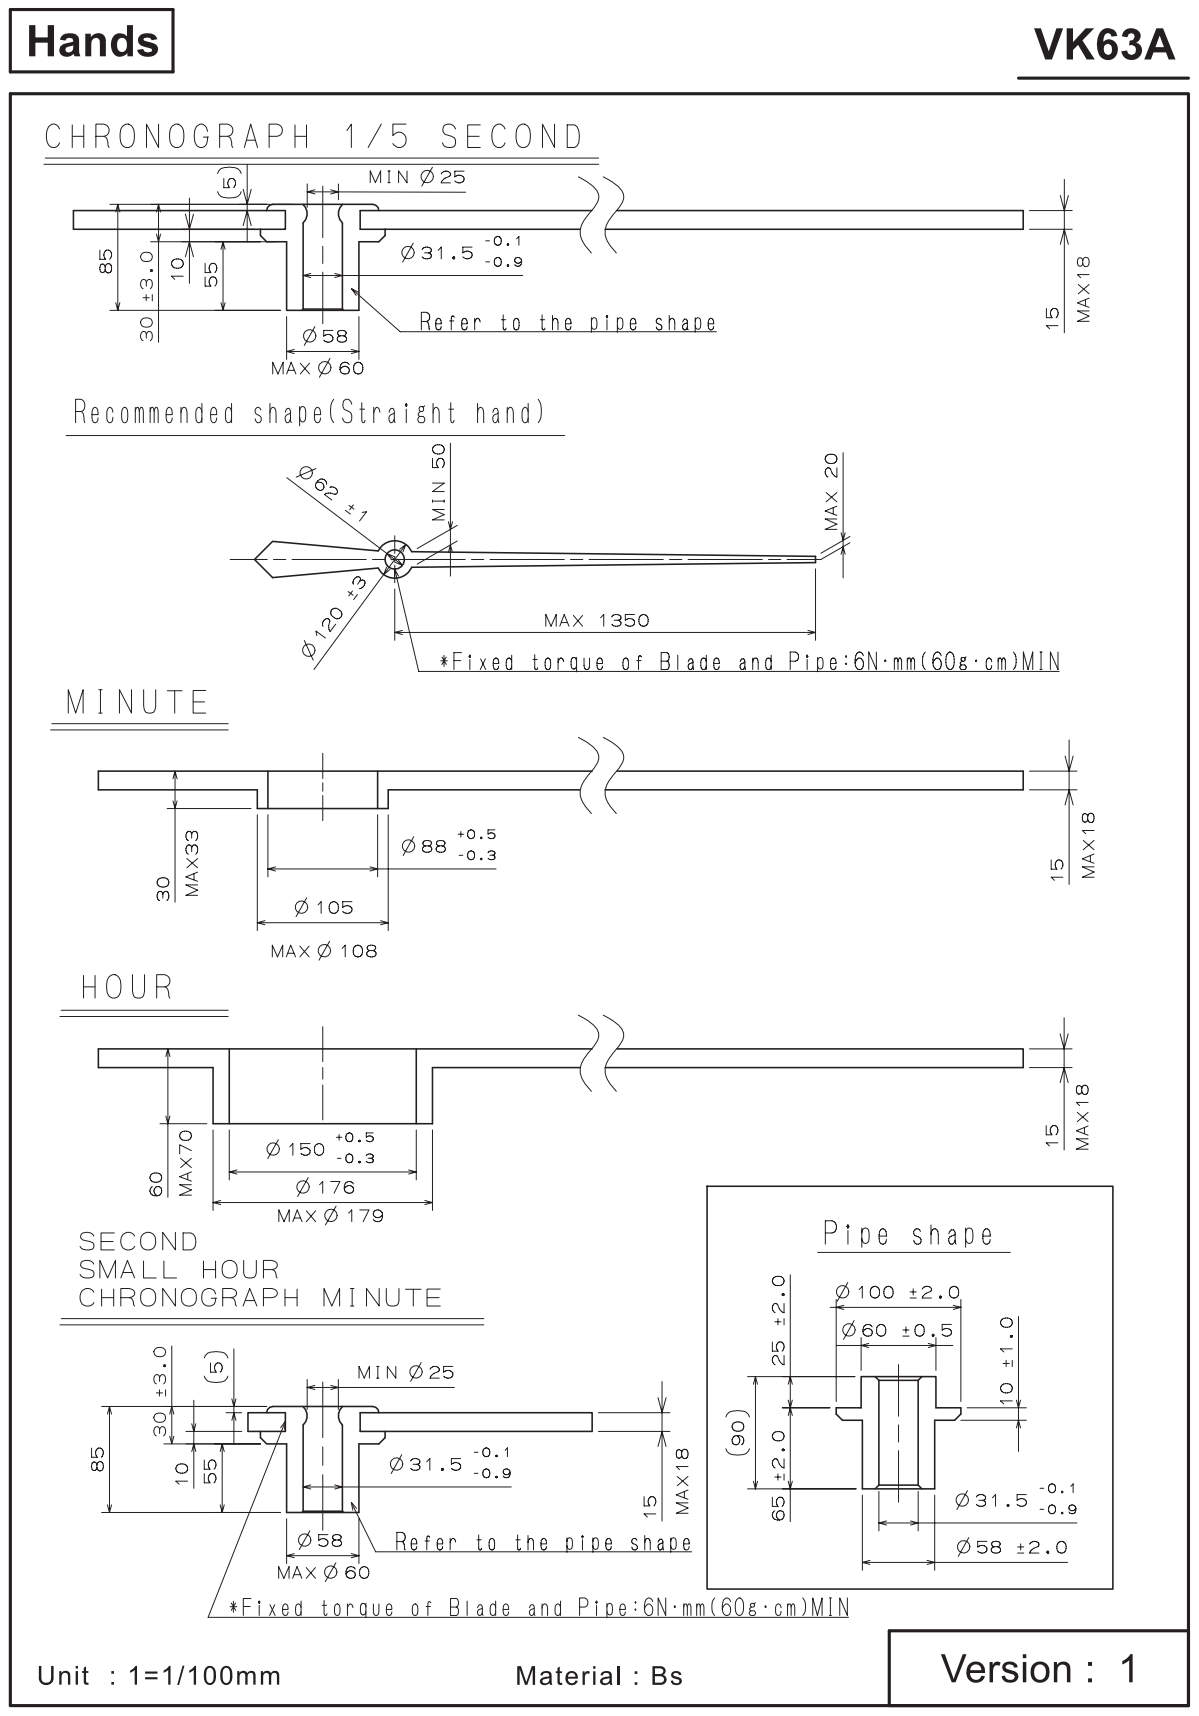
[picture p97: page 11]
