201590022033/Dial-New-Design.01/docs/research/crown-c0-2026-10-10/NH05_SS.pdf

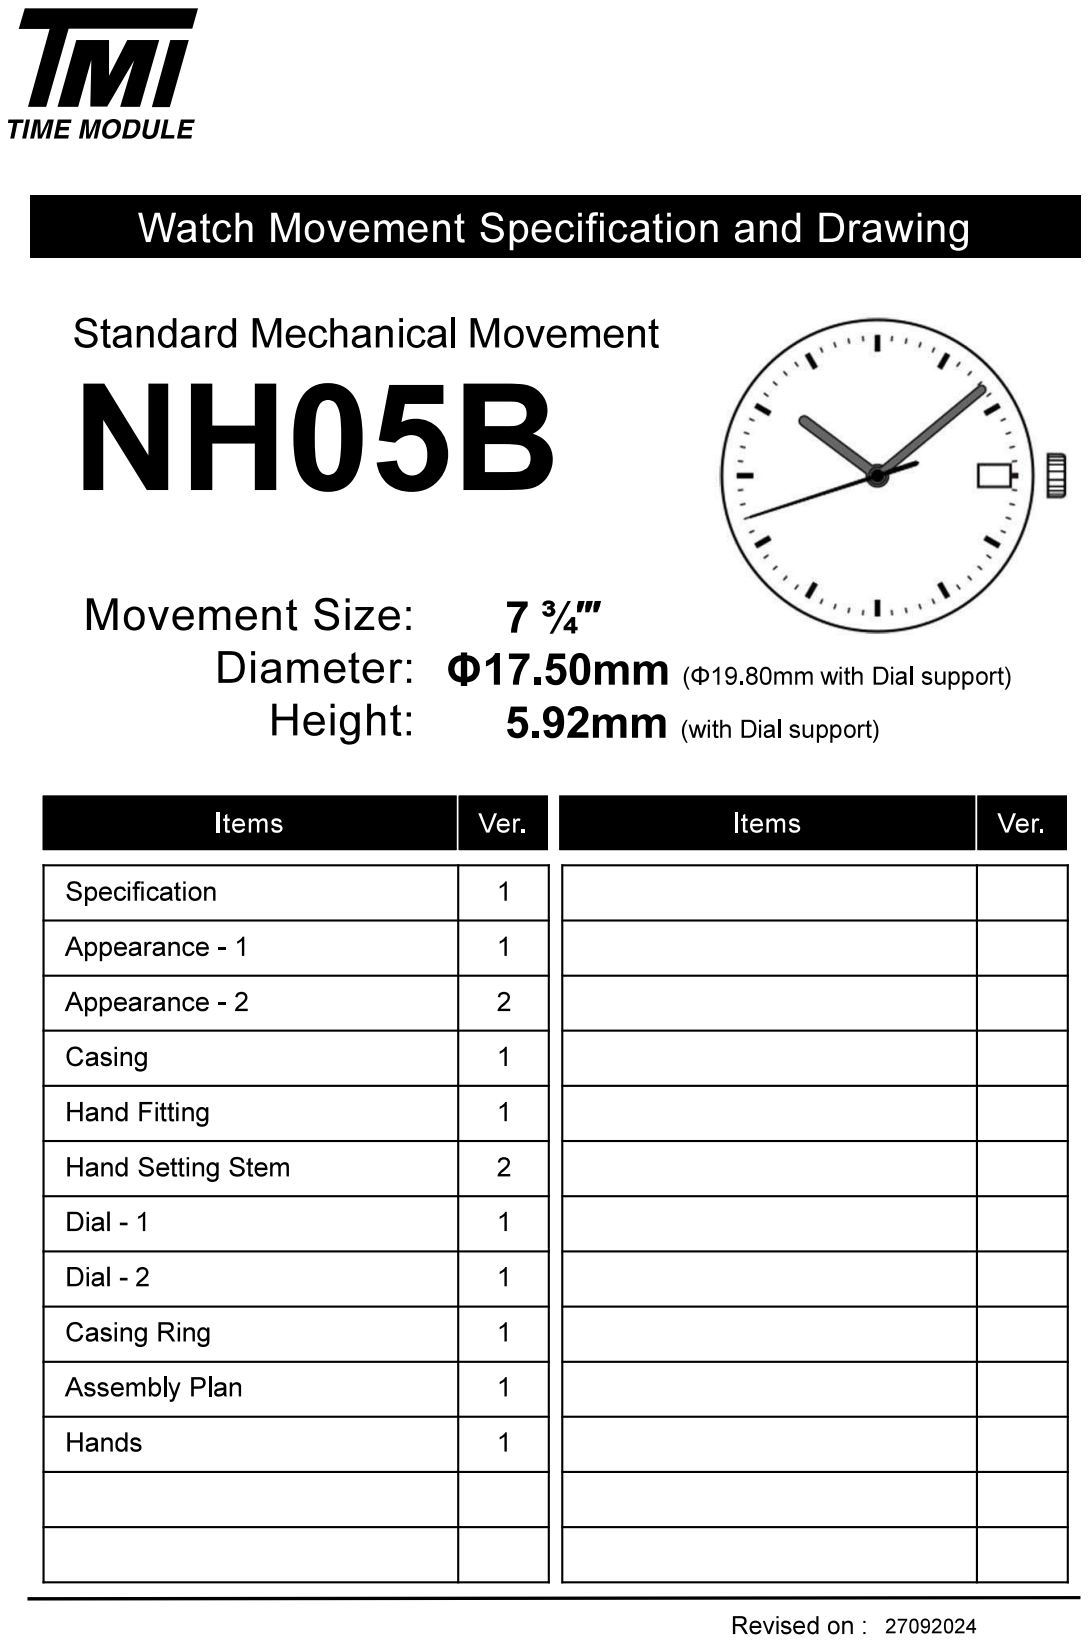
[picture p104: page 1]

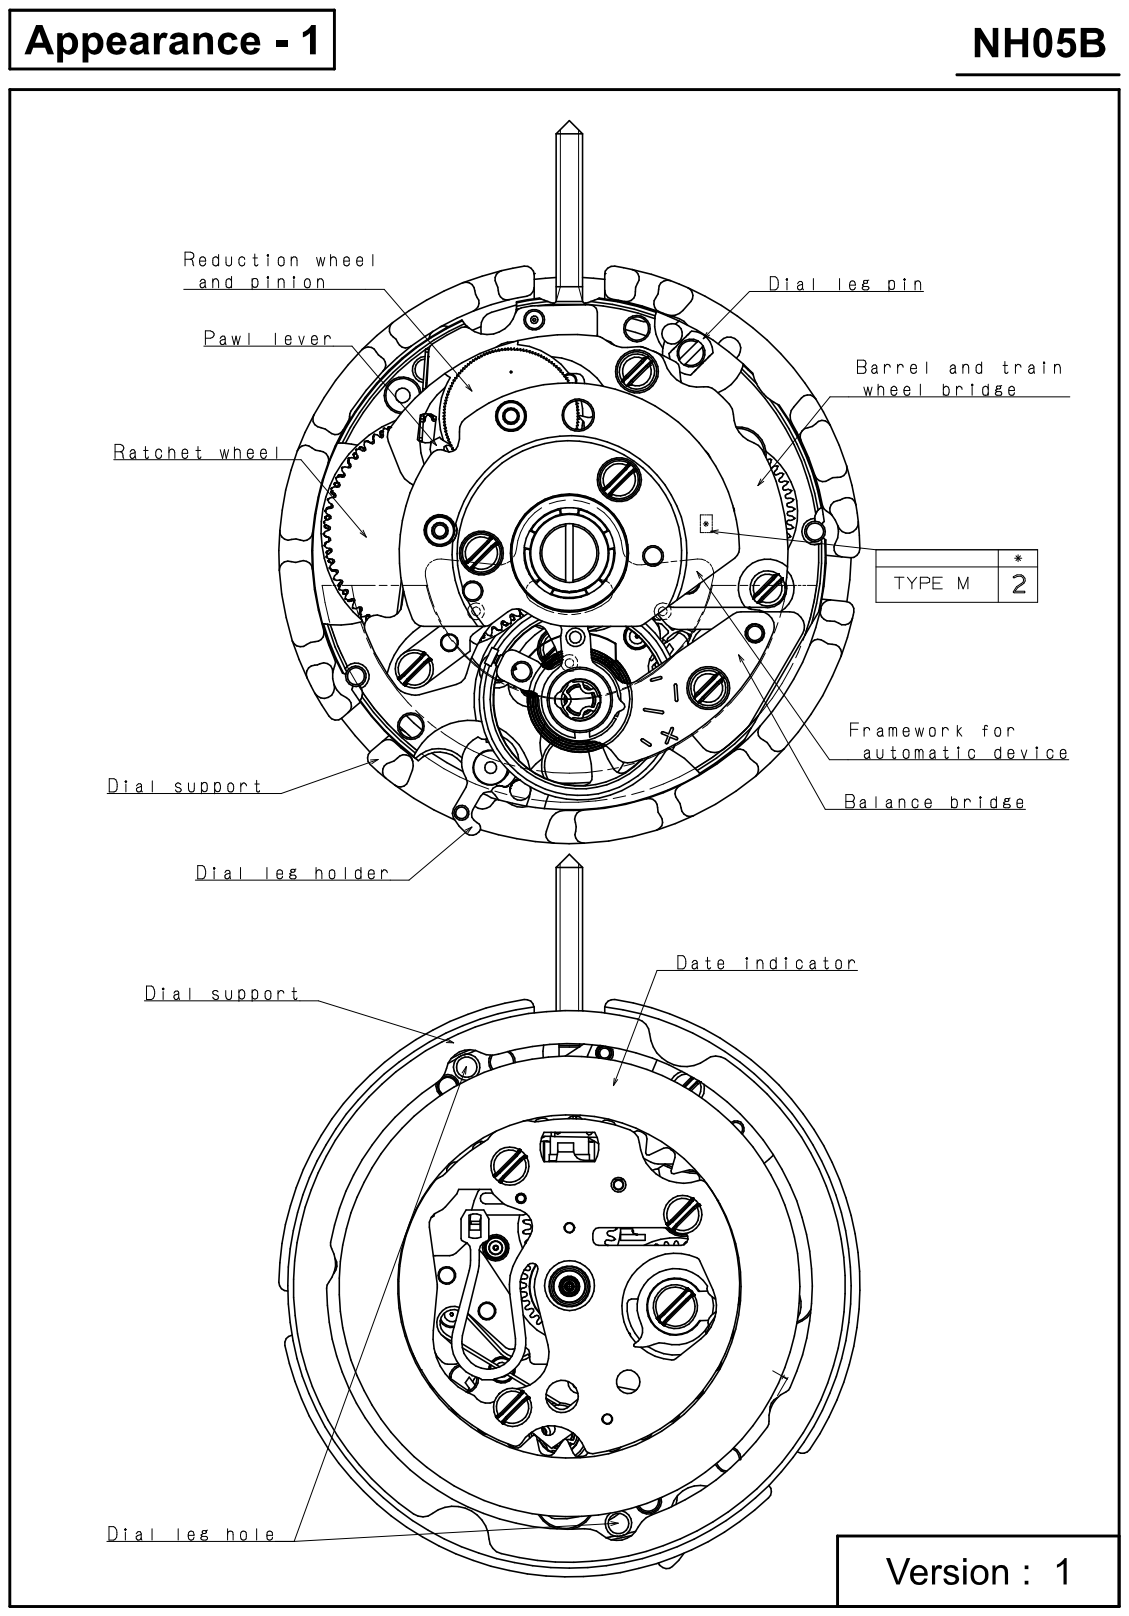
[picture p105: page 3]

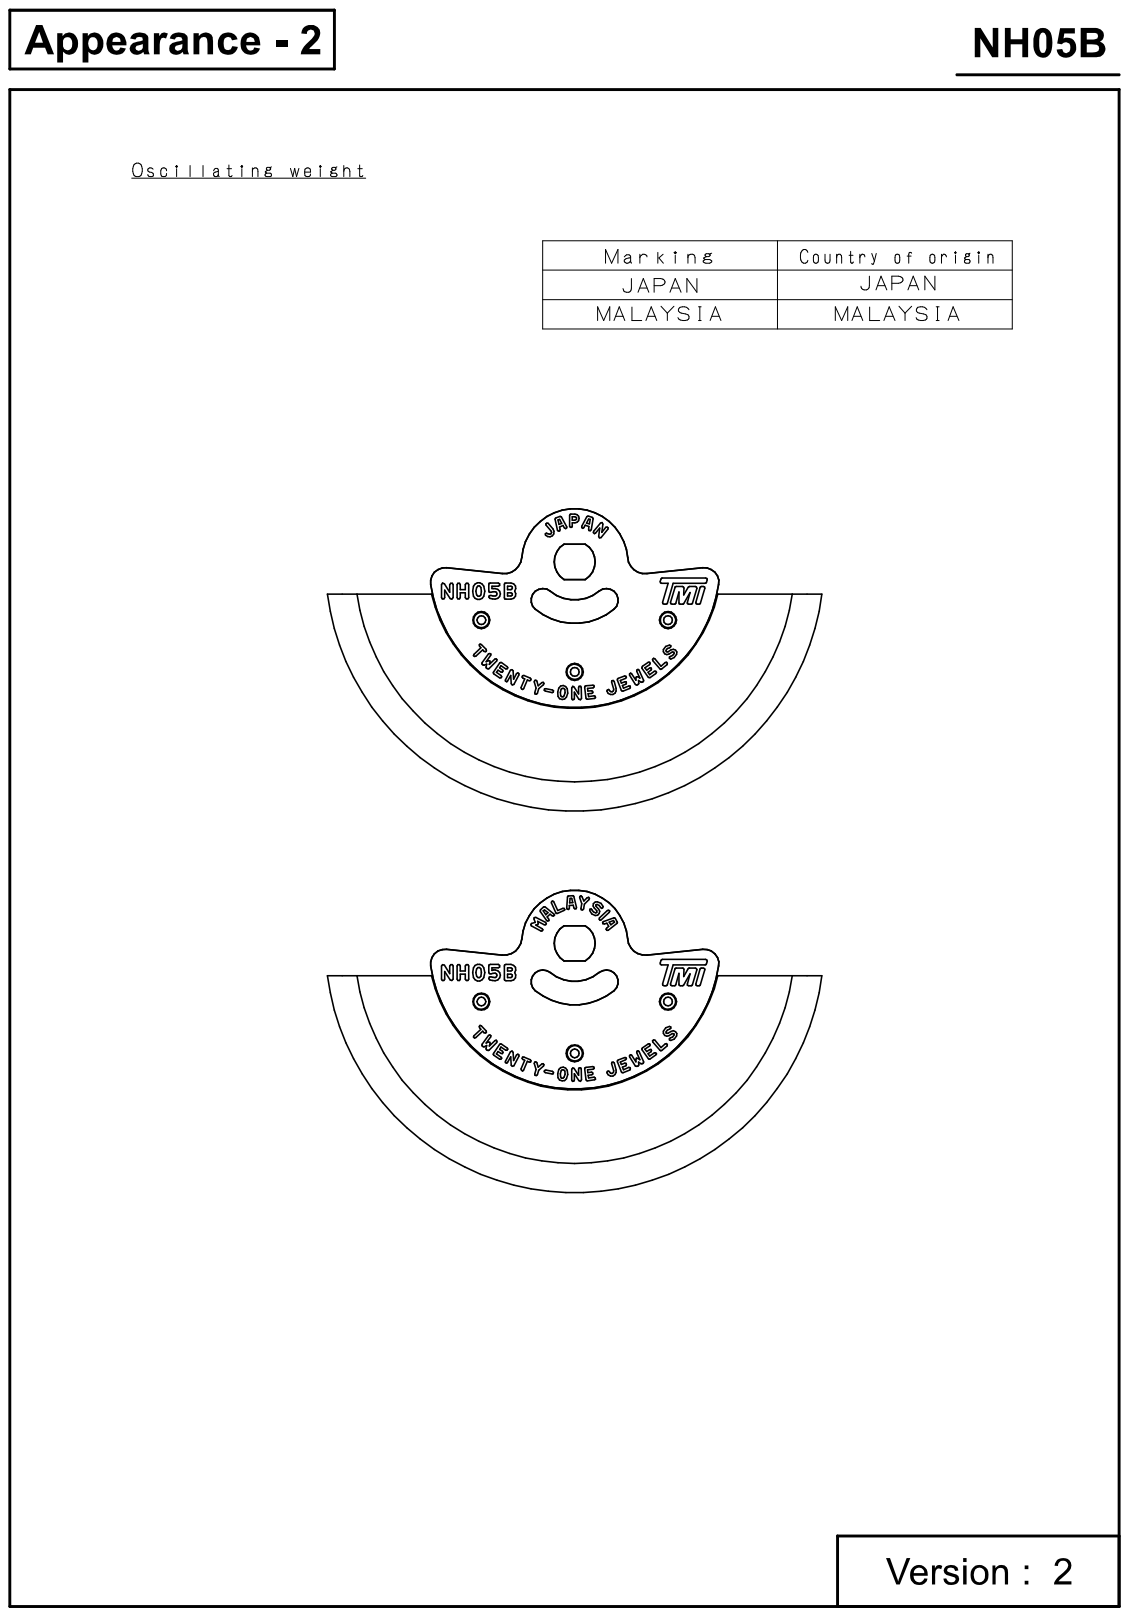
[picture p106: page 4]

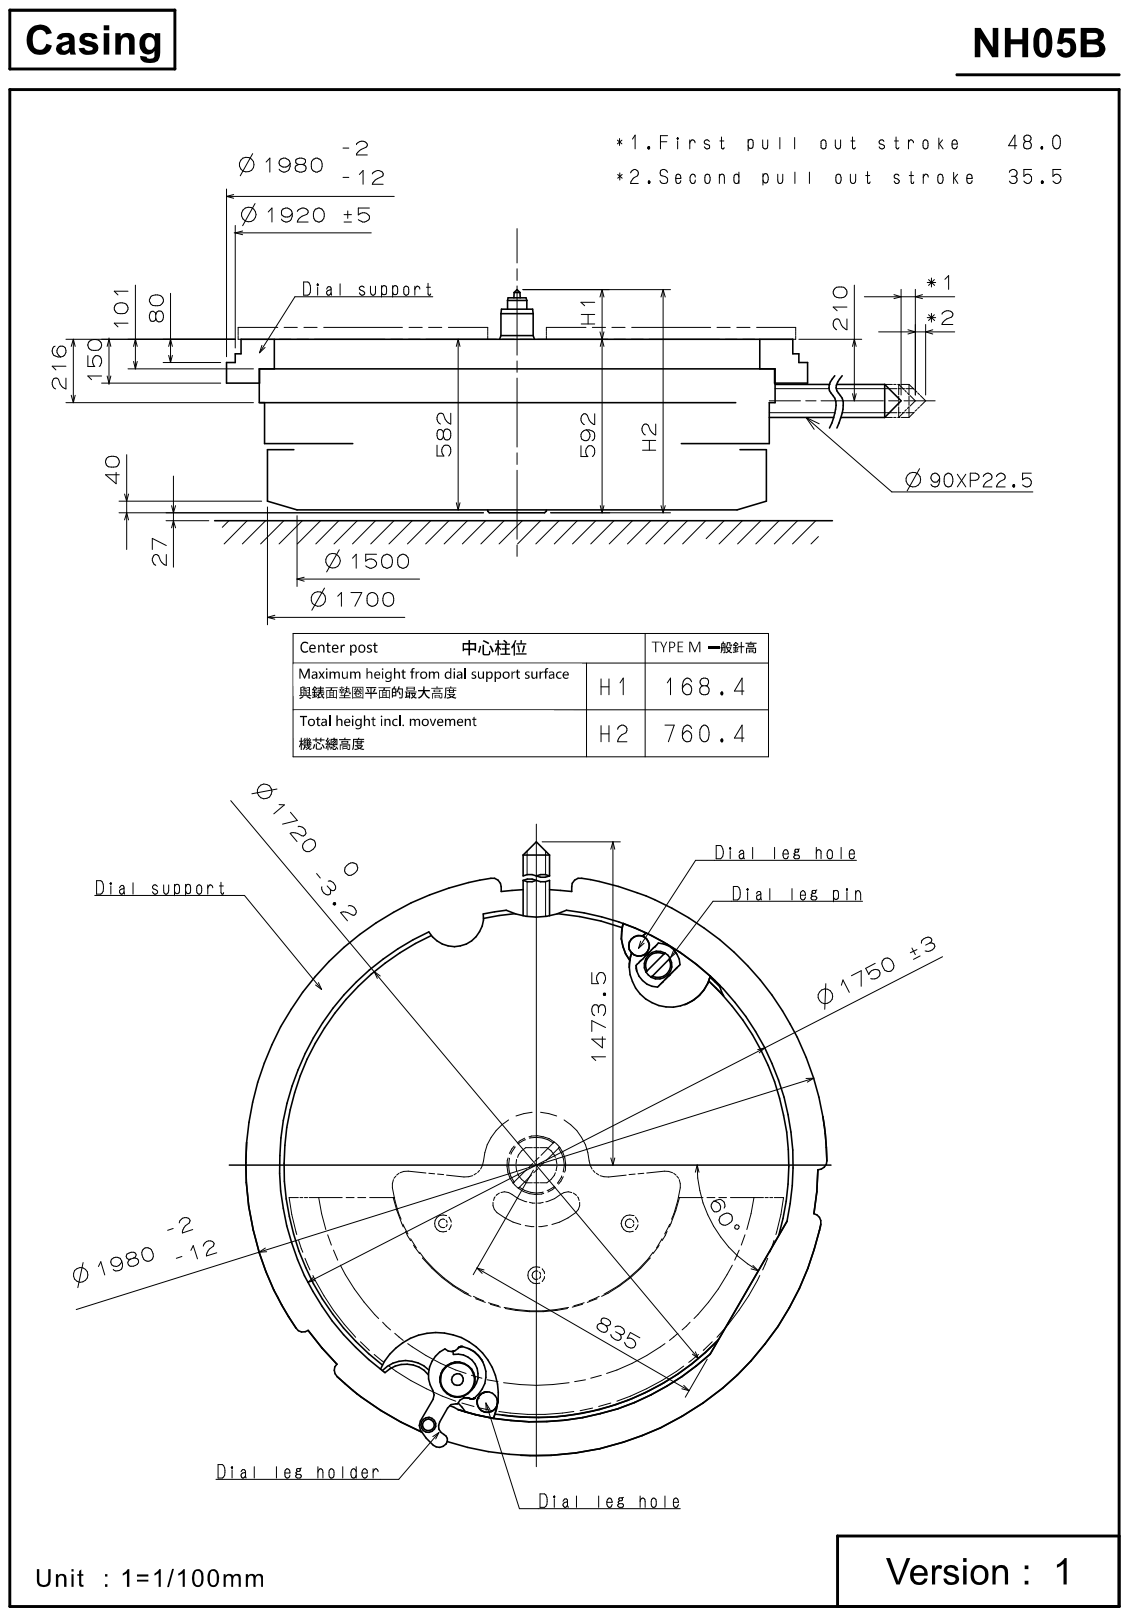
[picture p107: page 5]

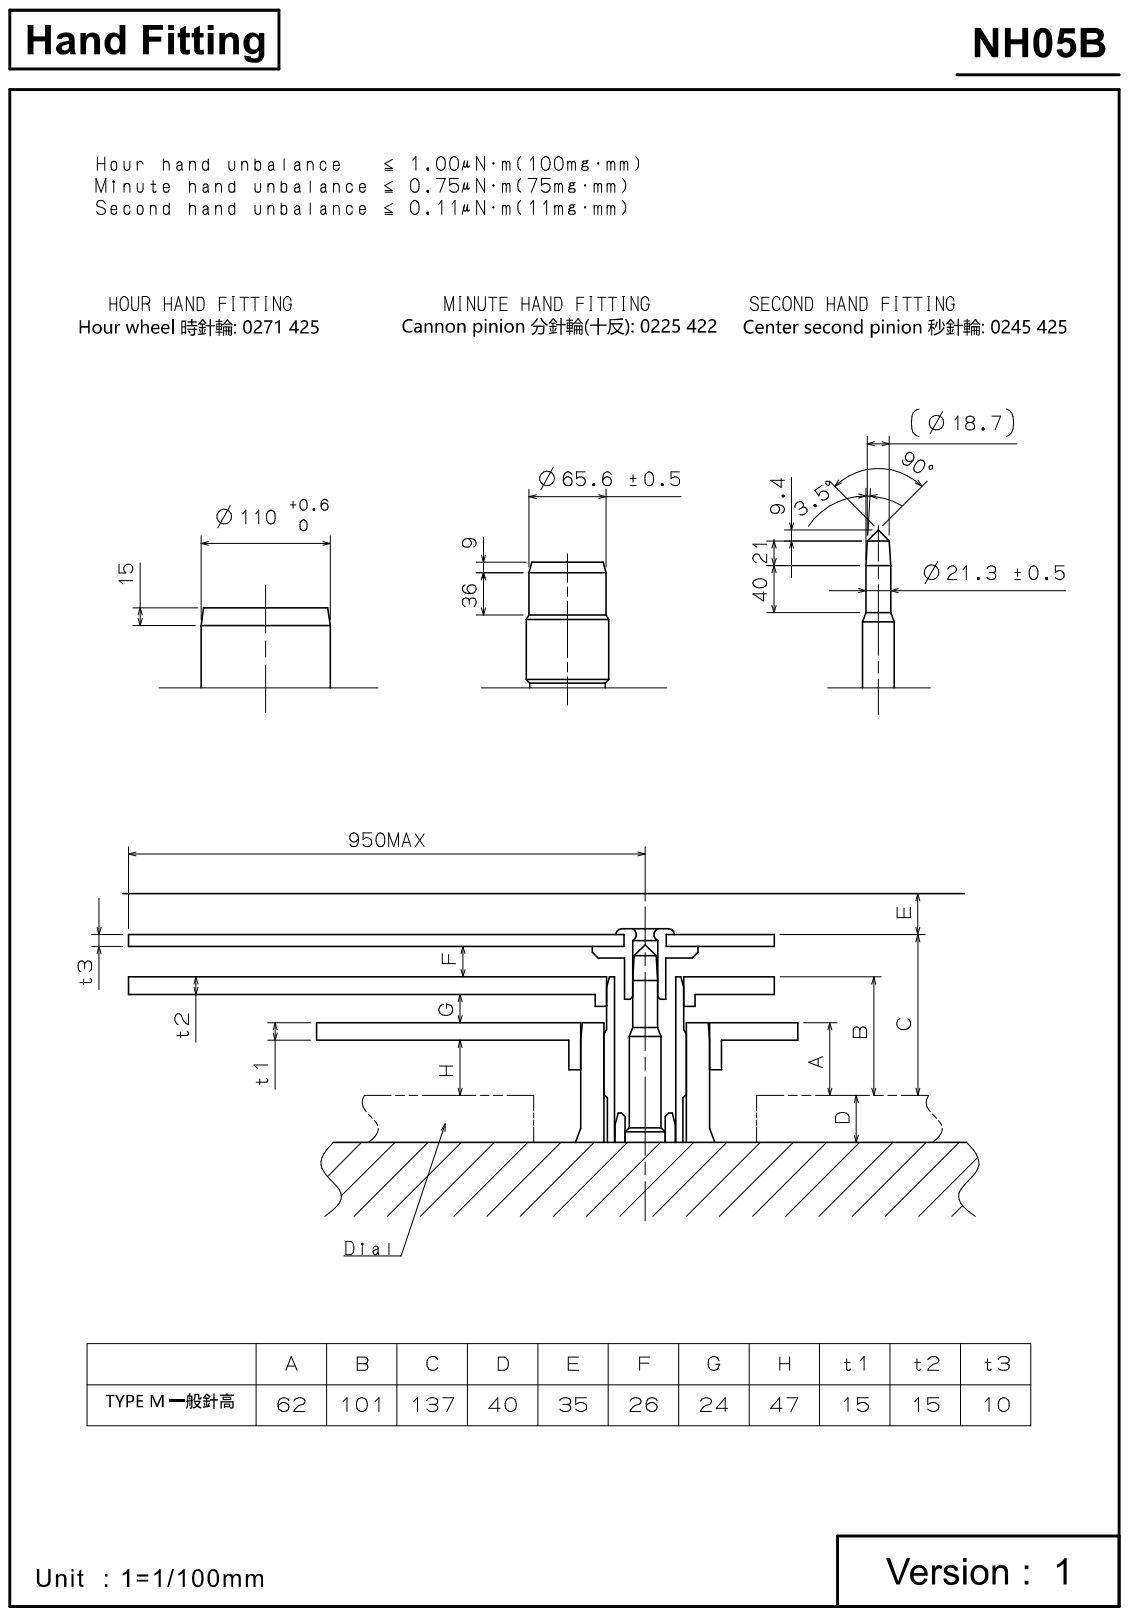
[picture p108: page 6]

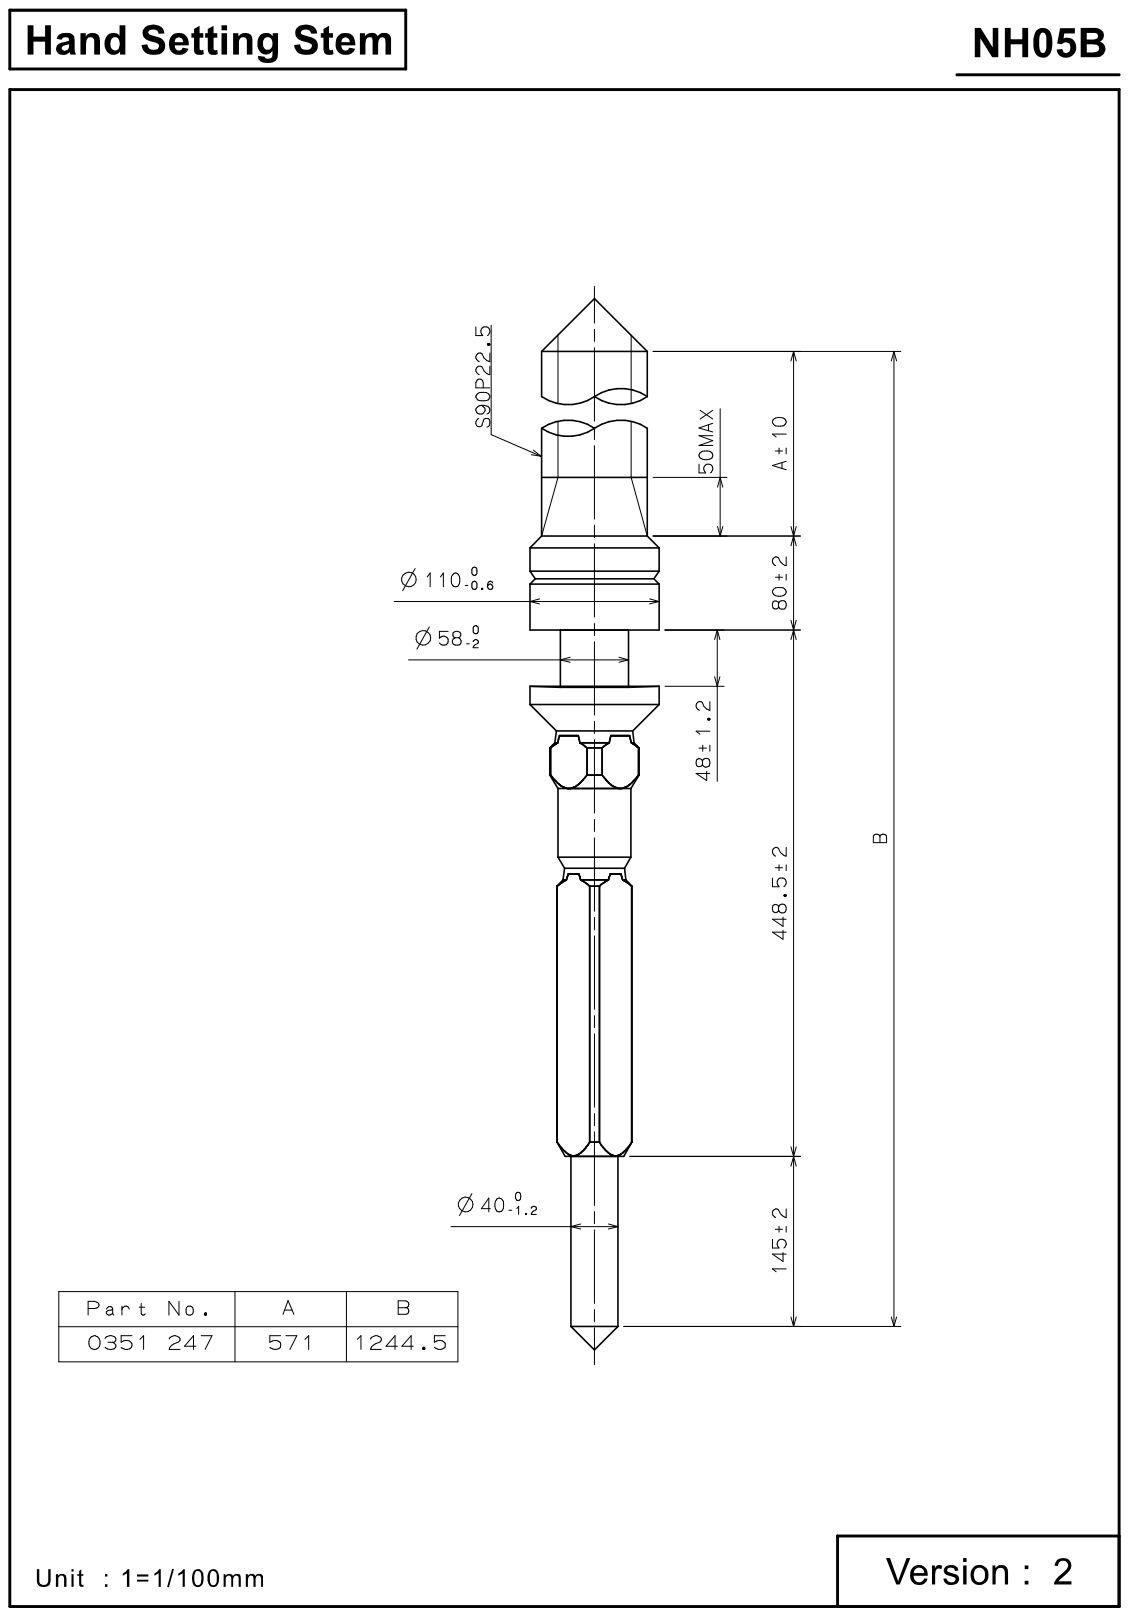
[picture p109: page 7]

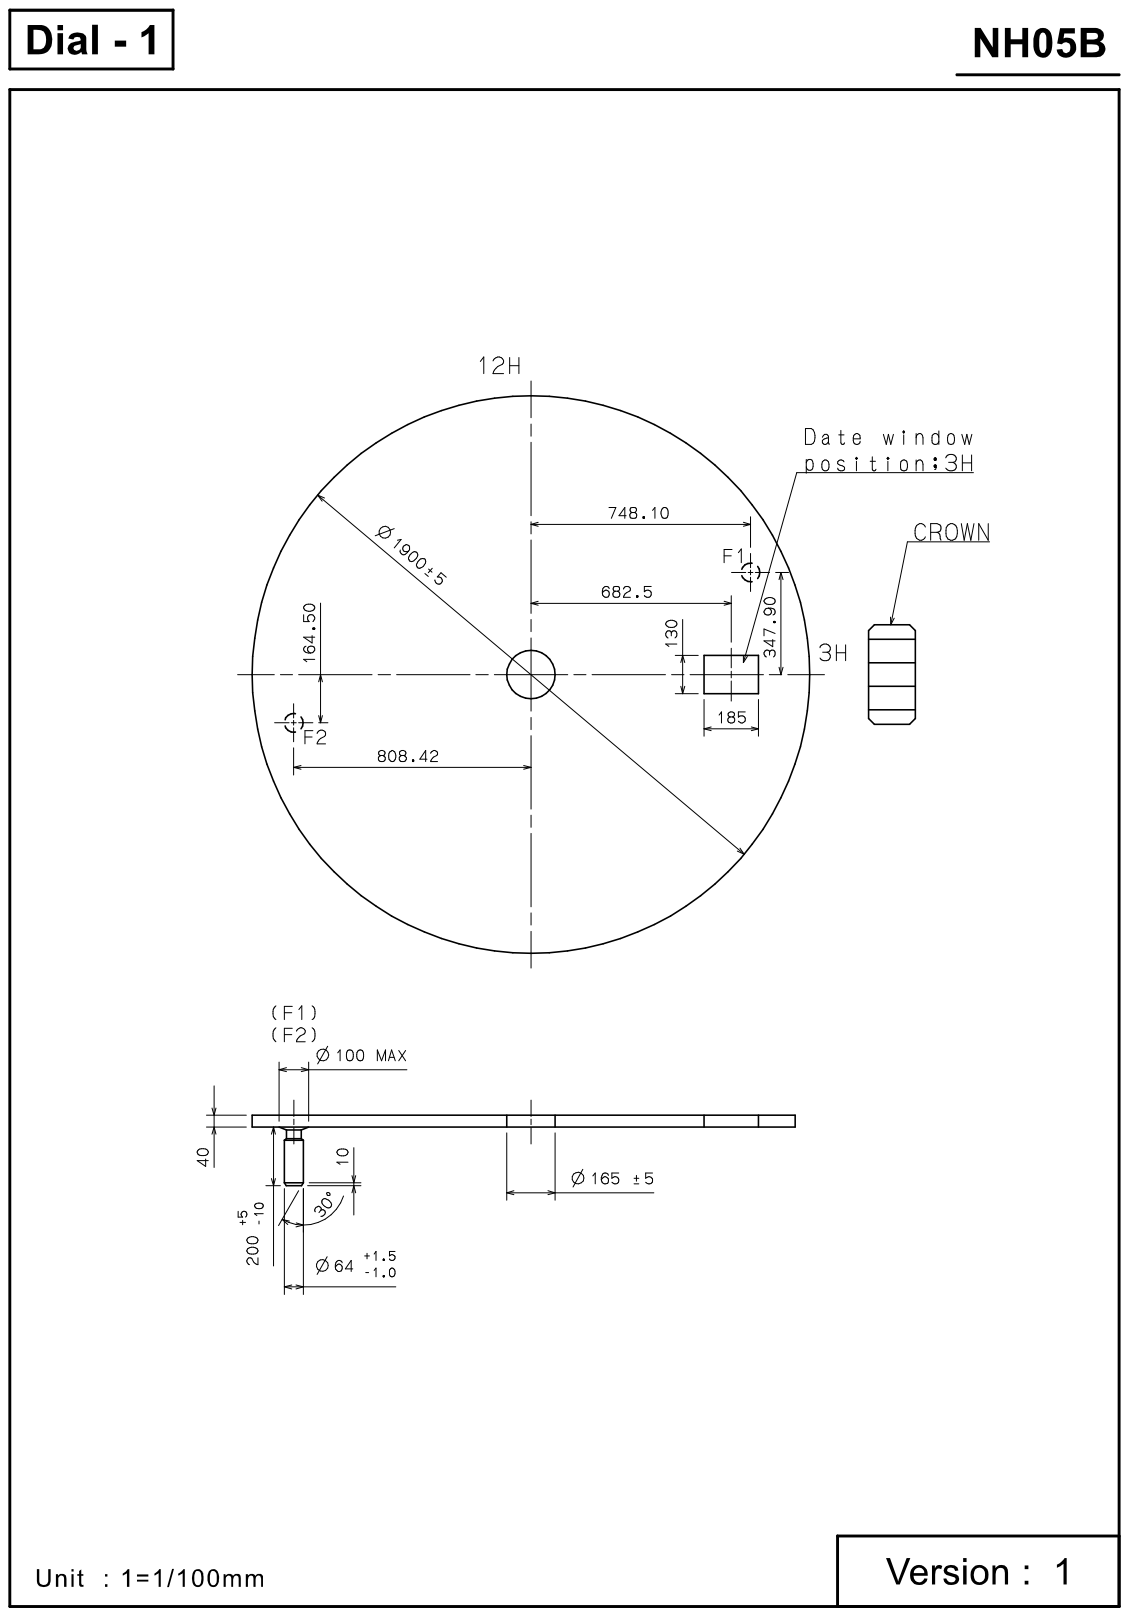
[picture p110: page 8]

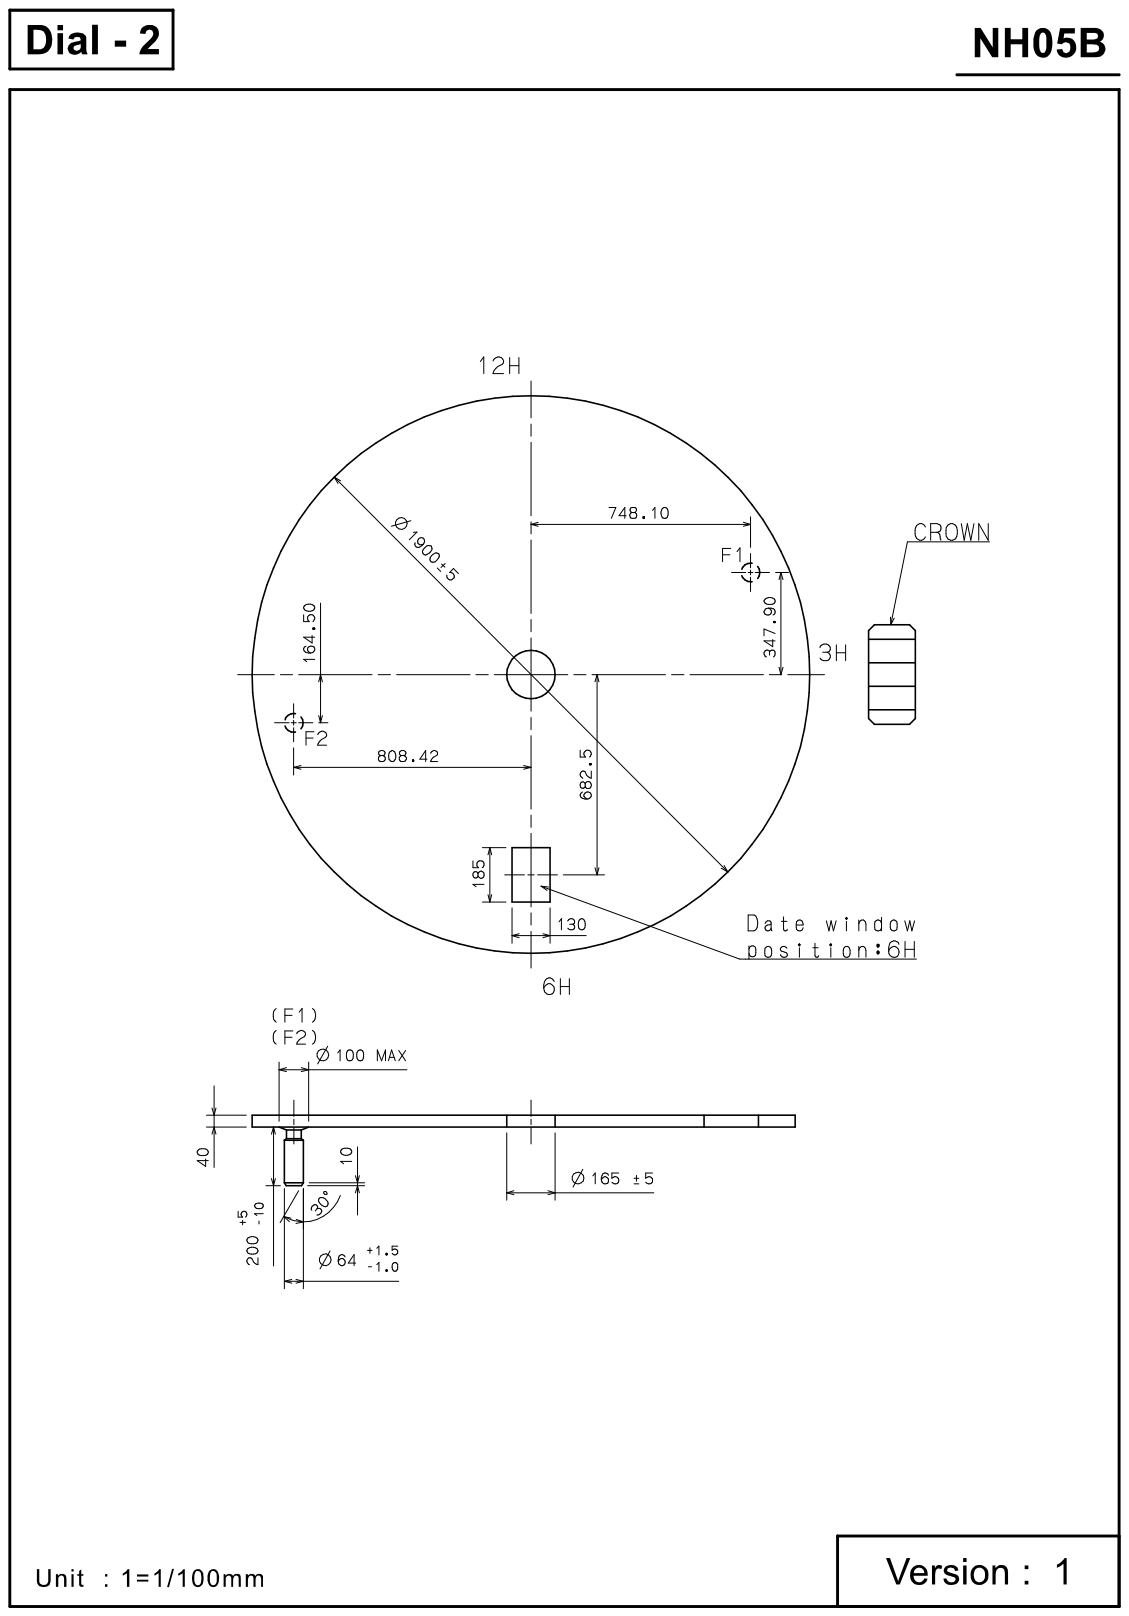
[picture p111: page 9]

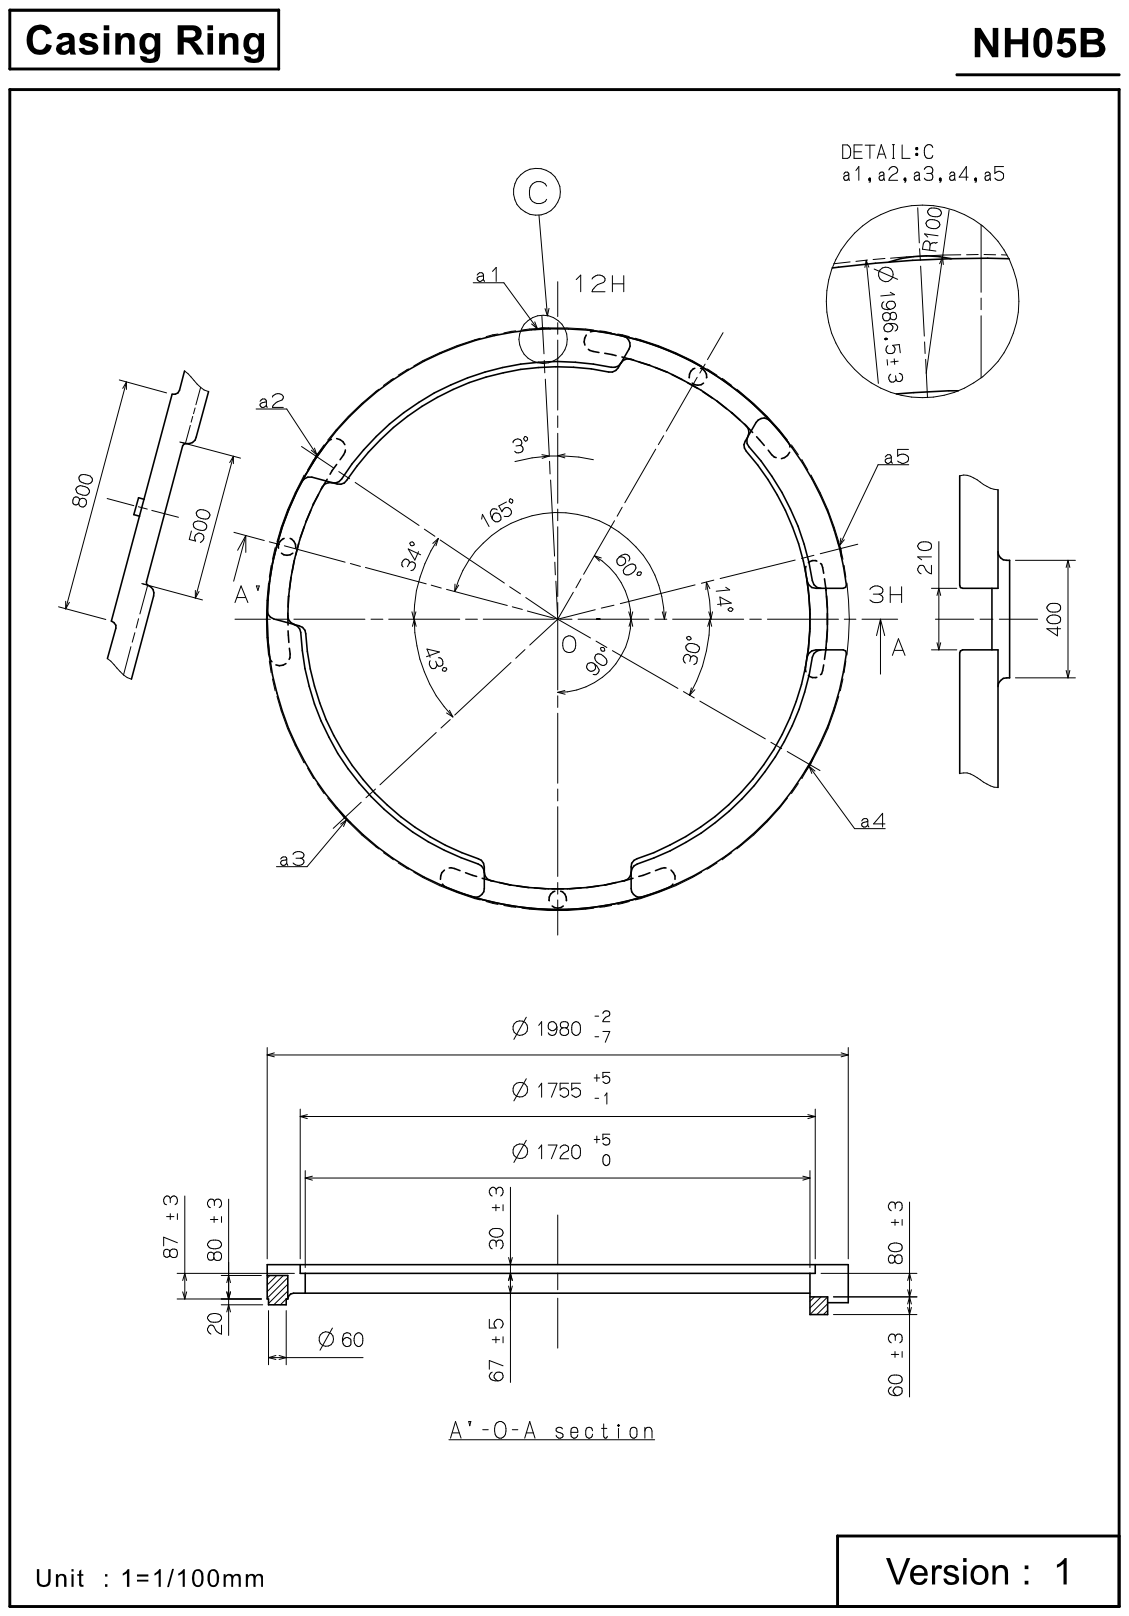
[picture p112: page 10]

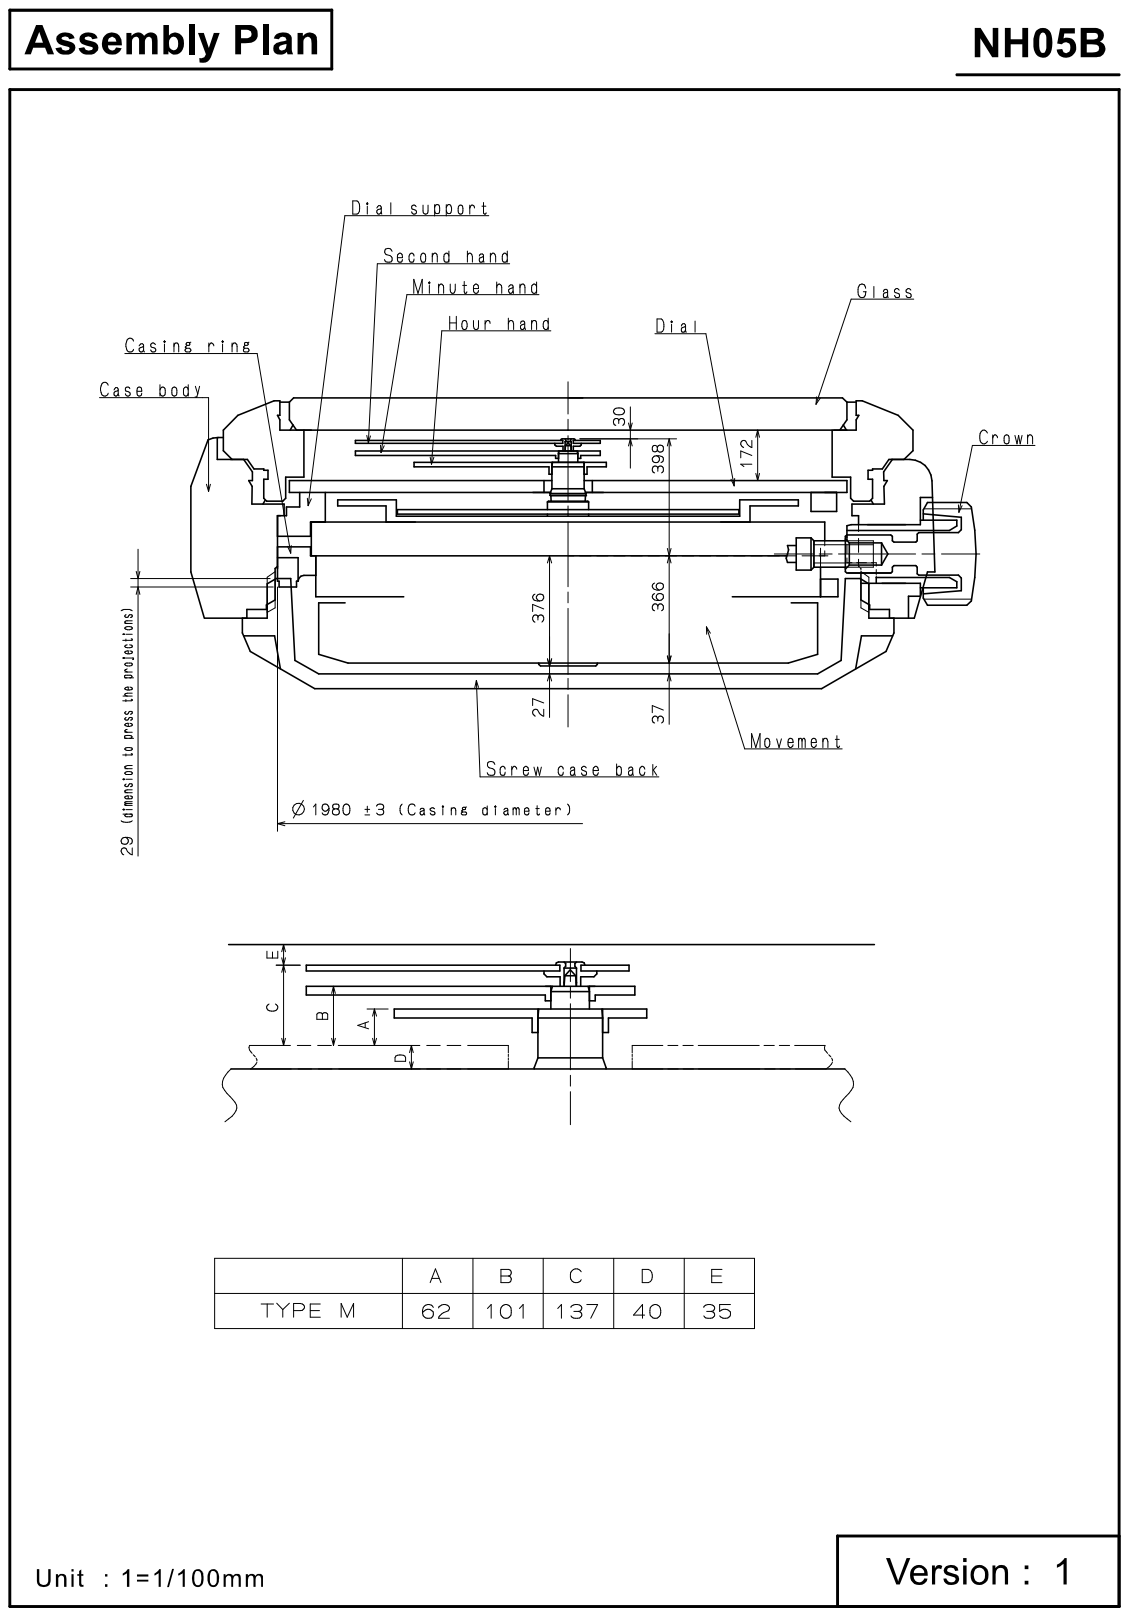
[picture p113: page 11]

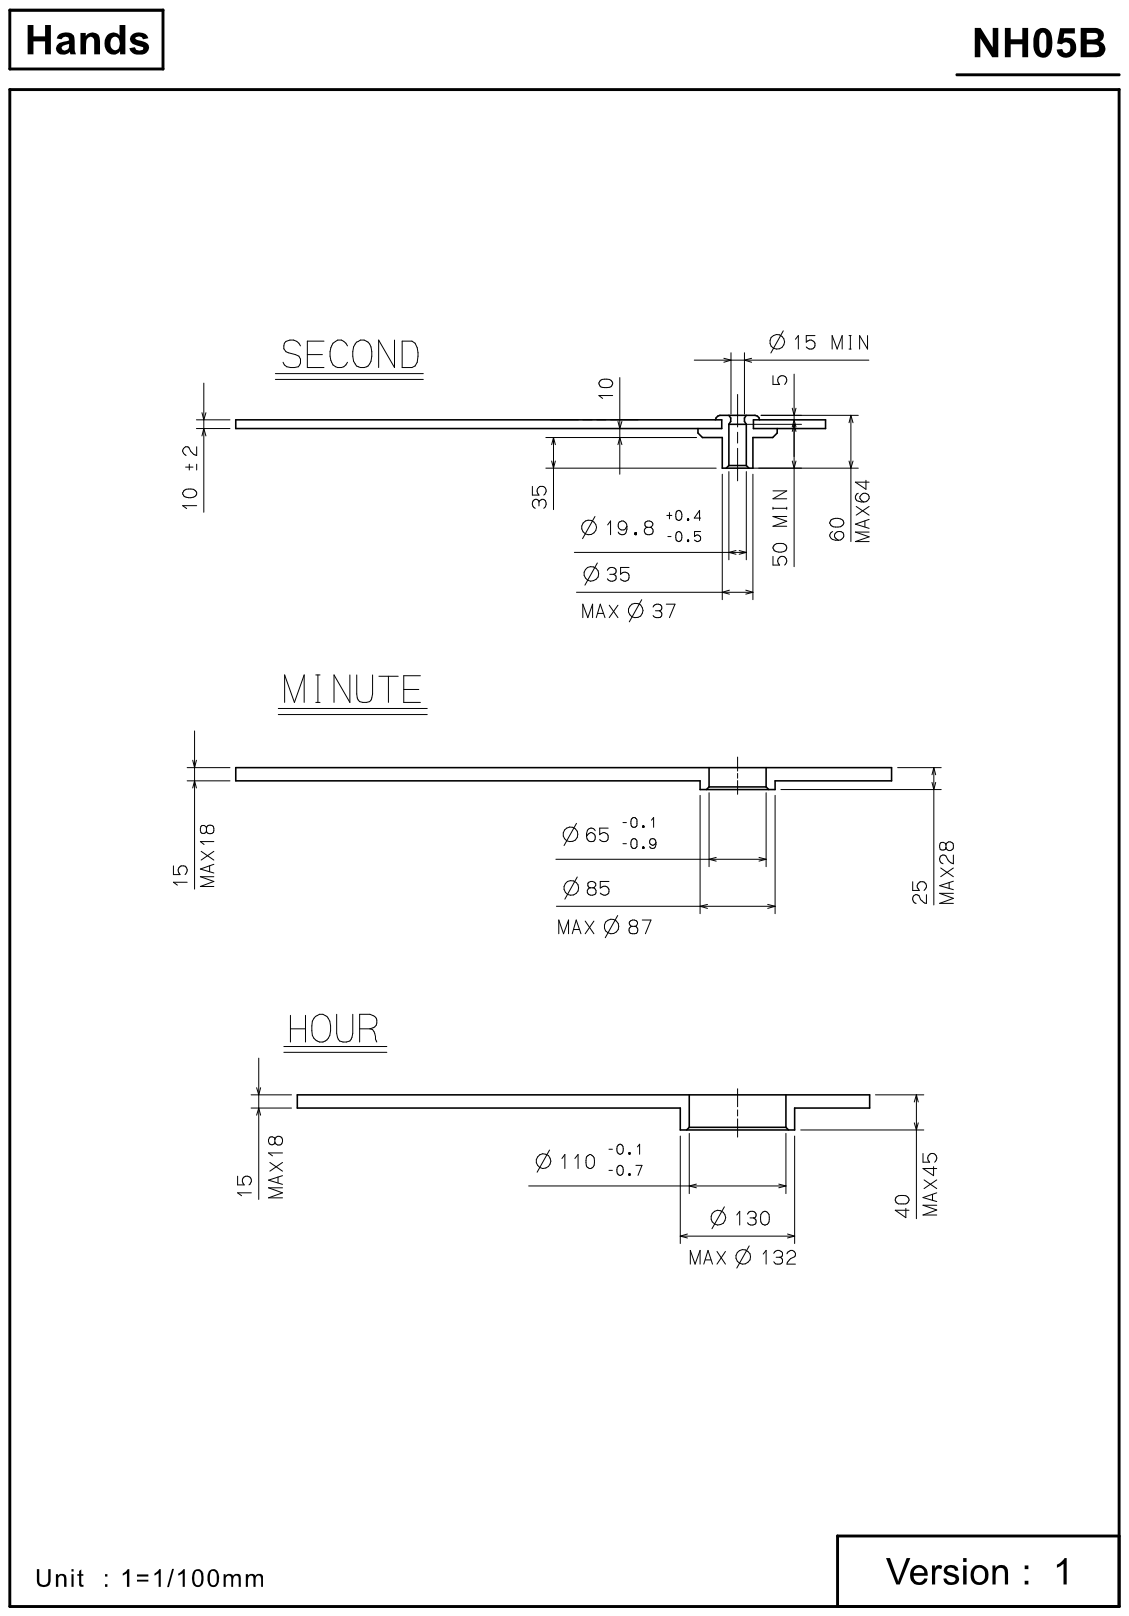
[picture p114: page 12]
