201590022033/Dial-New-Design.01/docs/research/crown-c0-2026-10-10/NH05_TG.pdf

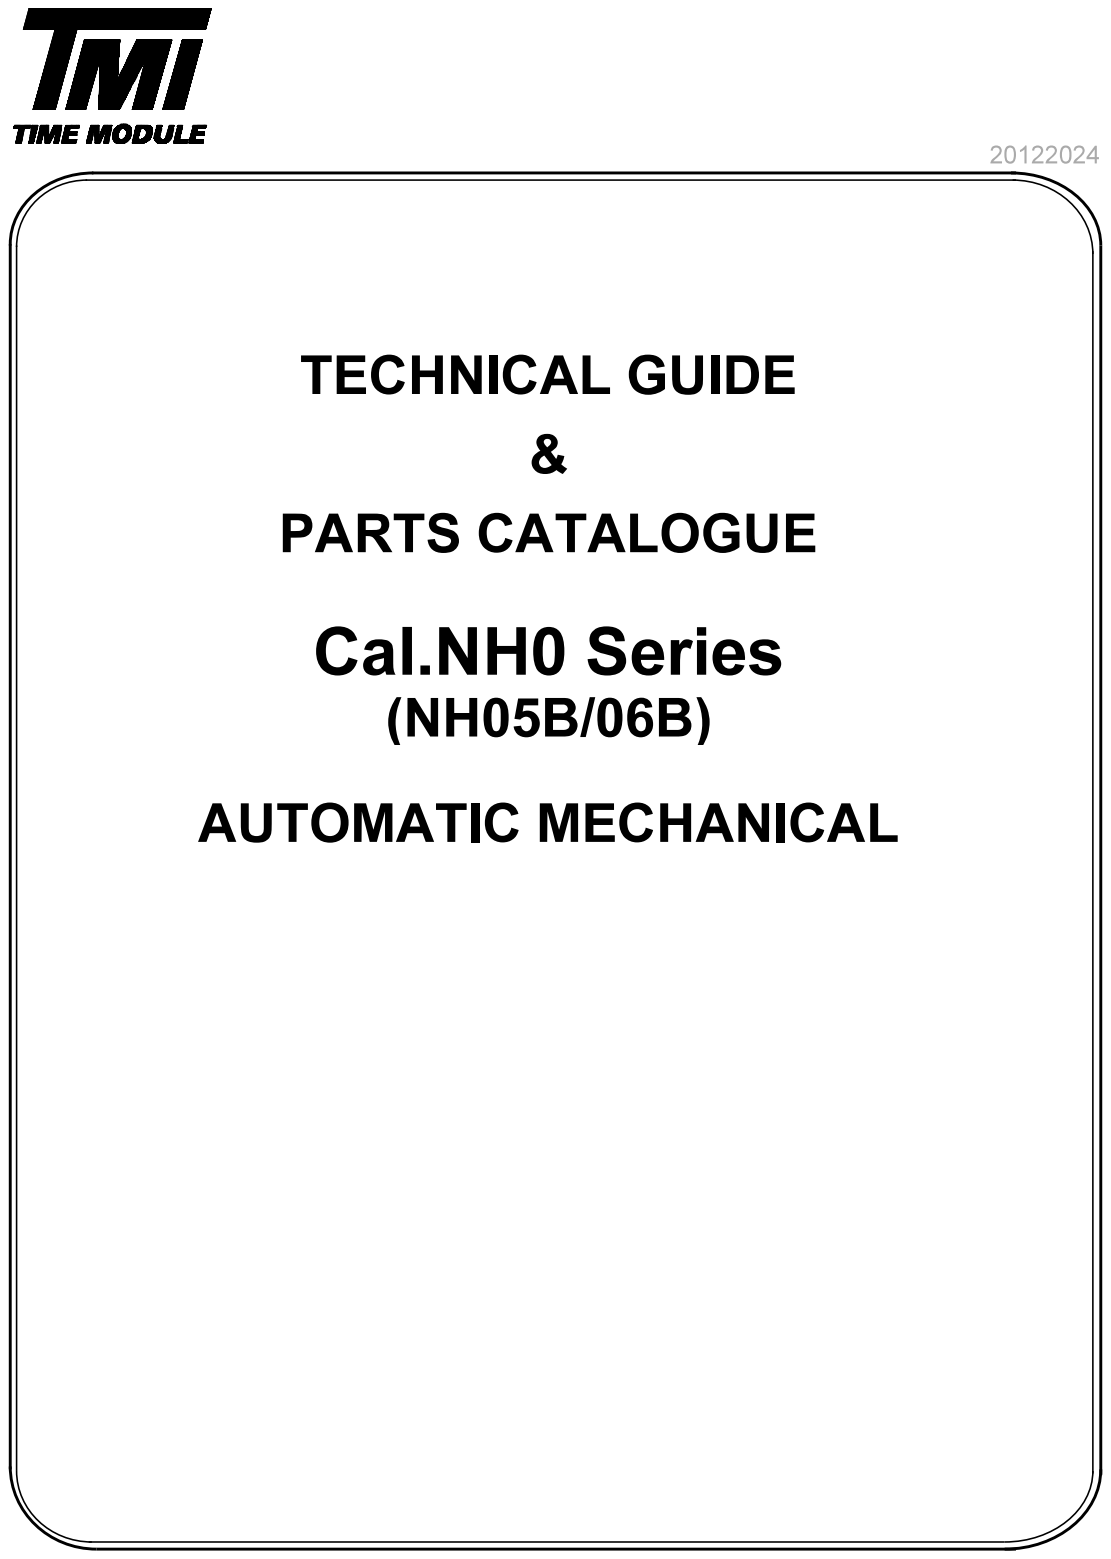
[picture p115: page 1]

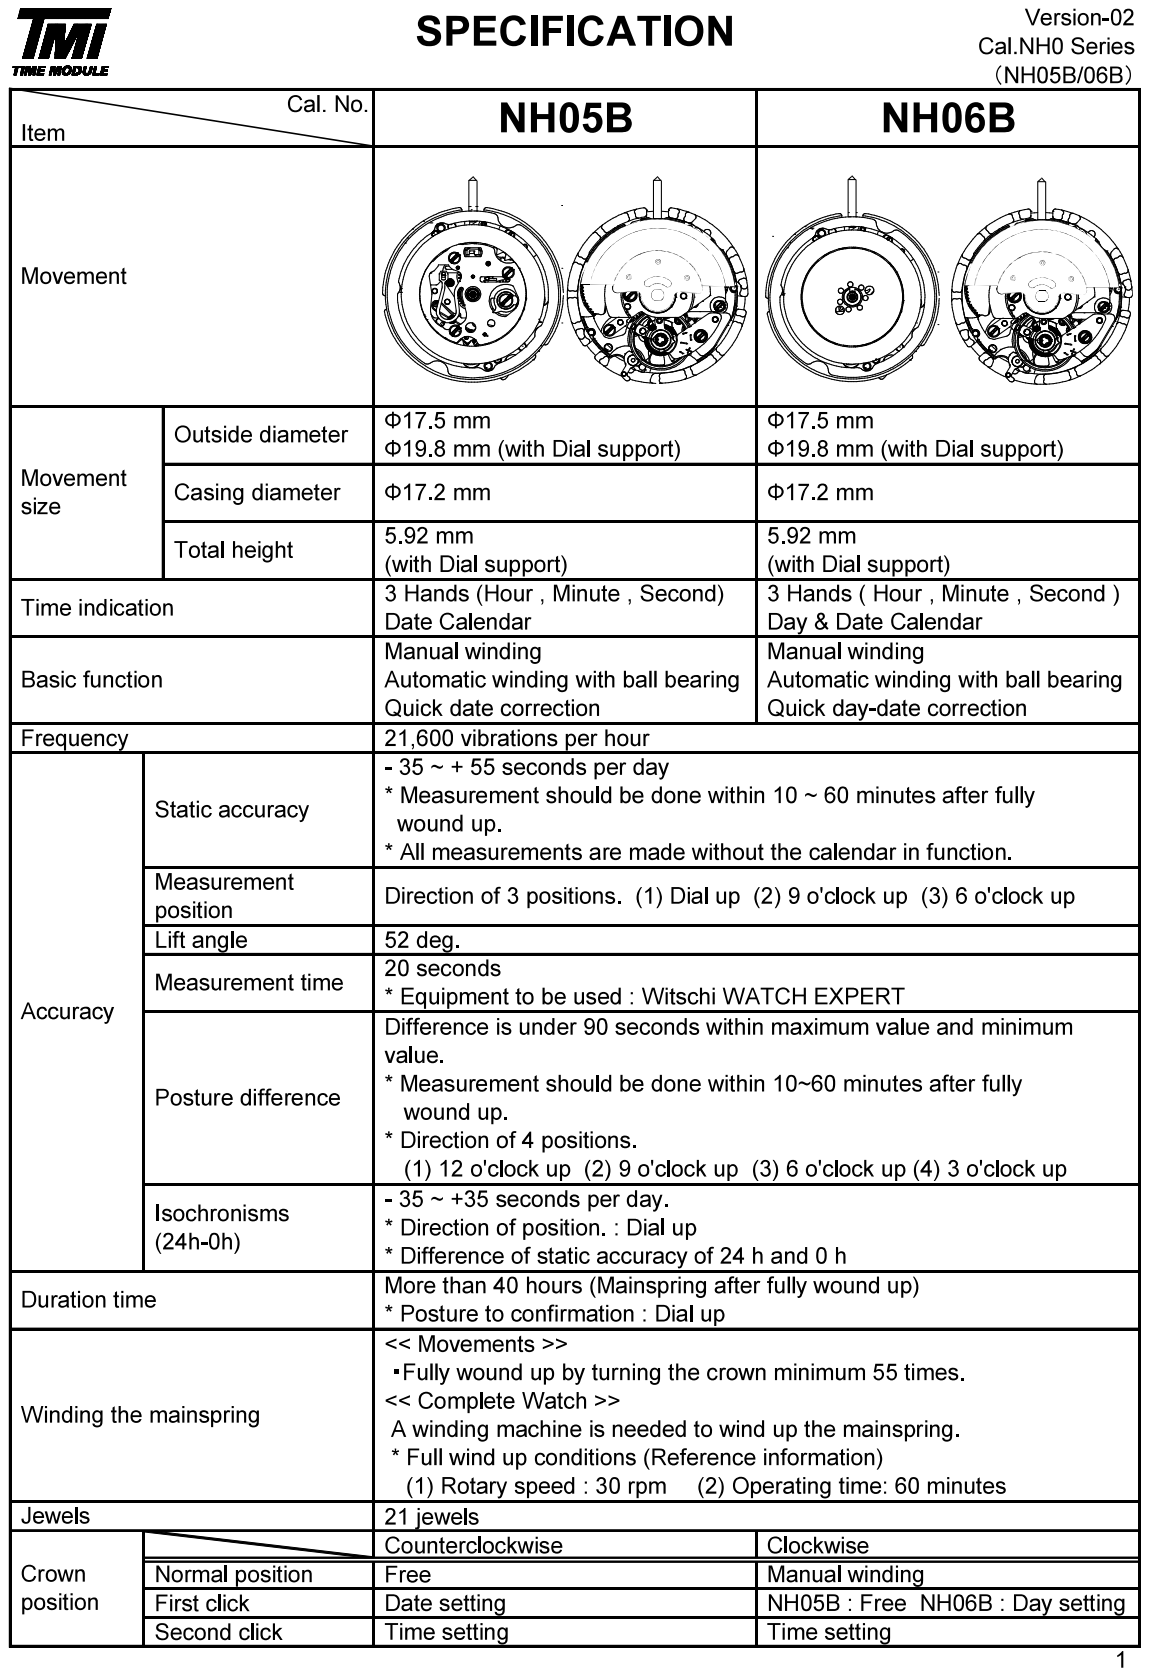
[picture p116: page 2]

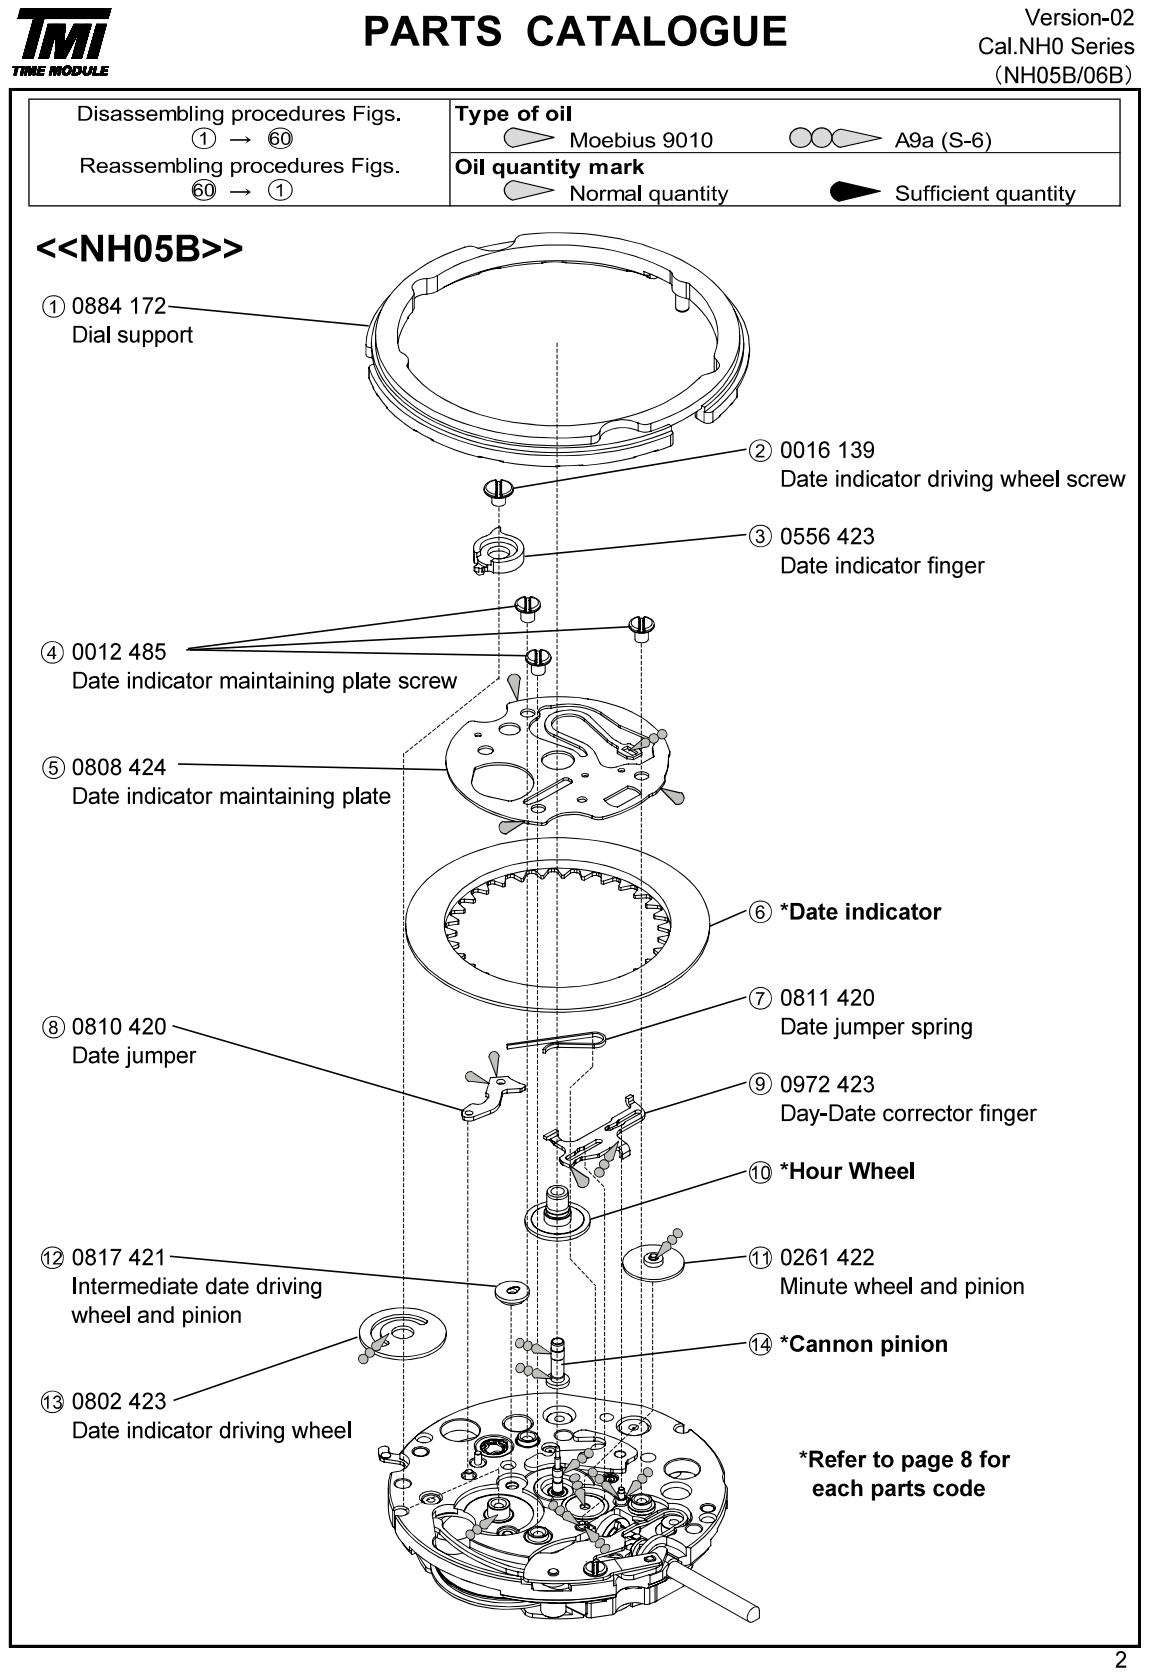
[picture p117: page 3]

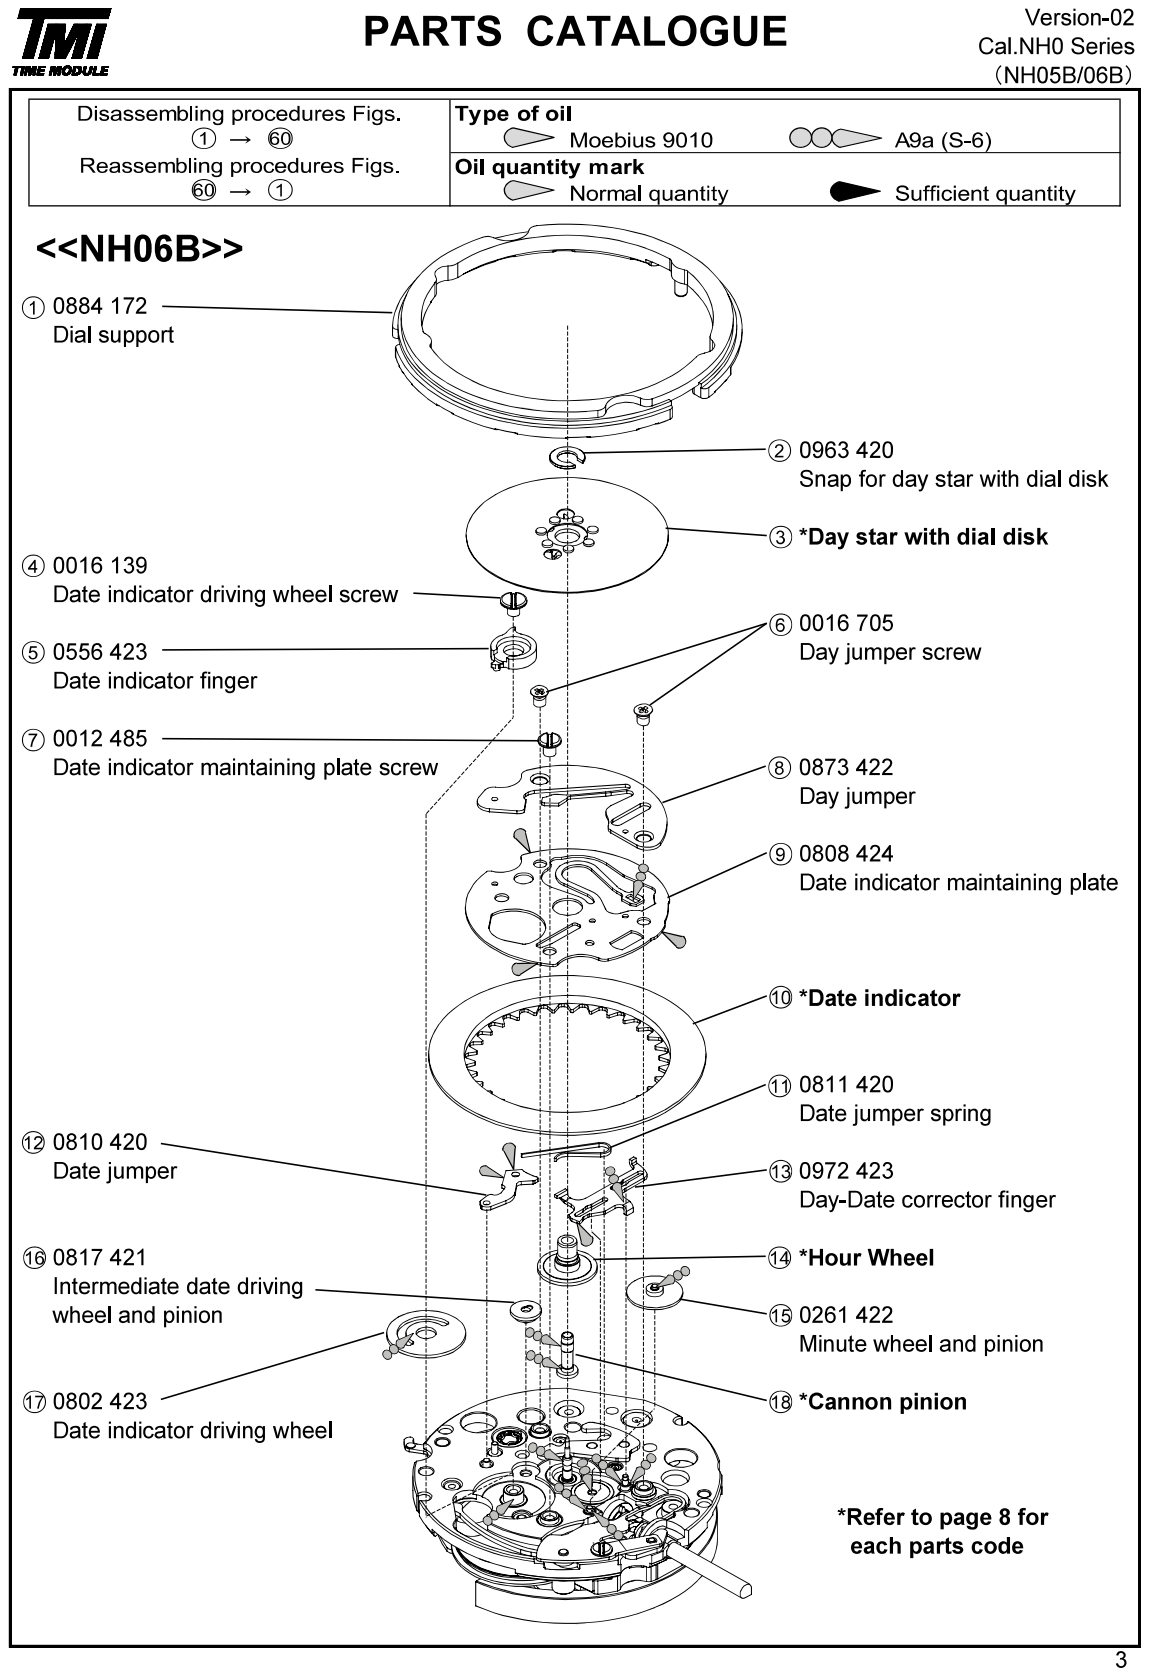
[picture p118: page 4]

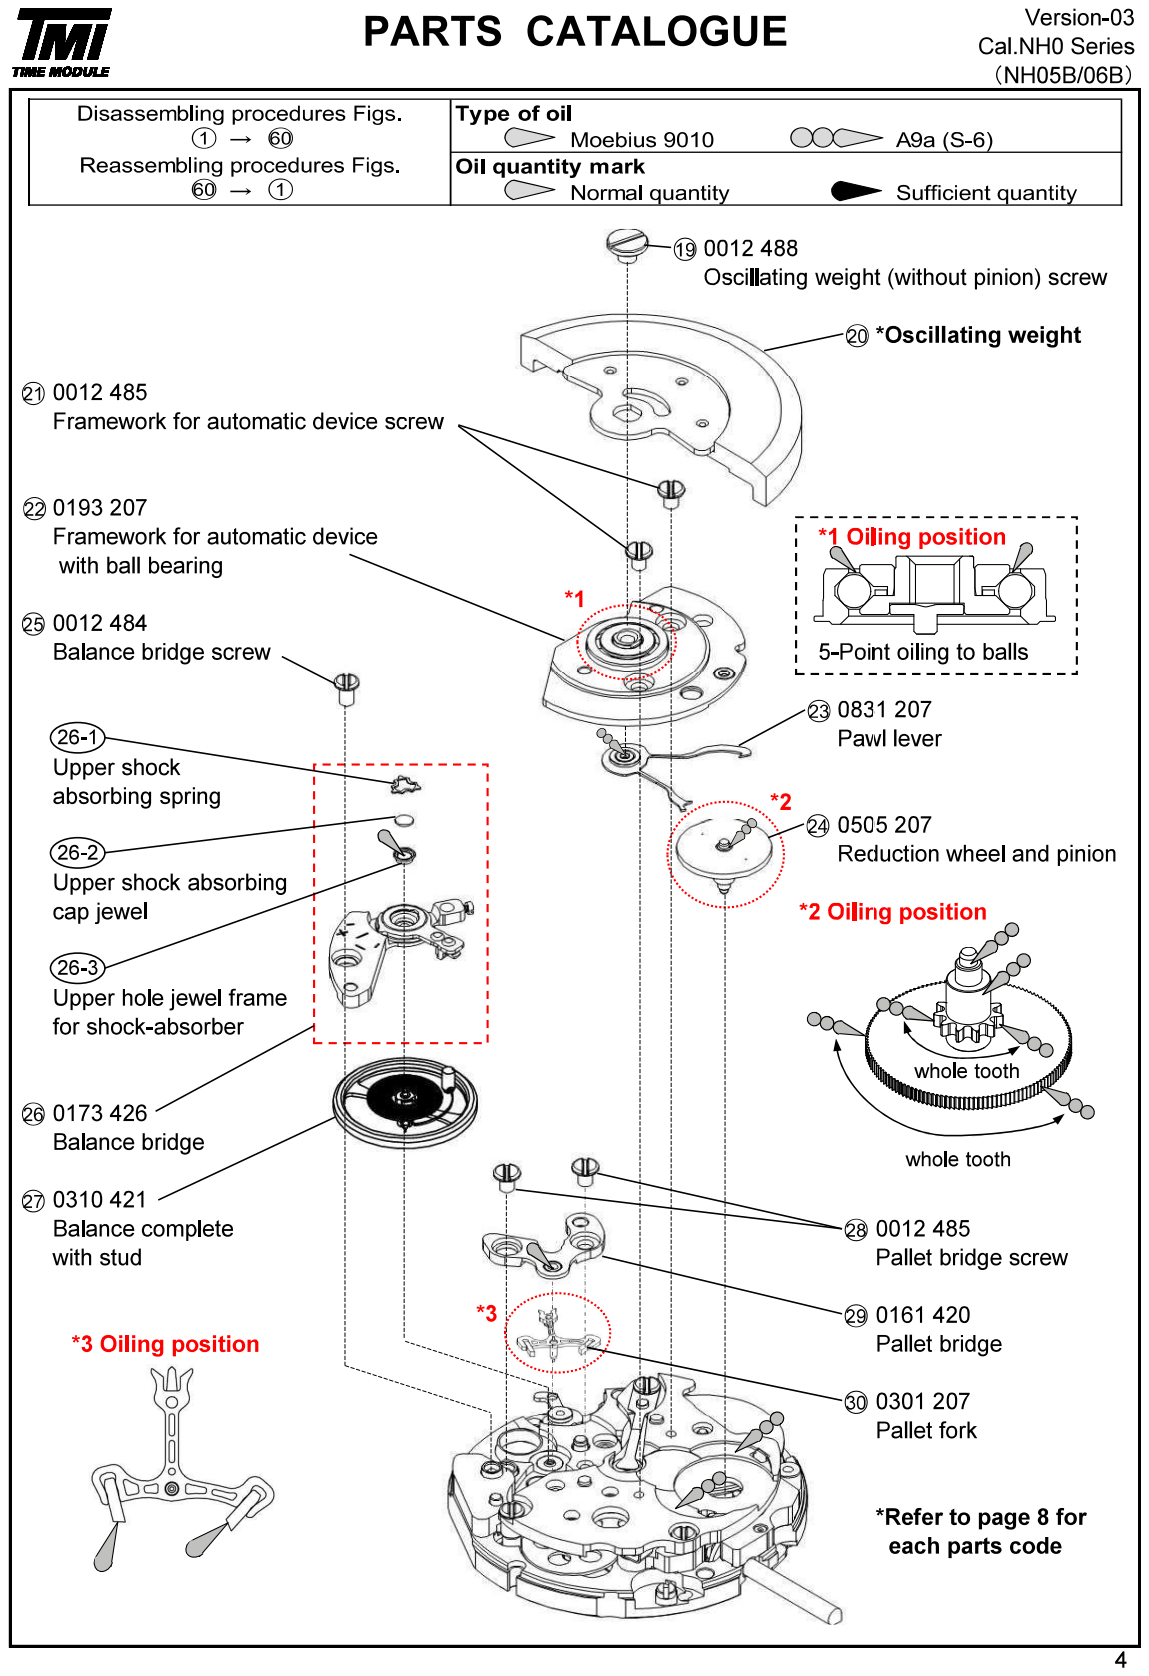
[picture p119: page 5]

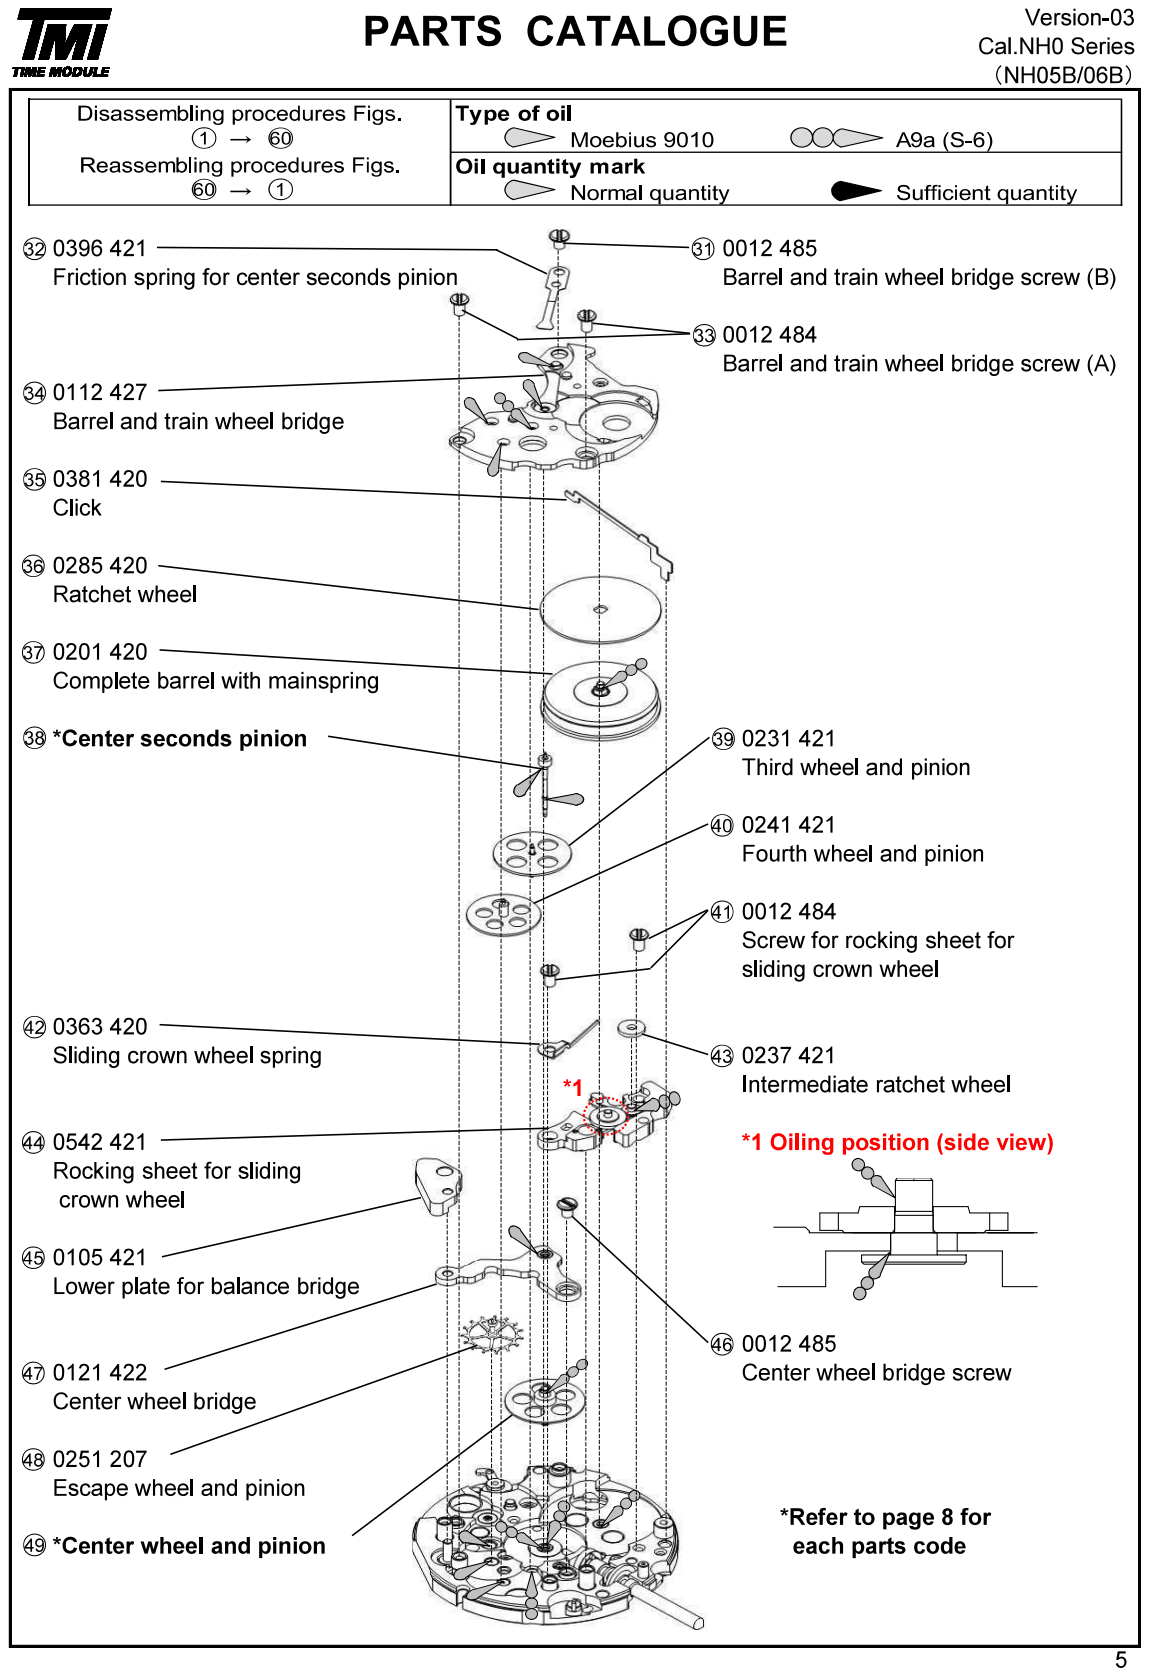
[picture p120: page 6]

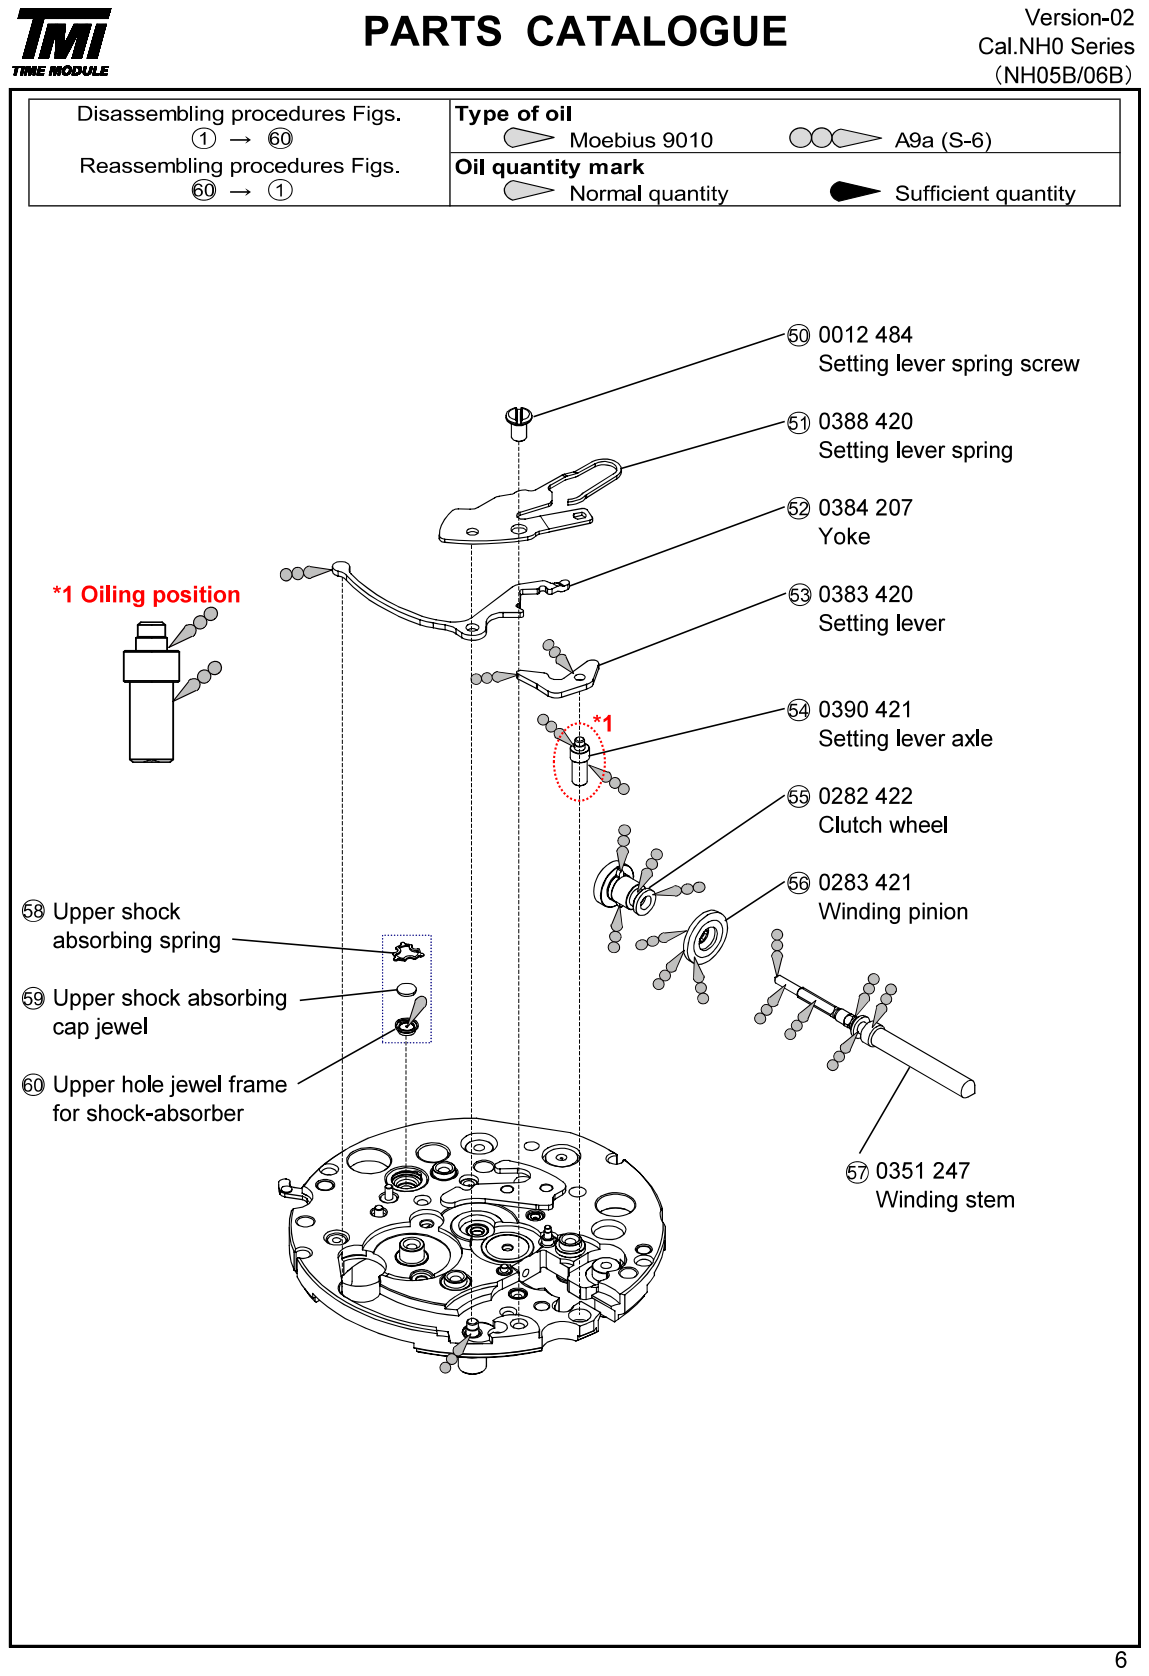
[picture p121: page 7]

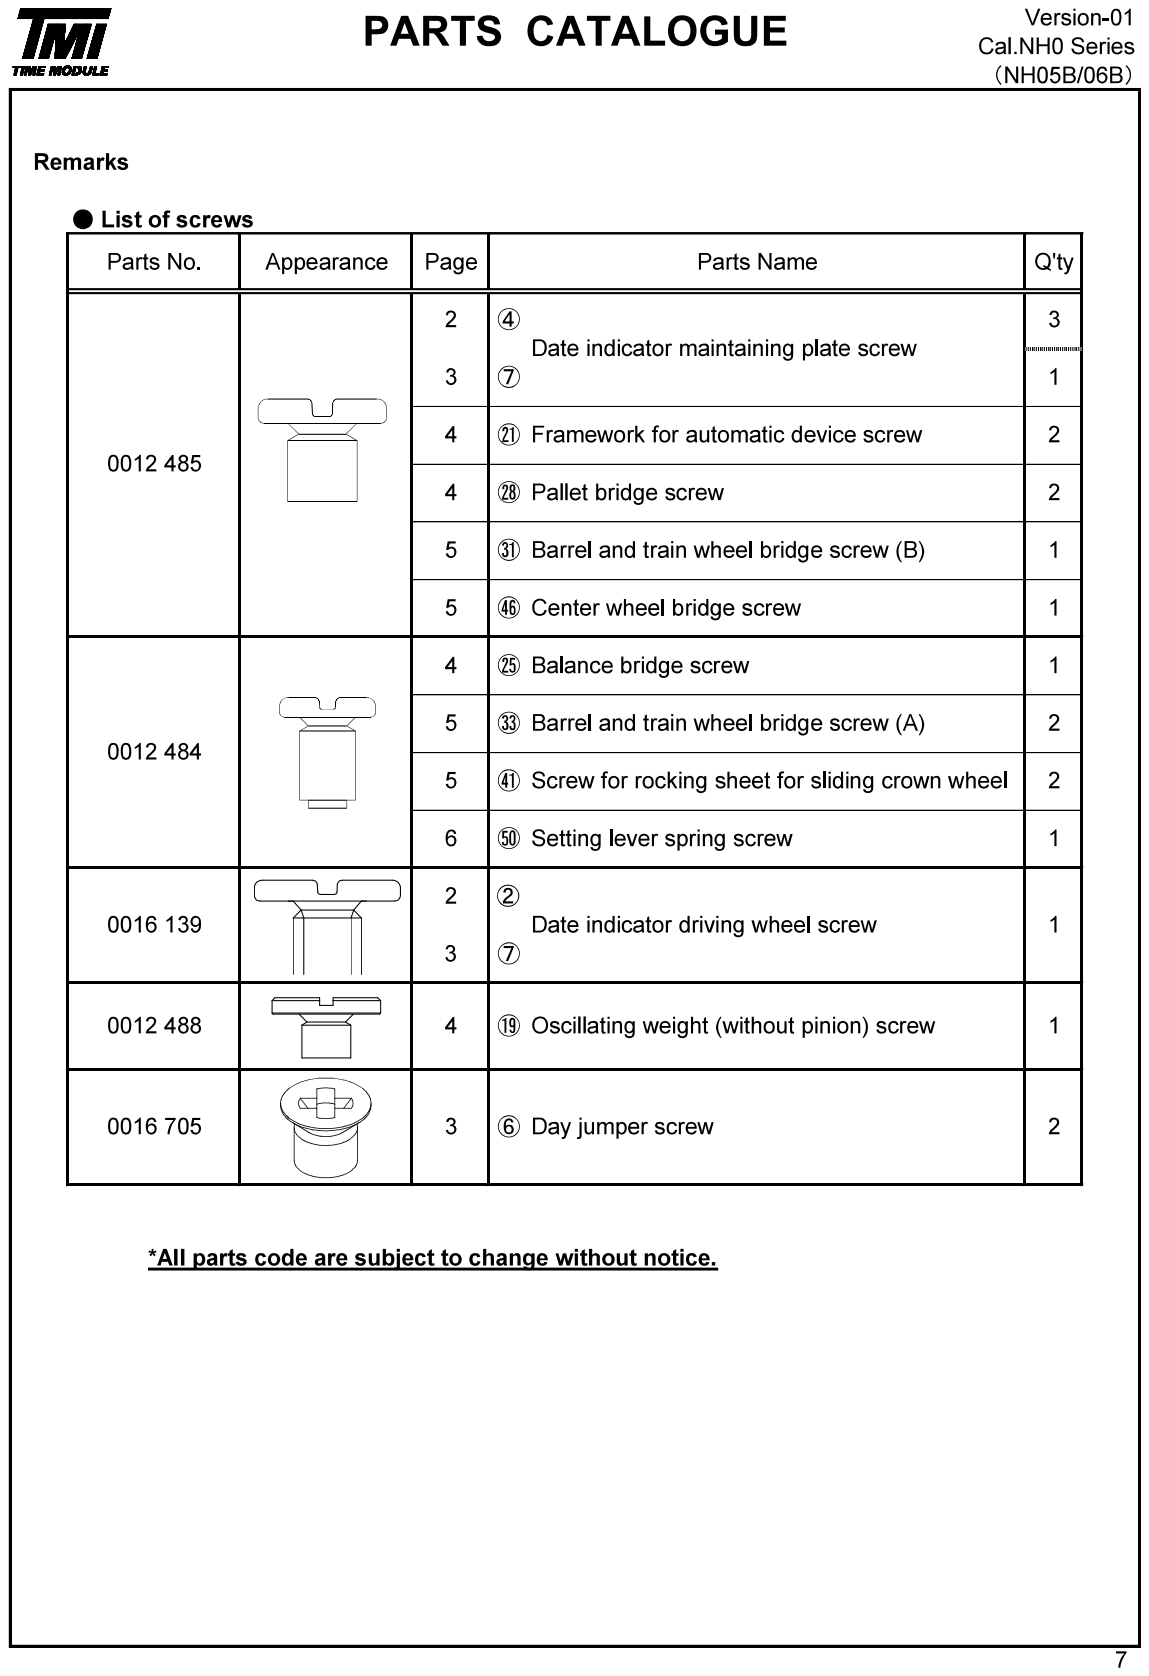
[picture p122: page 8]

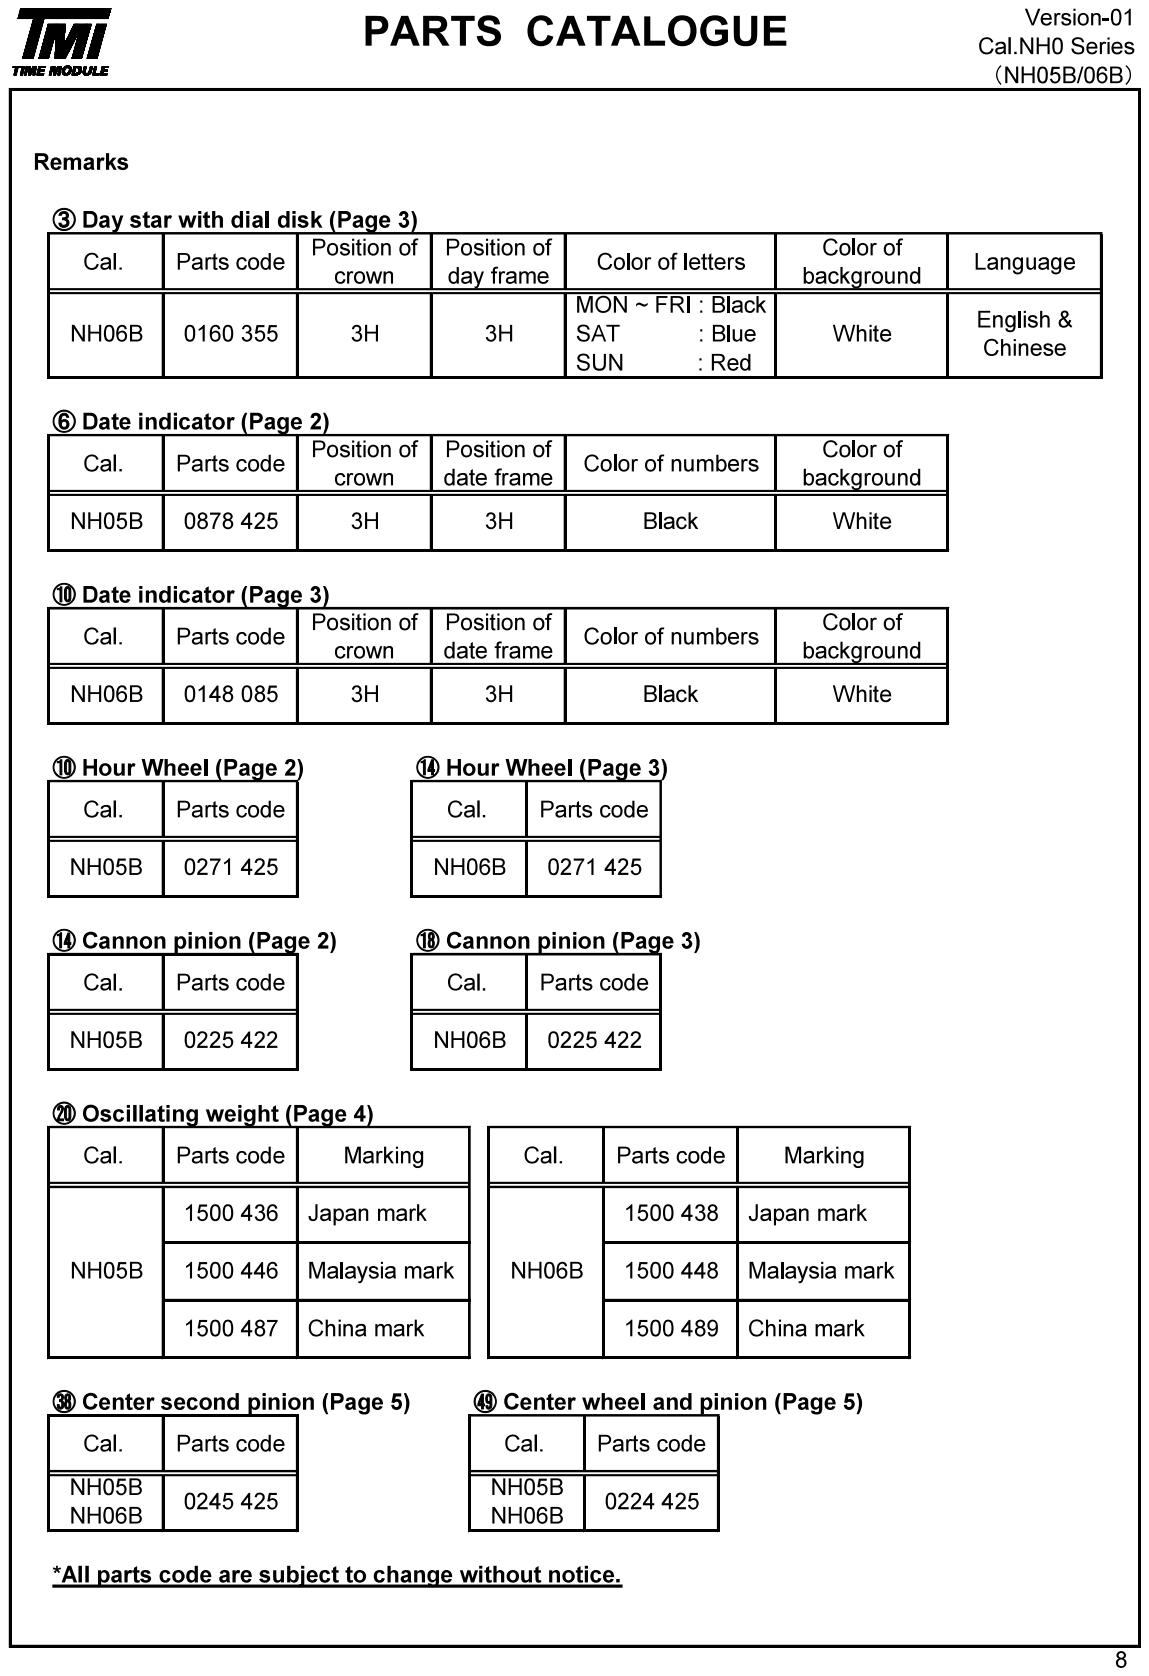
[picture p123: page 9]

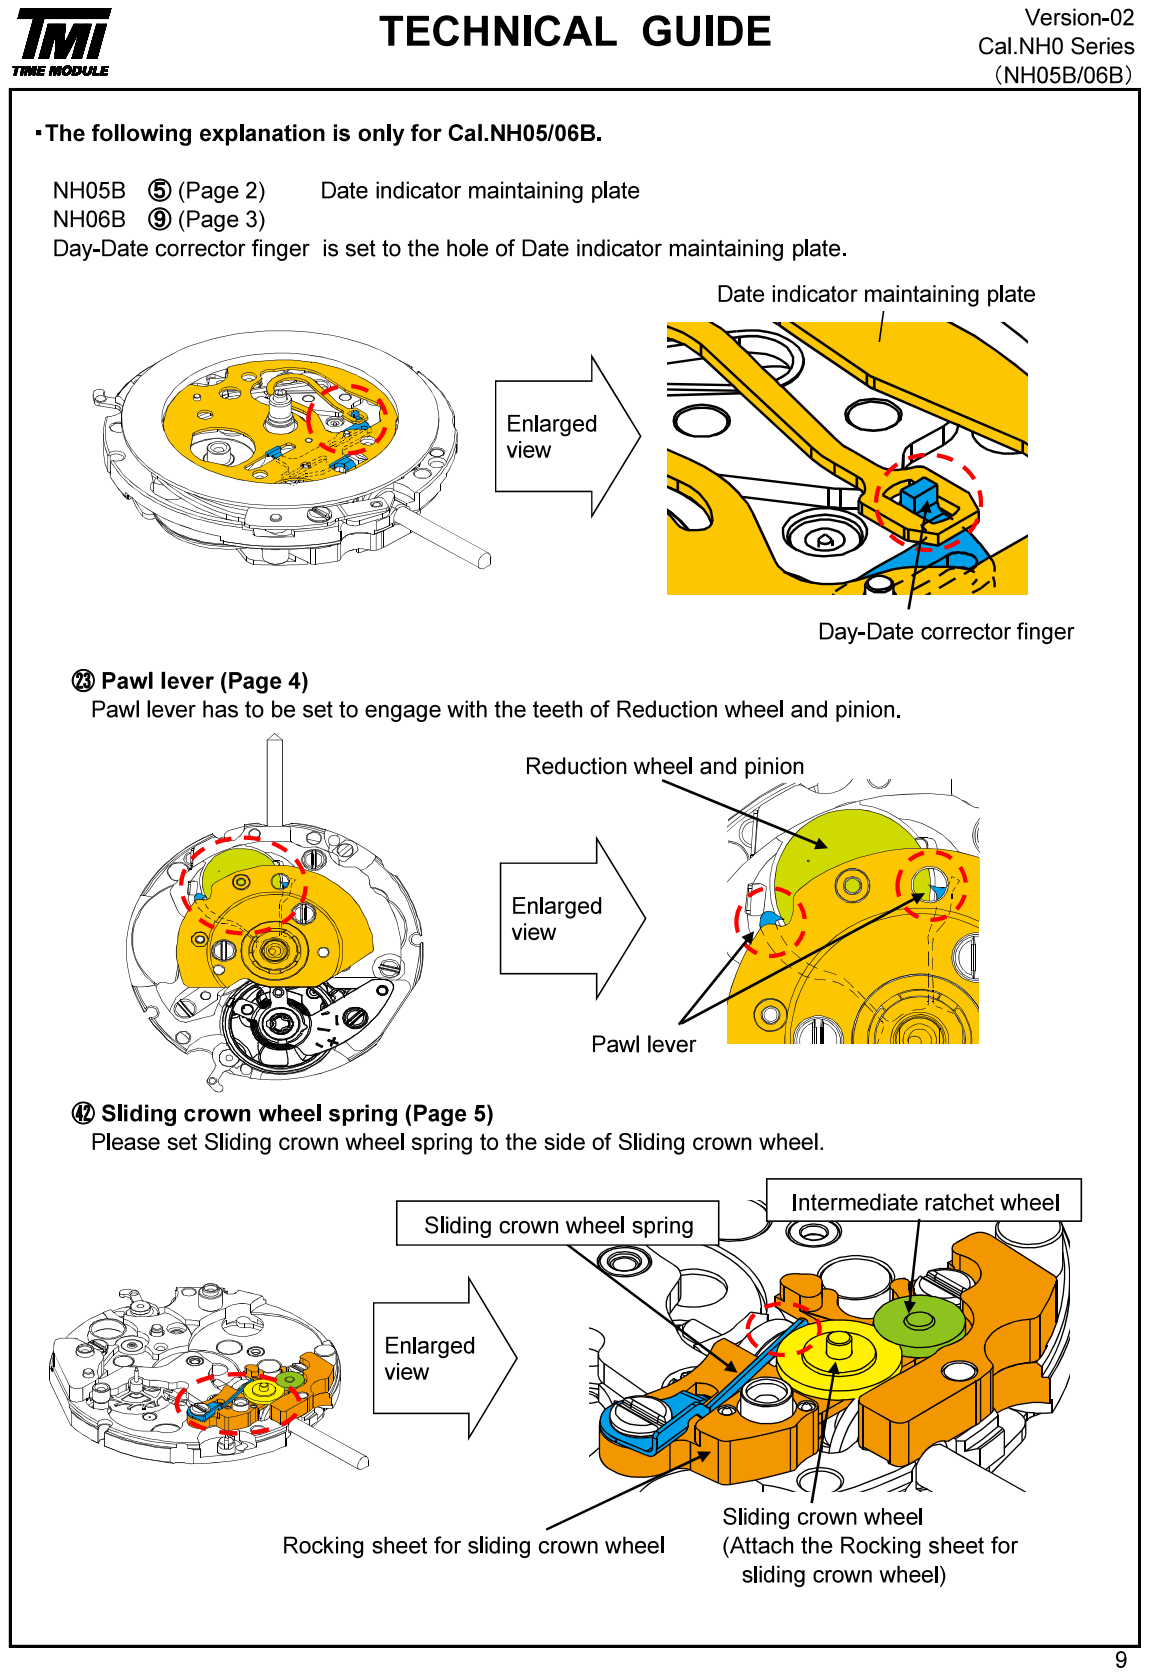
[picture p124: page 10]

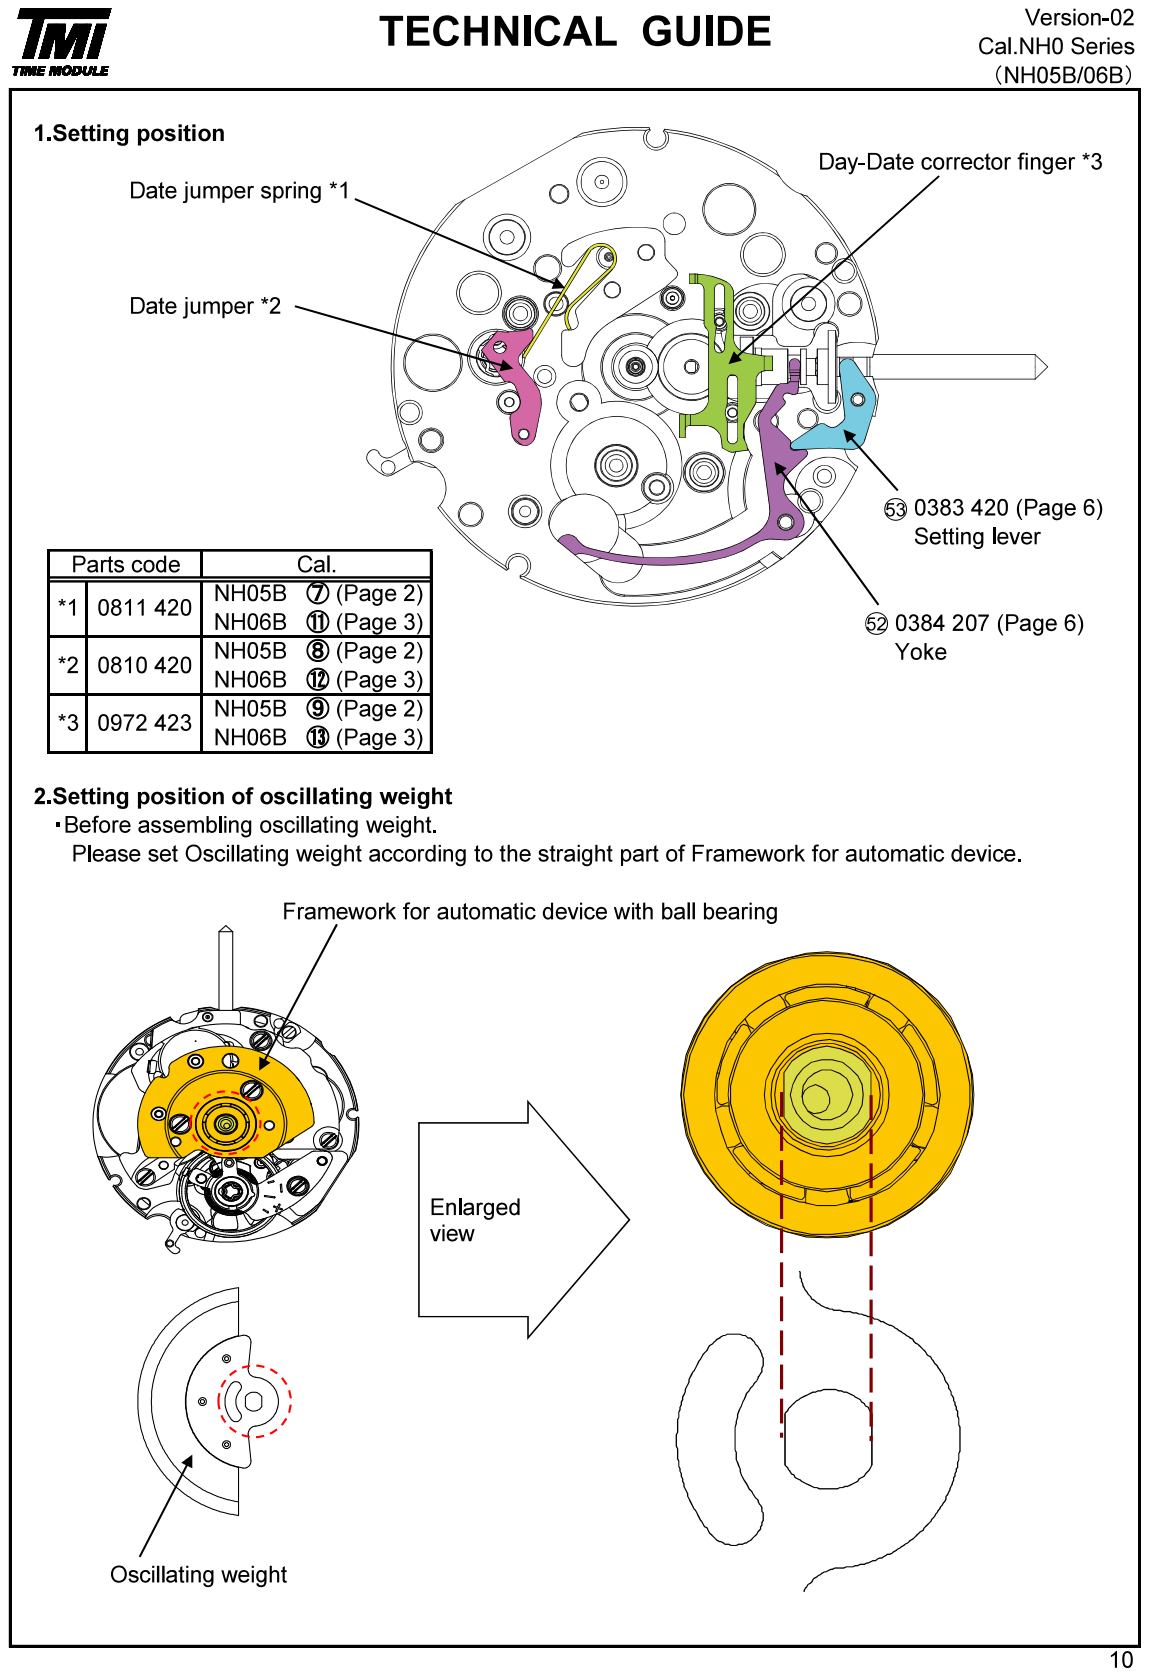
[picture p125: page 11]

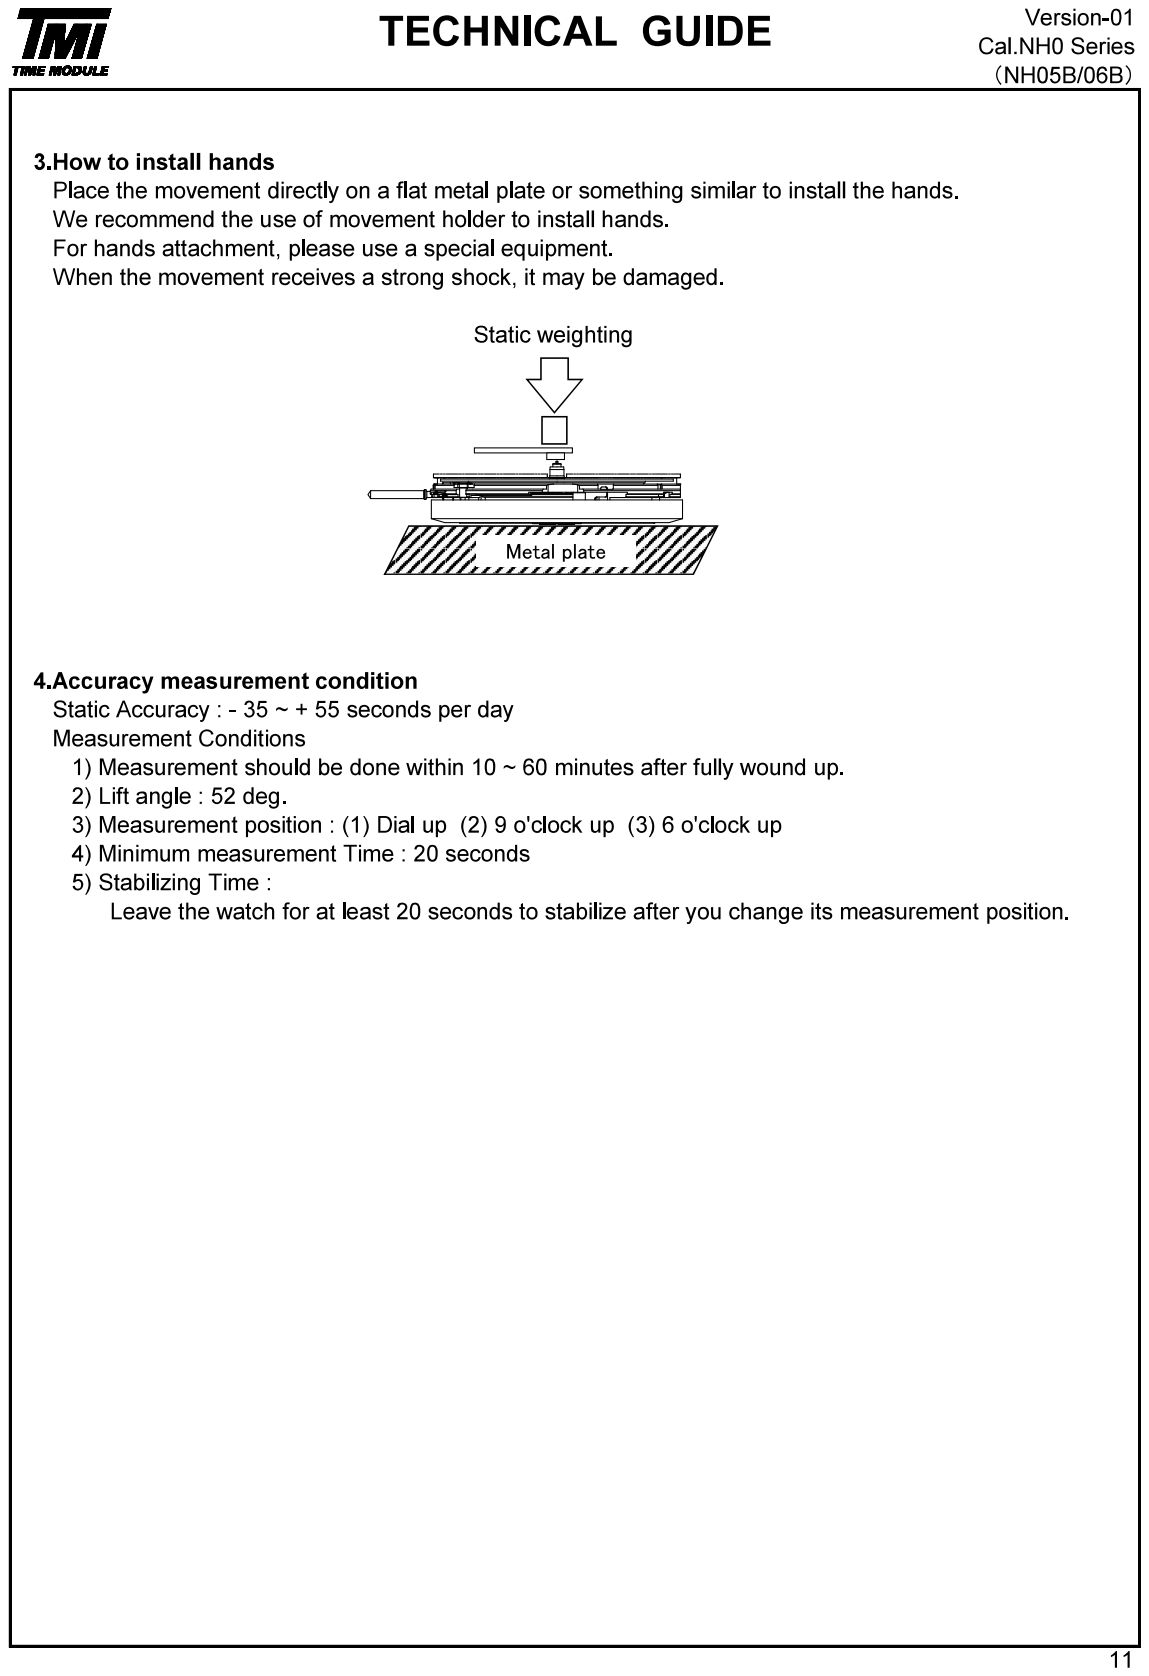
[picture p126: page 12]

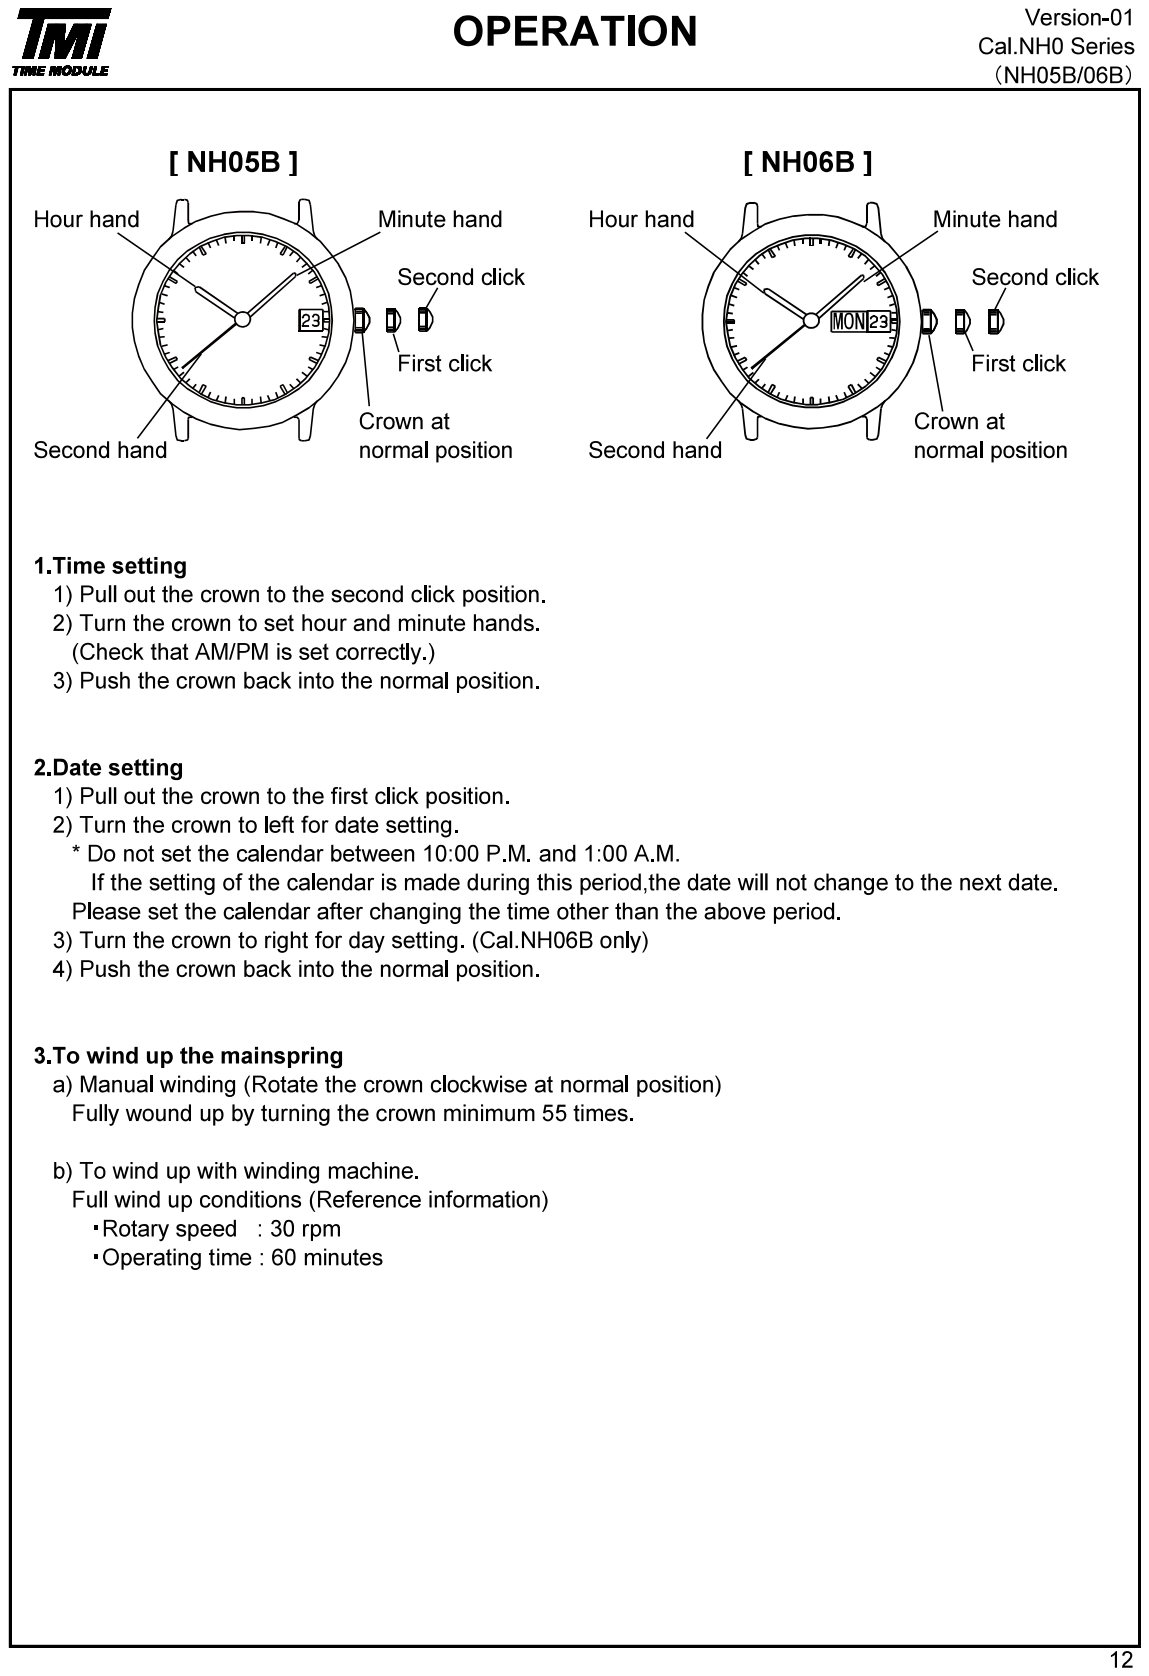
[picture p127: page 13]
